AndyChiu/hotswap_pcb_generator/img_UTP/IMG_20230121_120708471~2.jpg

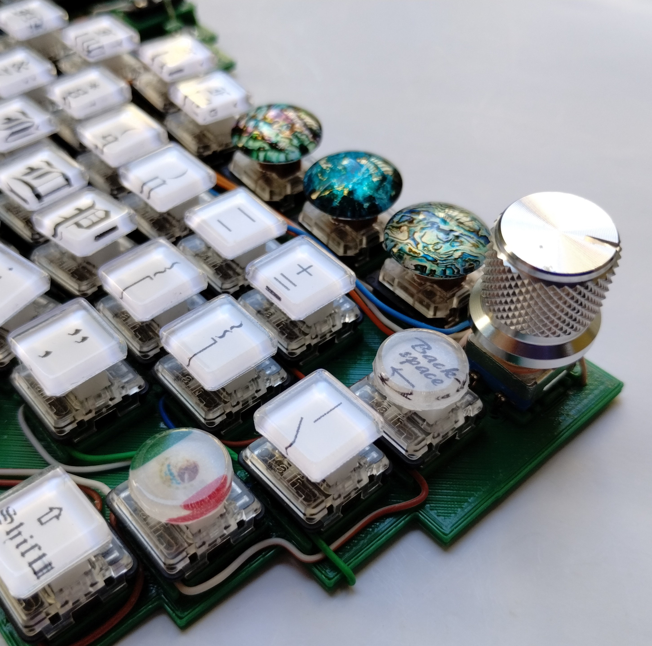
img_UTP/IMG_20230121_120708471~2.jpg
