AndyChiu/hotswap_pcb_generator/example_layouts_UTP/Willow-3x6+Esrille-thumb-3x1_(V2 Curve)/pcb_Willow-3x6-Esrille-thumb-3x1_(V2 Curve)_R.stl

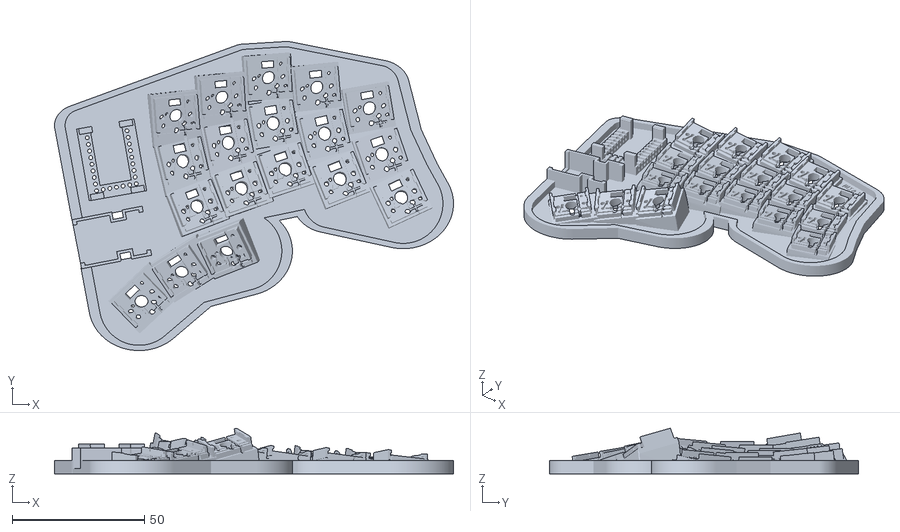
[picture p60: CAD file, 2024-08-21]
example_layouts_UTP/Willow-3x6+Esrille-thumb-3x1_(V2 Curve)/pcb_Willow-3x6-Esrille-thumb-3x1_(V2 Curve)_R.stl
150.7 x 116.7 x 17.2
