AndyChiu/hotswap_pcb_generator/scad_UTP/Curved_PCB_KB/STL/11.3MM_LType/BasePlate_3U_11.3MM_LType_Left.stl

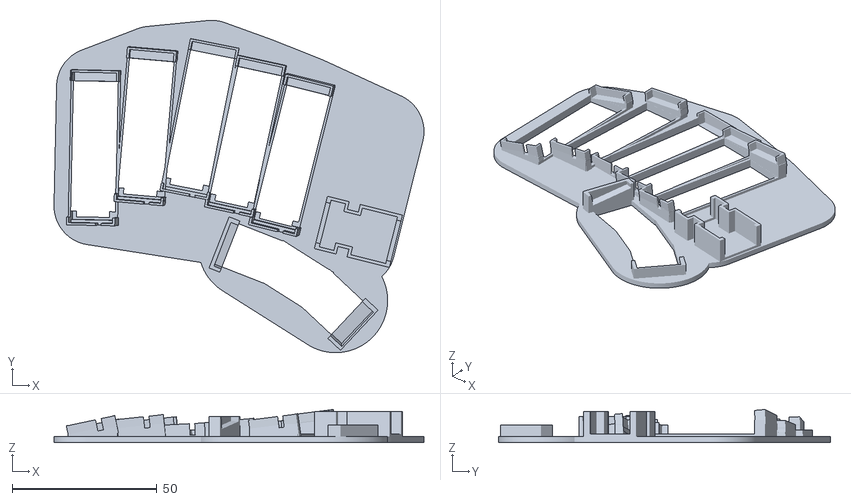
[picture p61: CAD file, 2024-03-19]
scad_UTP/Curved_PCB_KB/STL/11.3MM_LType/BasePlate_3U_11.3MM_LType_Left.stl
127.9 x 114.9 x 11.4
