AndyChiu/hotswap_pcb_generator/scad_UTP/Curved_PCB_KB/STL/13MM_MType/Curved_PCB(UC36_3U)_M_13mm.stl

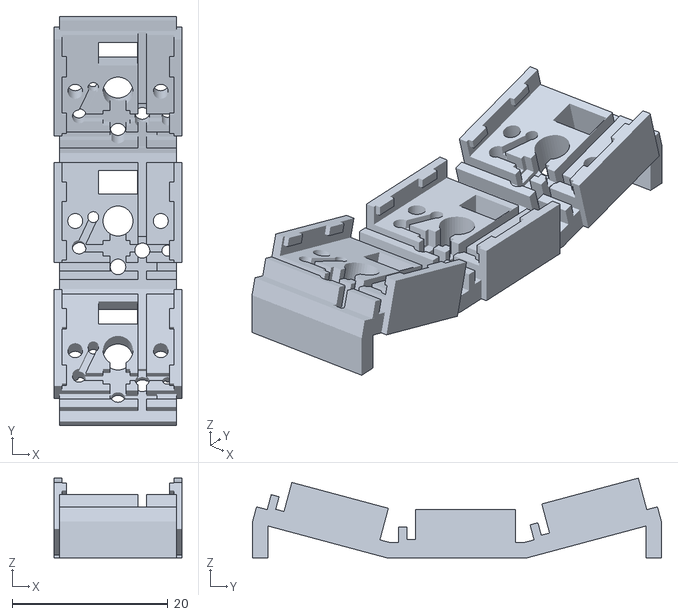
[picture p62: CAD file, 2024-03-19]
scad_UTP/Curved_PCB_KB/STL/13MM_MType/Curved_PCB(UC36_3U)_M_13mm.stl
16.4 x 52.6 x 10.3
