AndyChiu/hotswap_pcb_generator/scad_UTP/Curved_PCB_KB/STL/16MM_MType/BasePlate_3U_16MM_MType_Left.stl

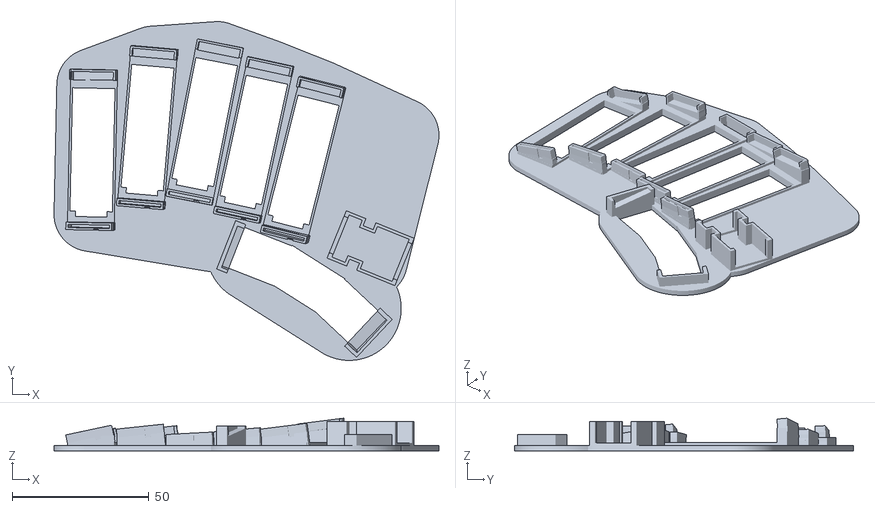
[picture p64: CAD file, 2024-03-19]
scad_UTP/Curved_PCB_KB/STL/16MM_MType/BasePlate_3U_16MM_MType_Left.stl
140.6 x 123.7 x 11.9
