AndyChiu/hotswap_pcb_generator/scad_UTP/Curved_PCB_KB/STL/18MM_LType/BasePlate_3U_18MM_LType_Right.stl

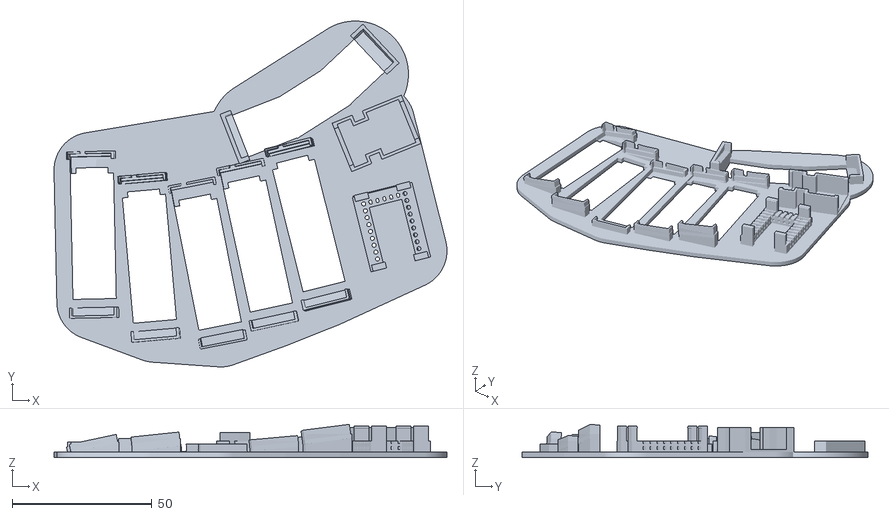
[picture p65: CAD file, 2024-03-19]
scad_UTP/Curved_PCB_KB/STL/18MM_LType/BasePlate_3U_18MM_LType_Right.stl
140.6 x 123.7 x 11.9
