AndyChiu/hotswap_pcb_generator/scad_UTP/IDC/STL/IDC_Holder.stl

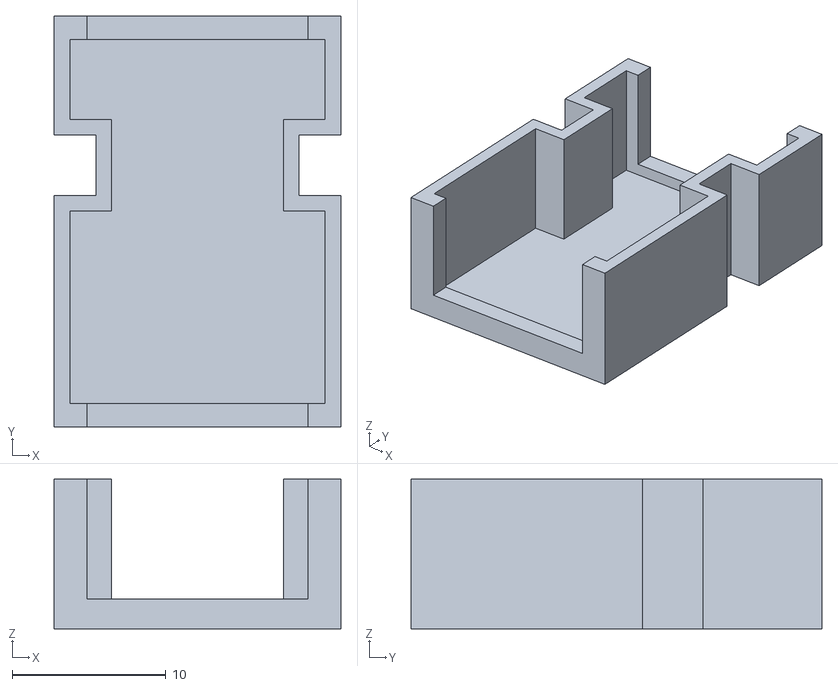
[picture p66: CAD file, 2024-03-19]
scad_UTP/IDC/STL/IDC_Holder.stl
18.7 x 26.8 x 9.74
