AndyChiu/hotswap_pcb_generator/stl_UTP/Keycaps/MX/LP/LP_2UL.stl

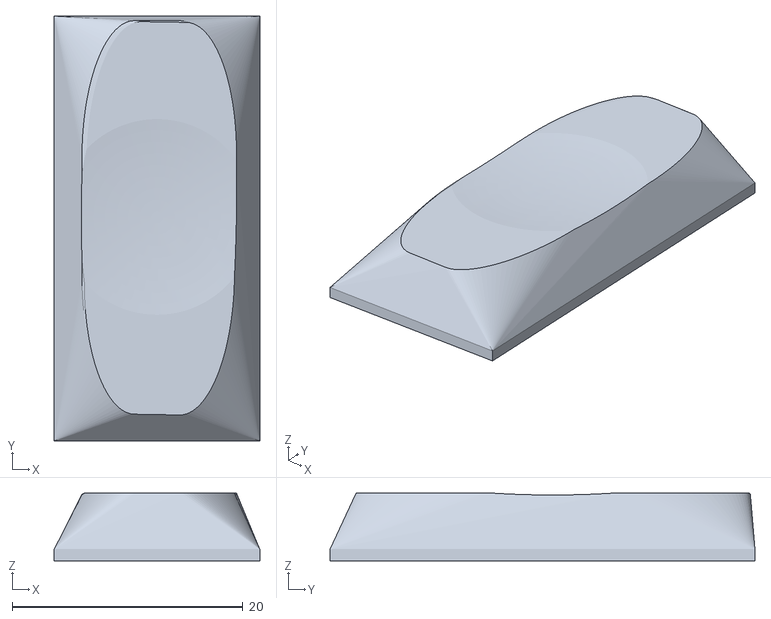
[picture p68: CAD file, 2026-04-29]
stl_UTP/Keycaps/MX/LP/LP_2UL.stl
17.8 x 36.8 x 5.85
