AndyChiu/hotswap_pcb_generator/stl_UTP/MCU/mcu_ProMicro_C.stl

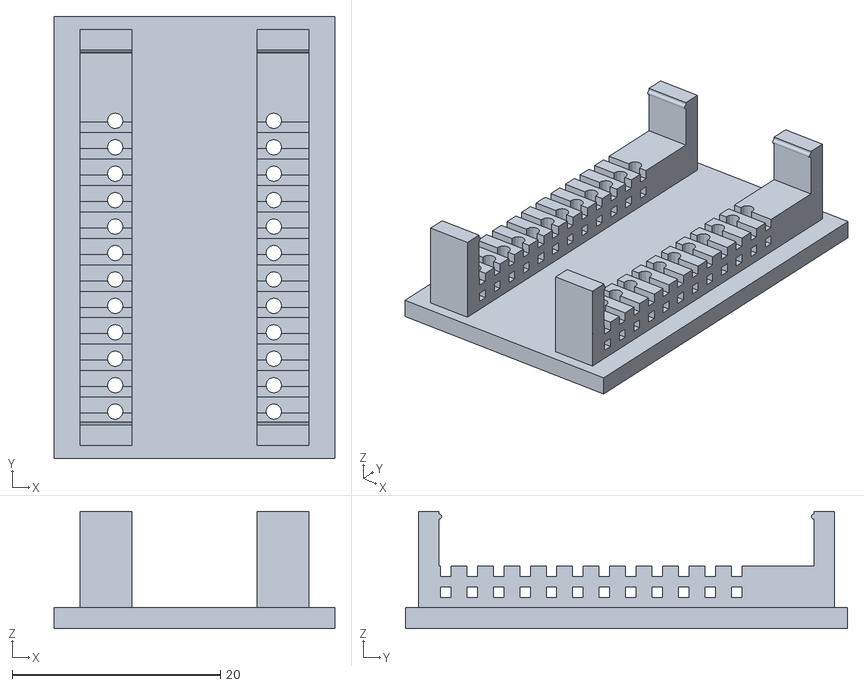
[picture p69: CAD file, 2024-03-01]
stl_UTP/MCU/mcu_ProMicro_C.stl
27.0 x 42.5 x 11.2
