AndyChiu/hotswap_pcb_generator/stl_UTP/Other/trrs.stl

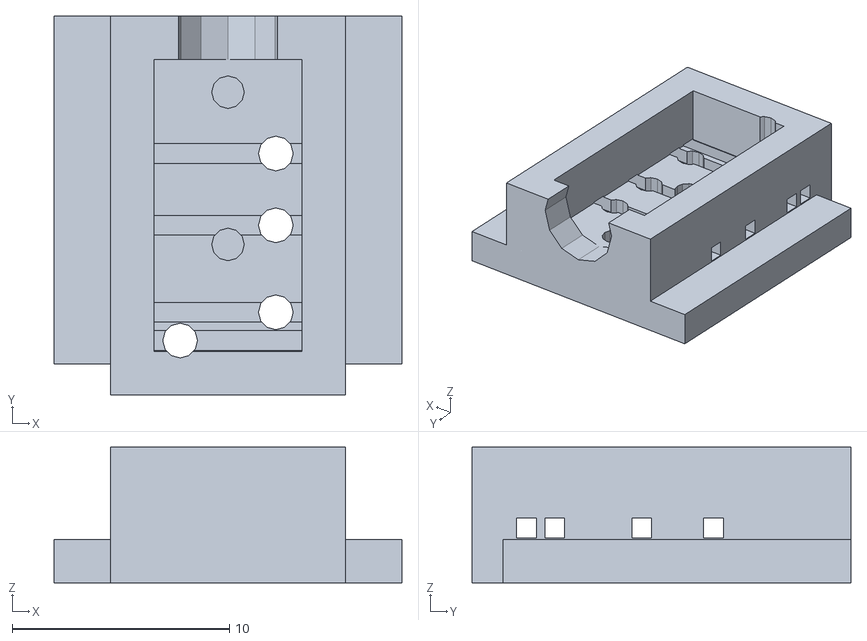
[picture p70: CAD file, 2022-04-29]
stl_UTP/Other/trrs.stl
16.0 x 17.4 x 6.24
