AndyChiu/hotswap_pcb_generator/scad_UTP/Curved_PCB_KB/STL/13MM_MType/pcb_TH_16MM.stl

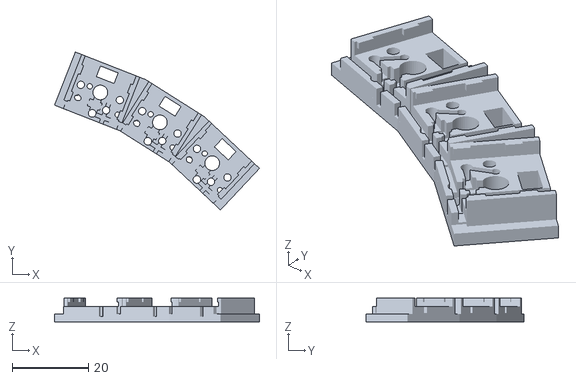
[picture p72: CAD file, 2024-03-19]
scad_UTP/Curved_PCB_KB/STL/13MM_MType/pcb_TH_16MM.stl
53.9 x 41.5 x 6.20
