AndyChiu/hotswap_pcb_generator/scad_UTP/Curved_PCB_KB/STL/16MM_LType/BasePlate_3U_16MM_LType_Right.stl

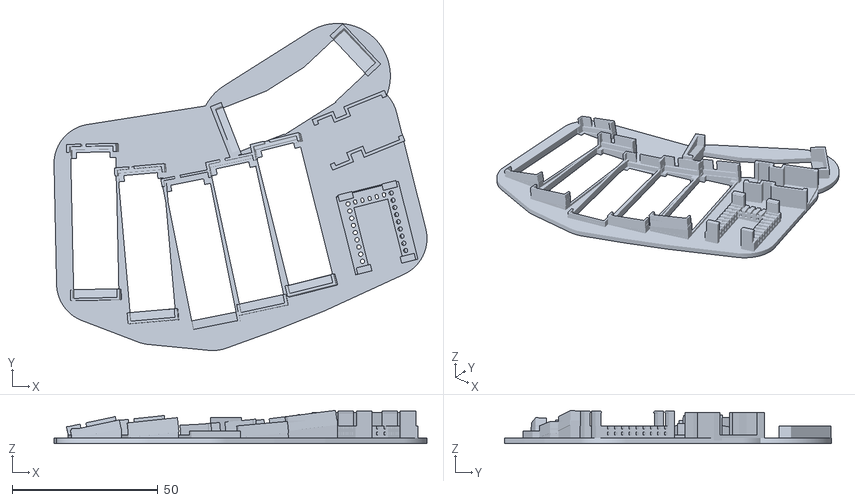
[picture p73: CAD file, 2024-03-19]
scad_UTP/Curved_PCB_KB/STL/16MM_LType/BasePlate_3U_16MM_LType_Right.stl
127.9 x 112.2 x 11.4
