AndyChiu/hotswap_pcb_generator/scad_UTP/IDC/STL/DJ_Holder.stl

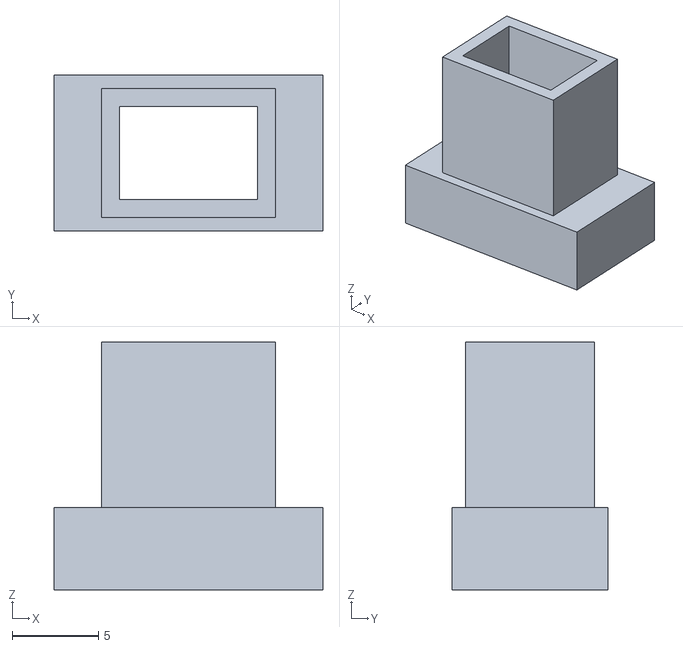
[picture p75: CAD file, 2024-03-19]
scad_UTP/IDC/STL/DJ_Holder.stl
15.6 x 9.05 x 14.4
