AndyChiu/hotswap_pcb_generator/stl_UTP/Keycaps/Choc/AndyChiu/05_circle_M_N4(HB)-0610_center.stl

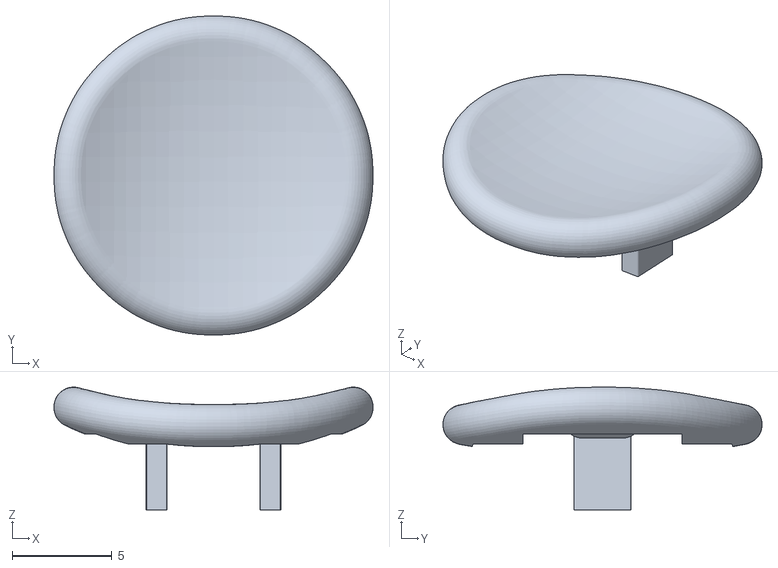
[picture p76: CAD file, 2026-02-17]
stl_UTP/Keycaps/Choc/AndyChiu/05_circle_M_N4(HB)-0610_center.stl
16.0 x 16.0 x 6.16
