AndyChiu/hotswap_pcb_generator/stl_UTP/MCU/mcu_RP2040_Pico.stl

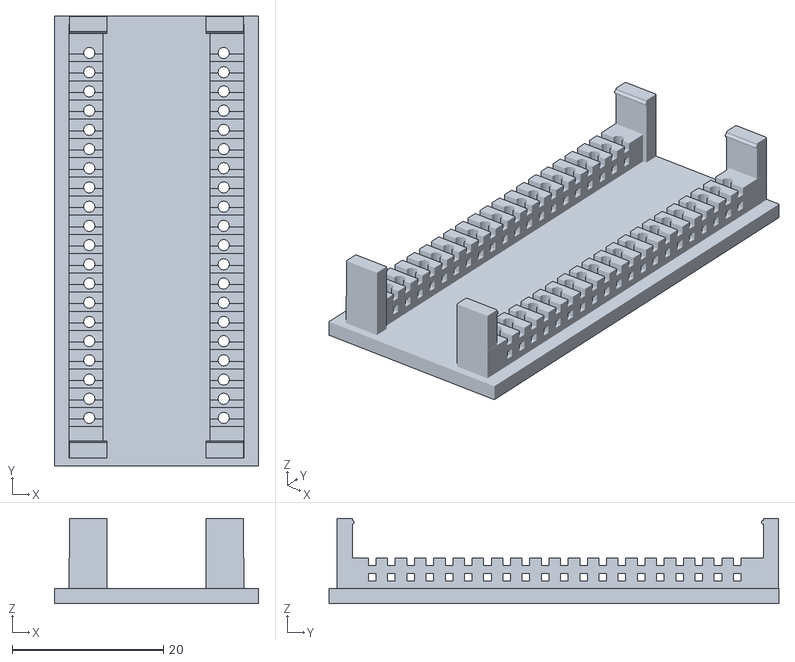
[picture p78: CAD file, 2024-03-01]
stl_UTP/MCU/mcu_RP2040_Pico.stl
27.0 x 59.5 x 11.2
