AndyChiu/hotswap_pcb_generator/stl_UTP/Other/ec11.stl

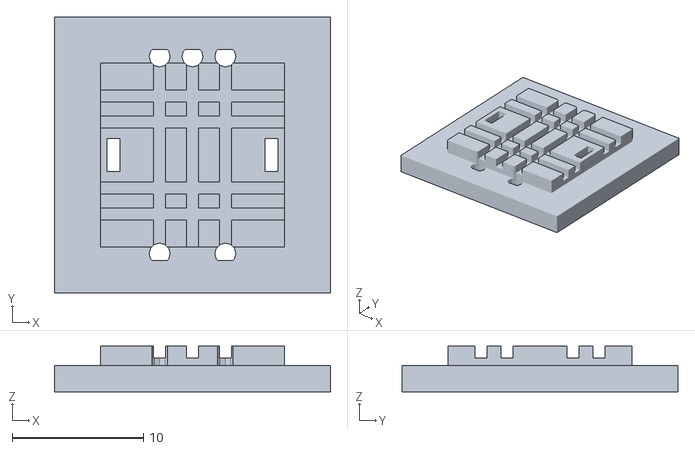
[picture p79: CAD file, 2022-04-29]
stl_UTP/Other/ec11.stl
21.0 x 21.0 x 3.50
