AndyChiu/hotswap_pcb_generator/scad_UTP/Curved_PCB_KB/STL/11.3MM_LType/Curved_PCB(UC36_3U)_M2_11.4mm_High.stl

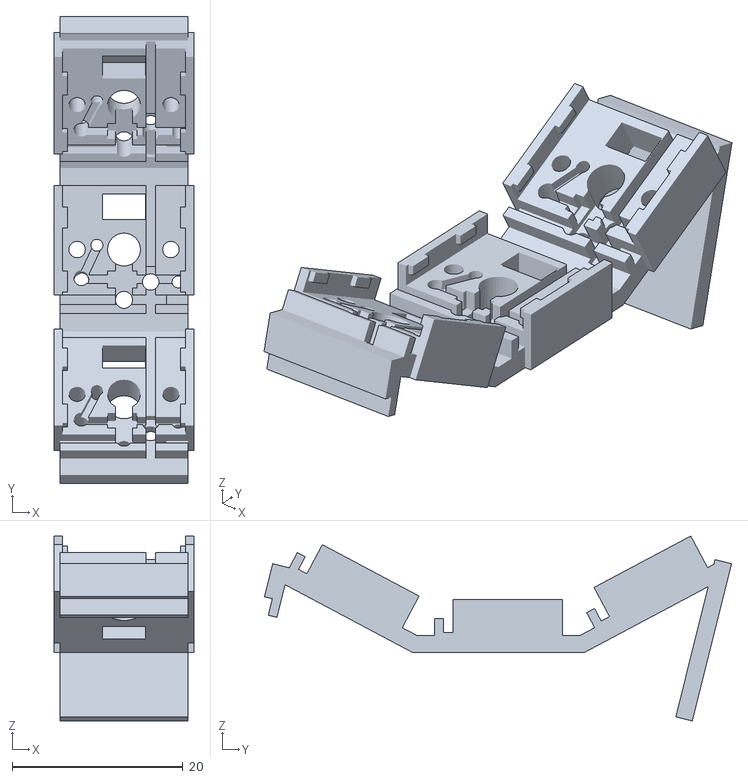
[picture p80: CAD file, 2024-03-19]
scad_UTP/Curved_PCB_KB/STL/11.3MM_LType/Curved_PCB(UC36_3U)_M2_11.4mm_High.stl
16.4 x 54.8 x 21.7
