AndyChiu/hotswap_pcb_generator/scad_UTP/Curved_PCB_KB/STL/13MM_MType/BasePlate_3U_16MM_MType_Left.stl

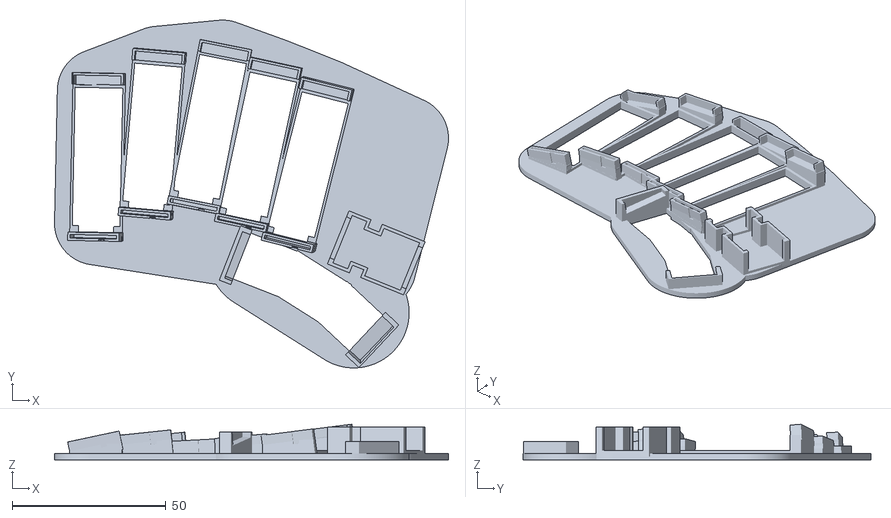
[picture p81: CAD file, 2024-03-19]
scad_UTP/Curved_PCB_KB/STL/13MM_MType/BasePlate_3U_16MM_MType_Left.stl
128.2 x 113.1 x 11.6
