AndyChiu/hotswap_pcb_generator/scad_UTP/Curved_PCB_KB/STL/16MM_MType/Curved_PCB(UC36_3U)_M_13mm_on_16.3mmBase.stl

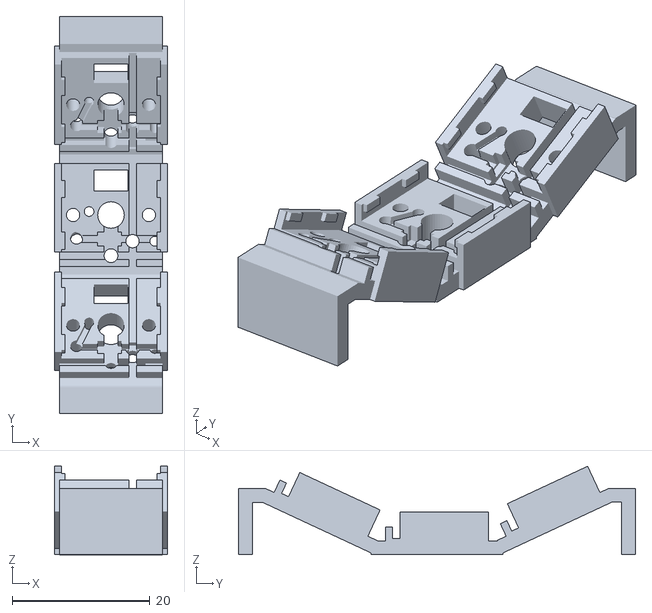
[picture p82: CAD file, 2024-03-19]
scad_UTP/Curved_PCB_KB/STL/16MM_MType/Curved_PCB(UC36_3U)_M_13mm_on_16.3mmBase.stl
16.4 x 57.6 x 12.8
