AndyChiu/hotswap_pcb_generator/scad_UTP/Curved_PCB_KB/STL/18MM_LType/Curved_PCB(UC36_3U)_L_16.3mm.stl

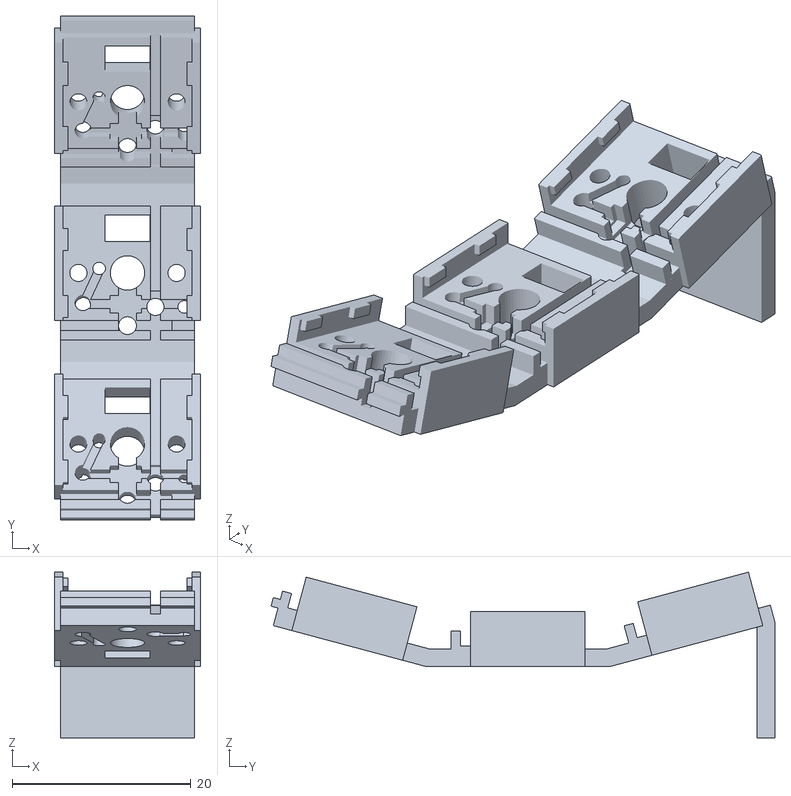
[picture p83: CAD file, 2024-03-19]
scad_UTP/Curved_PCB_KB/STL/18MM_LType/Curved_PCB(UC36_3U)_L_16.3mm.stl
16.4 x 56.4 x 18.6
