AndyChiu/hotswap_pcb_generator/scad_UTP/IDC/STL/DJ_HolderTail.stl

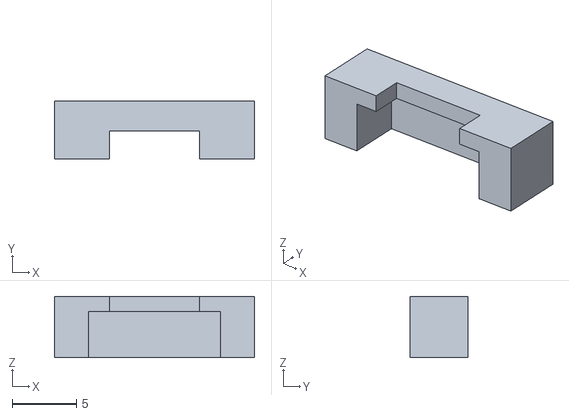
[picture p84: CAD file, 2024-03-19]
scad_UTP/IDC/STL/DJ_HolderTail.stl
15.6 x 4.52 x 4.78
