AndyChiu/hotswap_pcb_generator/stl_UTP/Keycaps/Choc/AndyChiu/02-CF-T1-01.stl

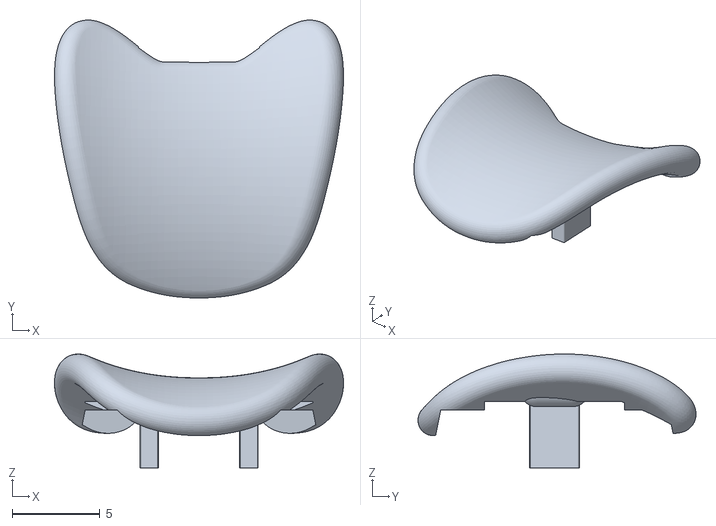
[picture p85: CAD file, 2026-02-17]
stl_UTP/Keycaps/Choc/AndyChiu/02-CF-T1-01.stl
16.5 x 15.9 x 6.50
