AndyChiu/hotswap_pcb_generator/stl_UTP/Keycaps/MX/LP/LP_CapsLock.stl

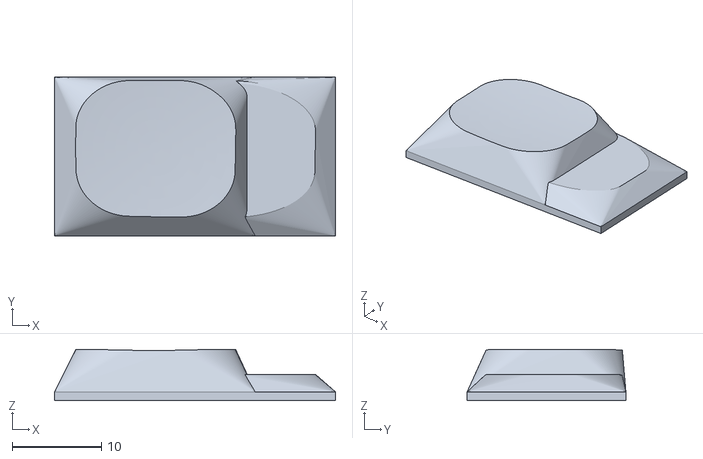
[picture p86: CAD file, 2026-04-29]
stl_UTP/Keycaps/MX/LP/LP_CapsLock.stl
31.5 x 17.8 x 5.77
