AndyChiu/hotswap_pcb_generator/stl_UTP/MCU/mcu_RP2040_Zero.stl

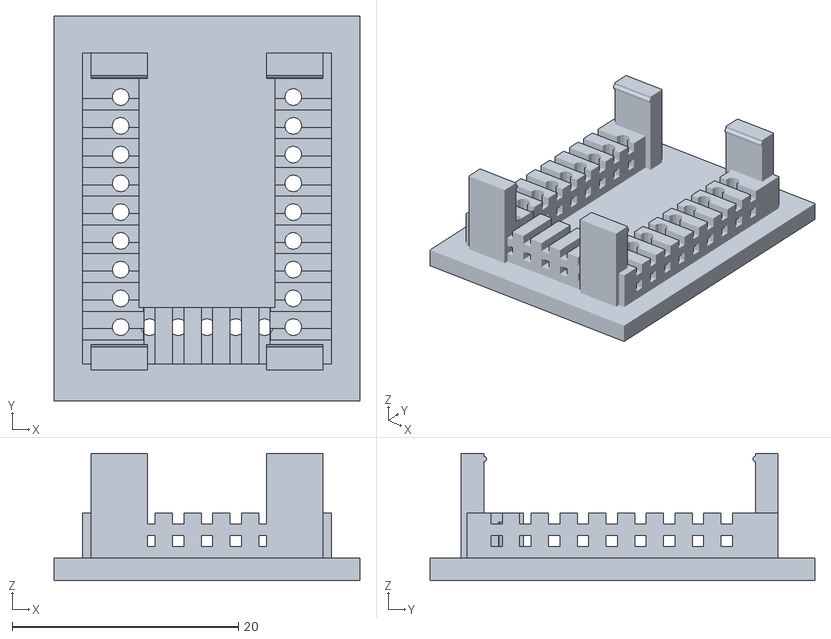
[picture p87: CAD file, 2024-03-01]
stl_UTP/MCU/mcu_RP2040_Zero.stl
27.0 x 34.0 x 11.2
