AndyChiu/hotswap_pcb_generator/stl_UTP/Other/stabilizer_chocv2.stl

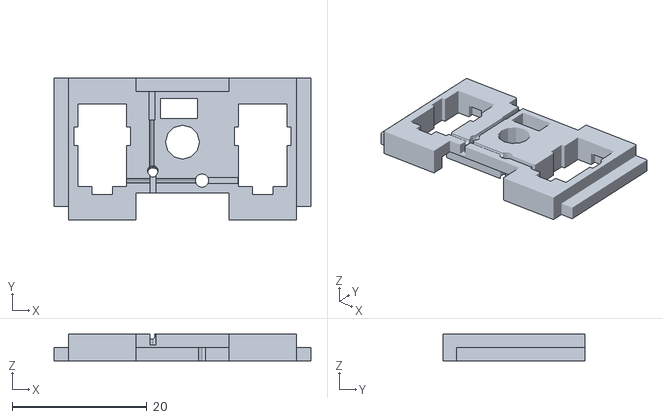
[picture p88: CAD file, 2022-04-29]
stl_UTP/Other/stabilizer_chocv2.stl
38.1 x 21.1 x 4.00
