AndyChiu/hotswap_pcb_generator/scad_UTP/Curved_PCB_KB/STL/16MM_MType/BasePlate_3U_16MM_MType_Right.stl

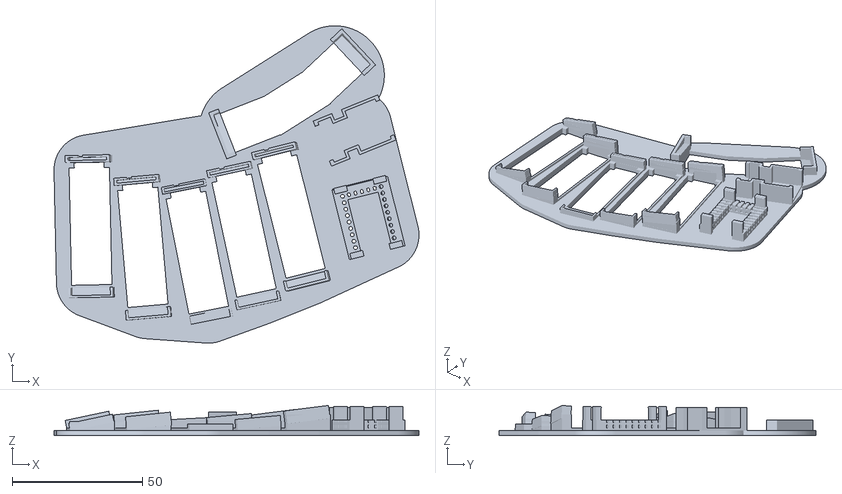
[picture p89: CAD file, 2024-03-19]
scad_UTP/Curved_PCB_KB/STL/16MM_MType/BasePlate_3U_16MM_MType_Right.stl
140.1 x 121.8 x 11.6
