AndyChiu/hotswap_pcb_generator/stl_UTP/Keycaps/Choc/AndyChiu/05_1210-20x18.stl

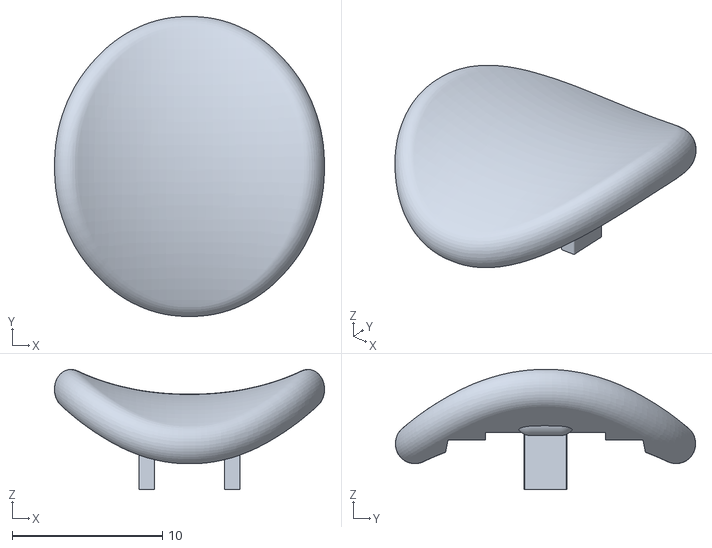
[picture p90: CAD file, 2026-02-17]
stl_UTP/Keycaps/Choc/AndyChiu/05_1210-20x18.stl
18.0 x 20.0 x 8.01
