AndyChiu/hotswap_pcb_generator/stl_UTP/Keycaps/MX/LP/LP_1.25U.stl

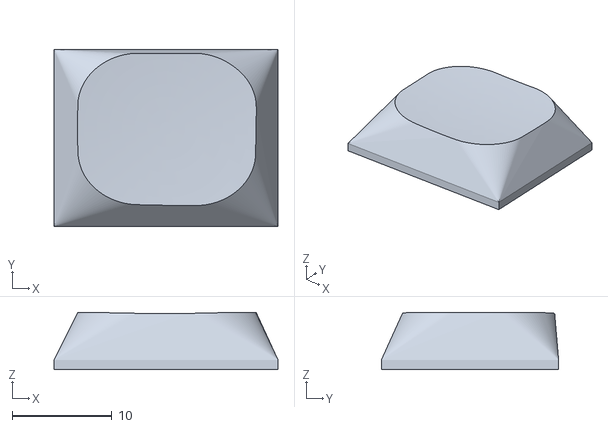
[picture p91: CAD file, 2026-04-29]
stl_UTP/Keycaps/MX/LP/LP_1.25U.stl
22.5 x 17.8 x 5.77
