AndyChiu/hotswap_pcb_generator/scad_UTP/Curved_PCB_KB/STL/11.3MM_LType/Curved_PCB(UC36_3U)_M2_11.4mm.stl

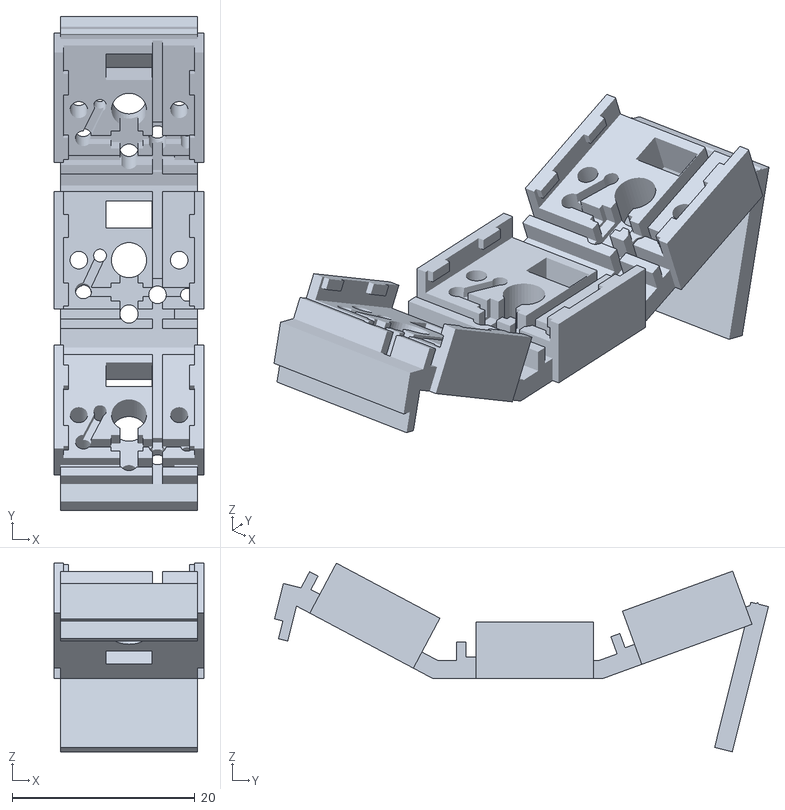
[picture p93: CAD file, 2024-03-19]
scad_UTP/Curved_PCB_KB/STL/11.3MM_LType/Curved_PCB(UC36_3U)_M2_11.4mm.stl
16.4 x 54.1 x 20.7
