AndyChiu/hotswap_pcb_generator/stl_UTP/Keycaps/Choc/AndyChiu/05-16x16.stl

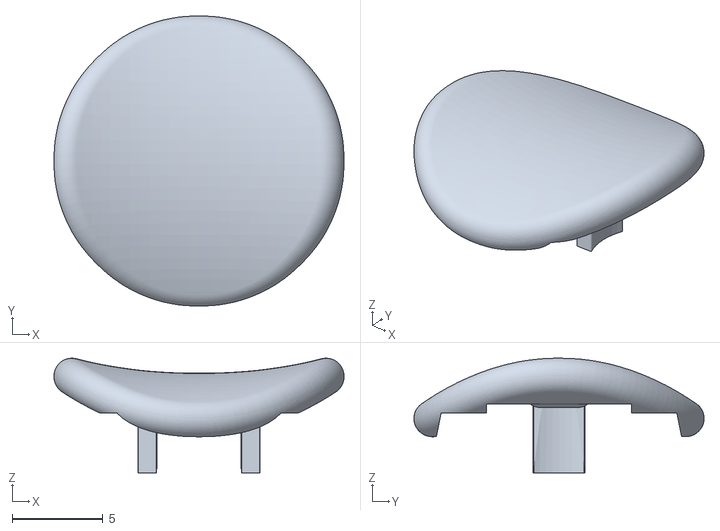
[picture p94: CAD file, 2026-02-17]
stl_UTP/Keycaps/Choc/AndyChiu/05-16x16.stl
16.0 x 16.0 x 6.32
