AndyChiu/hotswap_pcb_generator/stl_UTP/Keycaps/MX/LP/LP_ISO105Enter.stl

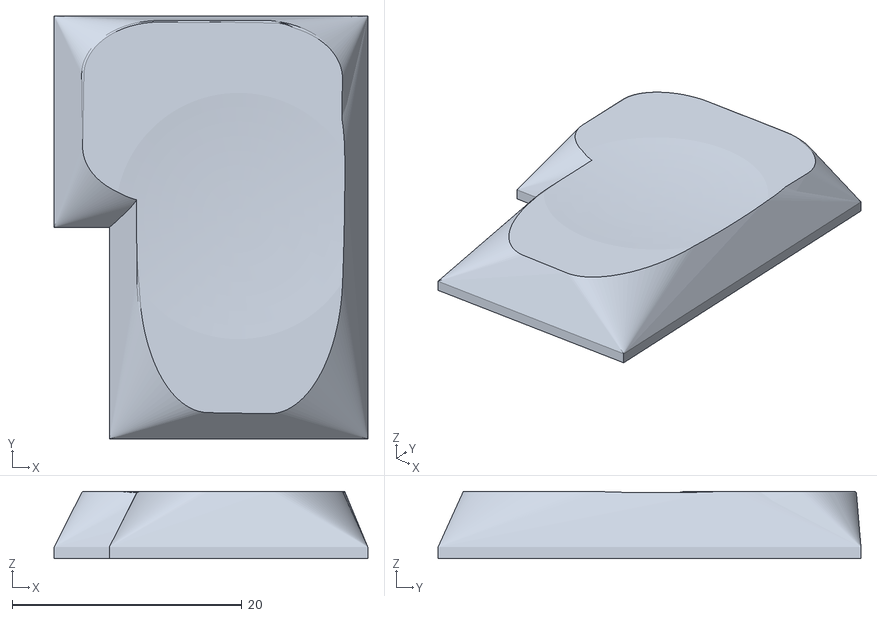
[picture p95: CAD file, 2026-04-29]
stl_UTP/Keycaps/MX/LP/LP_ISO105Enter.stl
27.3 x 36.8 x 5.85
