AndyChiu/hotswap_pcb_generator/stl_UTP/Switch/switch_chocMini.stl

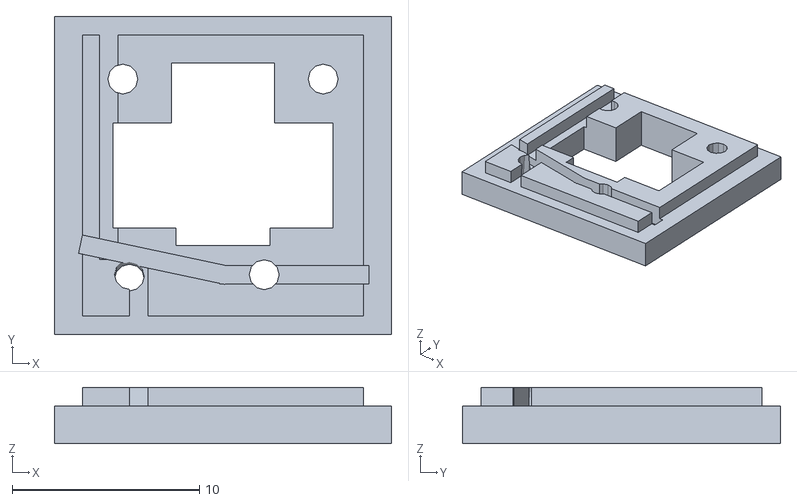
[picture p96: CAD file, 2024-03-01]
stl_UTP/Switch/switch_chocMini.stl
18.0 x 17.0 x 3.00
