AndyChiu/hotswap_pcb_generator/stl_UTP/Keycaps/MX/LP/LP_3U.stl

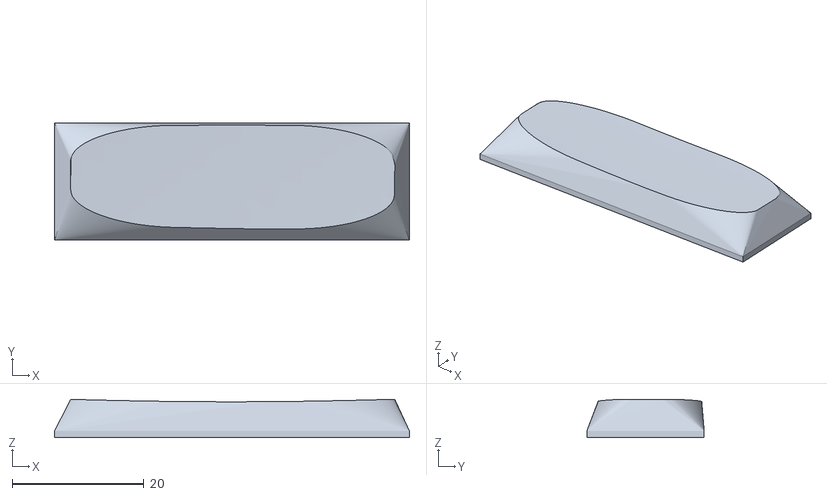
[picture p97: CAD file, 2026-04-29]
stl_UTP/Keycaps/MX/LP/LP_3U.stl
53.8 x 17.8 x 5.82
