AndyChiu/hotswap_pcb_generator/stl_UTP/Switch/switch_chocV2_1u.stl

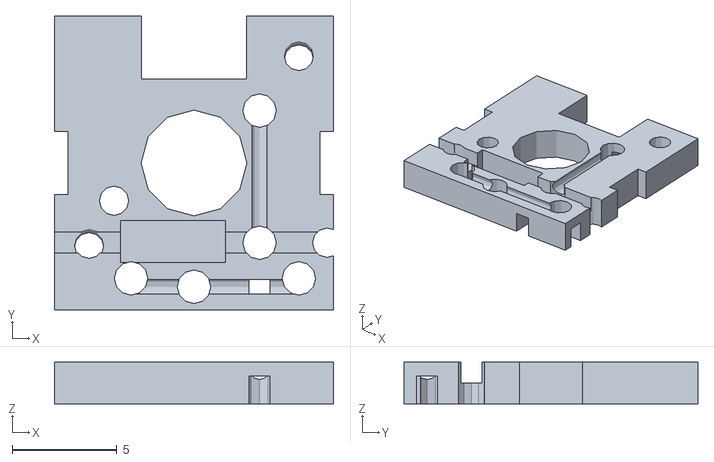
[picture p98: CAD file, 2024-03-01]
stl_UTP/Switch/switch_chocV2_1u.stl
13.3 x 14.0 x 2.00
