AndyChiu/hotswap_pcb_generator/stl_UTP/Keycaps/MX/LP/LP_1U.stl

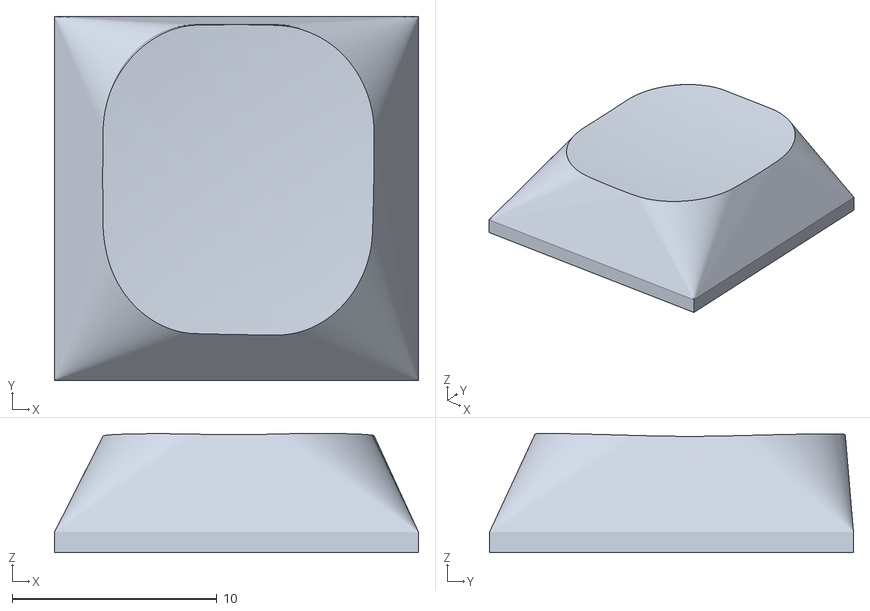
[picture p99: CAD file, 2026-04-29]
stl_UTP/Keycaps/MX/LP/LP_1U.stl
17.8 x 17.8 x 5.82
