AndyChiu/hotswap_pcb_generator/stl_UTP/Switch/switch_mx_holder.stl

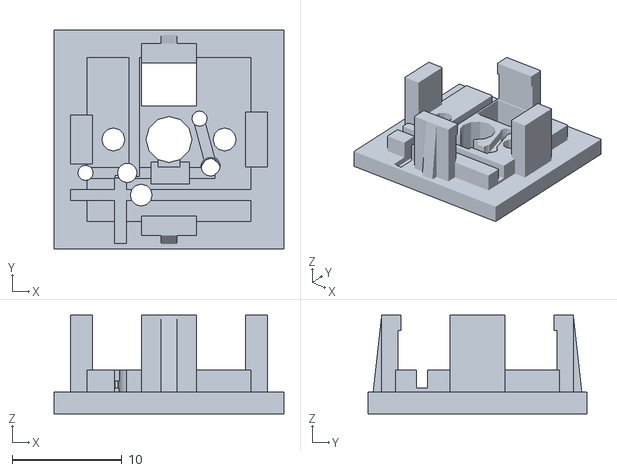
[picture p100: CAD file, 2024-03-01]
stl_UTP/Switch/switch_mx_holder.stl
21.0 x 20.0 x 9.00
