AndyChiu/hotswap_pcb_generator/stl_UTP/Keycaps/MX/LP/LP_2.5U.stl

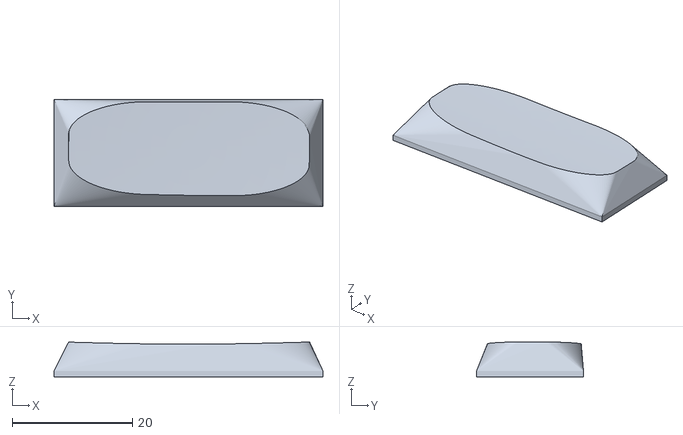
[picture p101: CAD file, 2026-04-29]
stl_UTP/Keycaps/MX/LP/LP_2.5U.stl
44.8 x 17.8 x 5.81
