AndyChiu/hotswap_pcb_generator/stl_UTP/Switch/switch_chocV2.stl

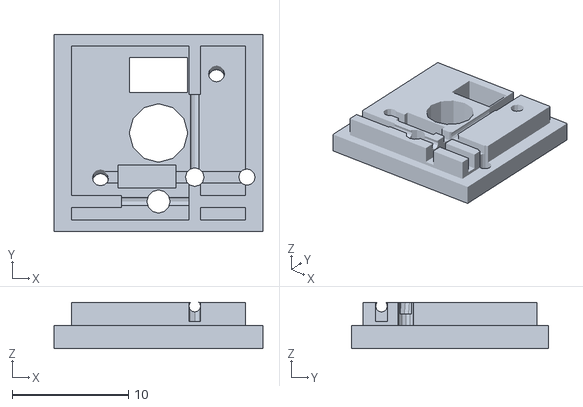
[picture p102: CAD file, 2024-03-01]
stl_UTP/Switch/switch_chocV2.stl
18.0 x 17.0 x 4.00
