AndyChiu/hotswap_pcb_generator/stl_UTP/Keycaps/MX/LP/LP_1.5UL.stl

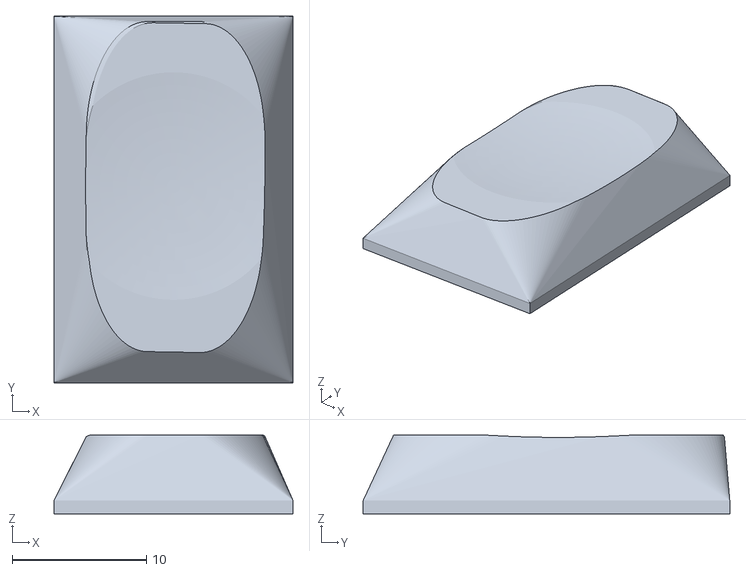
[picture p103: CAD file, 2026-04-29]
stl_UTP/Keycaps/MX/LP/LP_1.5UL.stl
17.8 x 27.3 x 5.85
