AndyChiu/hotswap_pcb_generator/stl_UTP/Keycaps/MX/LP/LP_1UHB.stl

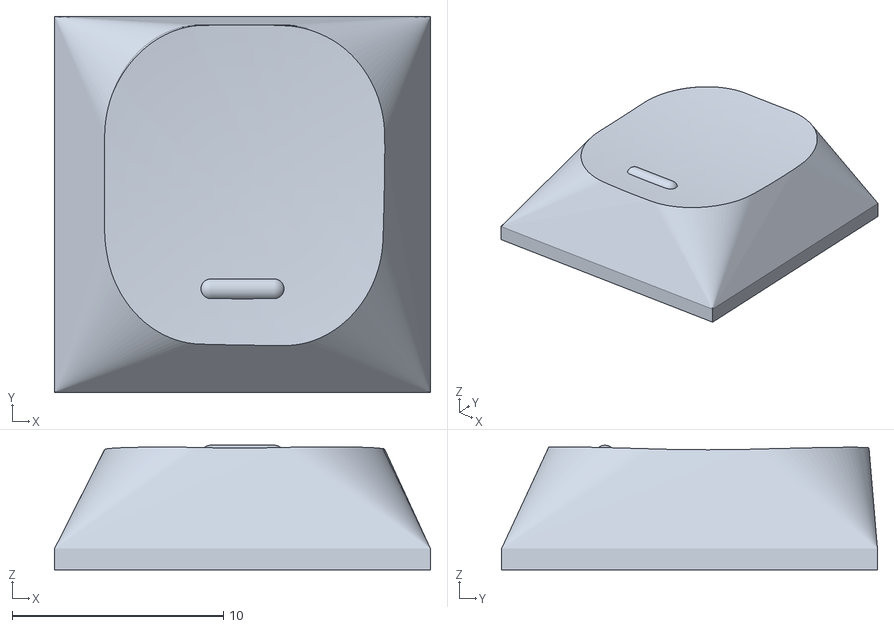
[picture p104: CAD file, 2026-04-29]
stl_UTP/Keycaps/MX/LP/LP_1UHB.stl
17.8 x 17.8 x 5.90
