AndyChiu/hotswap_pcb_generator/stl_UTP/Keycaps/MX/LP/LP_BigAssEnter.stl

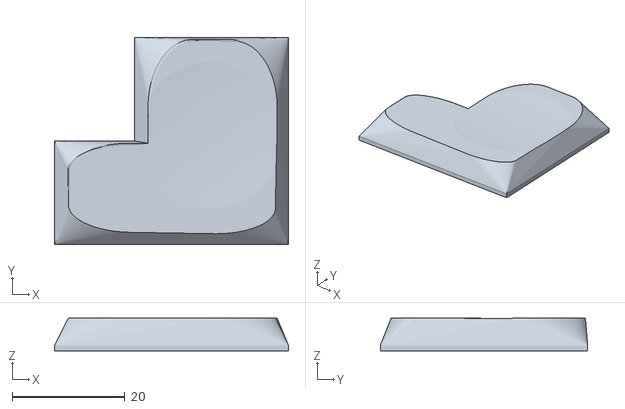
[picture p105: CAD file, 2026-04-29]
stl_UTP/Keycaps/MX/LP/LP_BigAssEnter.stl
41.5 x 36.8 x 5.85
