AndyChiu/hotswap_pcb_generator/stl_UTP/Keycaps/MX/LP/LP_2.75U.stl

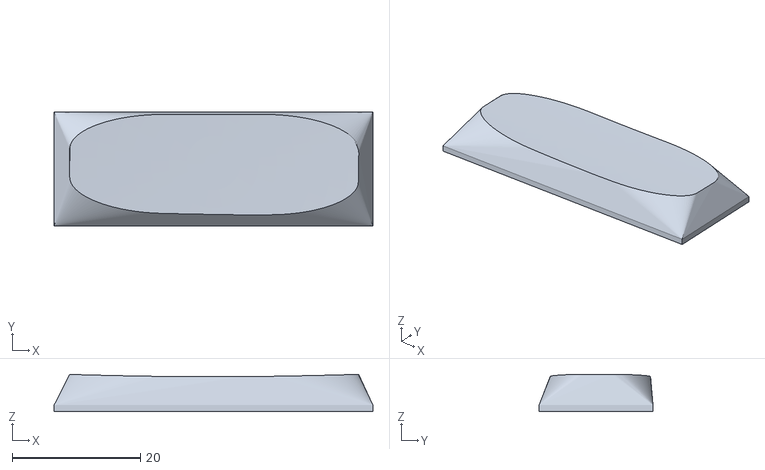
[picture p106: CAD file, 2026-04-29]
stl_UTP/Keycaps/MX/LP/LP_2.75U.stl
49.8 x 17.8 x 5.82
