AndyChiu/hotswap_pcb_generator/stl_UTP/Keycaps/MX/LP/LP_6.25U.stl

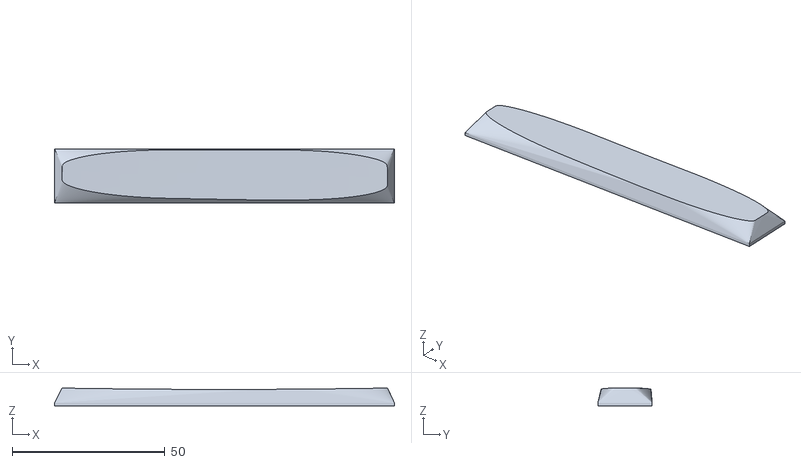
[picture p107: CAD file, 2026-04-29]
stl_UTP/Keycaps/MX/LP/LP_6.25U.stl
111.2 x 17.8 x 5.85
