AndyChiu/hotswap_pcb_generator/stl_UTP/Keycaps/MX/LP/LP_1.75U.stl

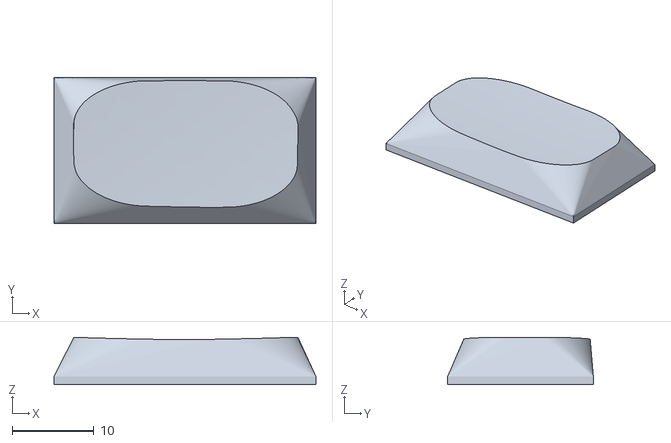
[picture p108: CAD file, 2026-04-29]
stl_UTP/Keycaps/MX/LP/LP_1.75U.stl
32.0 x 17.8 x 5.78
