AndyChiu/hotswap_pcb_generator/stl_UTP/Keycaps/MX/LP/LP_7U.stl

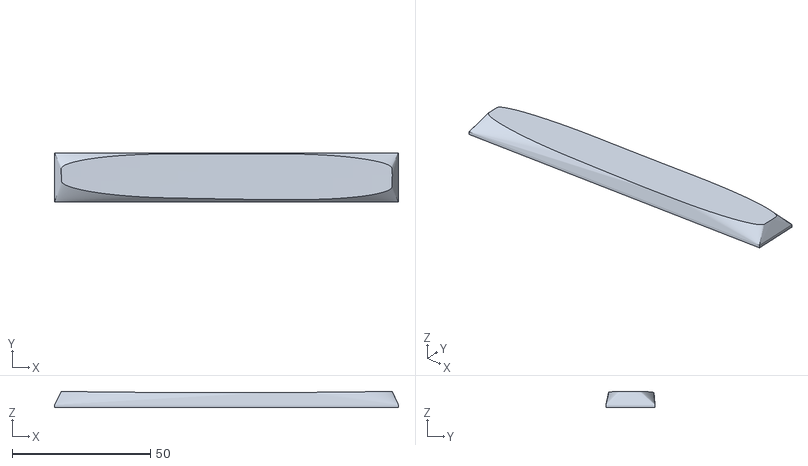
[picture p109: CAD file, 2026-04-29]
stl_UTP/Keycaps/MX/LP/LP_7U.stl
124.5 x 17.8 x 5.85
