AndyChiu/hotswap_pcb_generator/scad_UTP/parameters_trrs_pj320a.scad

trrs_type = "pj320a";
// add * 1.1
trrs_width = 6.2 * 1.1;
trrs_length = 12.2 * 1.1;
trrs_height = 5;
trrs_flange_length = 2;
trrs_flange_diameter = 5;
trrs_pin_spacing = 4.4;
trrs_nub_diameter = 1.5;  // Little locating nubs on the bottom of the socket
trrs_nub_height = 1;
trrs_nub_spacing = 7;
trrs_nub_offset = 1.5;  // Distance from the front of the socket (not including flange)
trrs_plug_width = 10;  // Width of a plug for plate clearance
