AndyChiu/hotswap_pcb_generator/scad_UTP/backplate.scad

include <parameters.scad>
include <utils.scad>

use <switch.scad>
use <mcu.scad>
use <ec11.scad>
use <evqwgd001.scad>
use <trrs.scad>
use <stabilizer.scad>
use <standoff.scad>
use <plate.scad>
use <case.scad>

module backplate_footprint(switch_layout, mcu_layout, ec11_layout, evqwgd001_layout, trrs_layout, plate_layout, stab_layout) {
    case_height = total_thickness - backplate_case_flange;
    bottom_offset = use_plate_layout_only
        ? 0
        : tan(case_wall_draft_angle) * (case_height-case_base_height);
    if (tent_angle_x == 0 && tent_angle_y == 0) {
        offset(bottom_offset)
            plate_footprint(switch_layout, mcu_layout, ec11_layout, evqwgd001_layout, trrs_layout, plate_layout, stab_layout);
    } else {
        offset(bottom_offset)
            plate_footprint(switch_layout, mcu_layout, ec11_layout, evqwgd001_layout, trrs_layout, plate_layout, stab_layout);
    }
}

module backplate_base(switch_layout, mcu_layout, ec11_layout, evqwgd001_layout, trrs_layout, plate_layout, stab_layout, thickness=plate_thickness) {
    difference() {
        translate([0,0,-500])
        linear_extrude(thickness+999, center=true, convexity=10)
            backplate_footprint(switch_layout, mcu_layout, ec11_layout, evqwgd001_layout,trrs_layout, plate_layout, stab_layout);
        translate([tent_point[0]-plate_margin,plate_margin-tent_point[1],-thickness/2])
        rotate([-tent_angle_x, tent_angle_y,0])
        translate([-1000,-1000,-1000])
            cube([2000,2000,1000]);
    }
}

module backplate(switch_layout, mcu_layout, ec11_layout, evqwgd001_layout, trrs_layout, plate_layout, stab_layout, standoff_layout) {
    difference() {
        union() {
            if (case_type == "sandwich") {
                backplate_base(switch_layout, mcu_layout, ec11_layout, evqwgd001_layout, trrs_layout, plate_layout, stab_layout, backplate_thickness);
            } else if (case_type == "plate_case") {
                plate_base(switch_layout, mcu_layout, ec11_layout, evqwgd001_layout, trrs_layout, plate_layout, stab_layout, backplate_thickness, -case_wall_thickness-case_fit_tolerance);
                translate([0,0,(backplate_case_flange-backplate_thickness)/2])
                    backplate_base(switch_layout, mcu_layout, ec11_layout, evqwgd001_layout, trrs_layout, plate_layout, stab_layout, backplate_case_flange);
            }
            layout_pattern(standoff_layout) {
                backplate_standoff($extra_data);
            }
        }
        layout_pattern(standoff_layout) {
            backplate_standoff_hole($extra_data);
        }
    }
}

////intersection() {
//difference() {


backplate(switch_layout_final, mcu_layout_final, ec11_layout_final, evqwgd001_layout_final, trrs_layout_final, plate_layout_final, stab_layout_final, standoff_layout_final);
    
//union()
//{
//translate([-40, -190, -20]) {
//    rotate ([0,0,-10]) cube([250,130,40]);
//
//}
//}
//
//}
