AndyChiu/hotswap_pcb_generator/scad_UTP/layouts.scad

//include <default_layout.scad>
