AndyChiu/hotswap_pcb_generator/scad_UTP/mcu.scad

include <parameters.scad>
include <utils.scad>

use <grid_patterns.scad>

module mcu(borders=[0,0,0,0]) {
    translate([
        h_unit/2,
        -(mcu_v_unit_size*v_unit+mcu_socket_length)/2+2,
        0
    ]) rotate([0,layout_type == "row"?180:0,0]) translate([0,0,-pcb_thickness/2]) {
            if (mcu_type == "bare") {
                bare_mcu(invert_borders(borders,layout_type == "row"));
            } else if (mcu_type == "socketed") {
                socketed_mcu(invert_borders(borders,layout_type == "row"));
            } else if (mcu_type == "socketed2") {
                socketed_mcu2(invert_borders(borders,layout_type == "row"));            
            } else if (mcu_type == "socketed3") {
                socketed_mcu3(invert_borders(borders,layout_type == "row"));            
            } else {
                assert(false, "mcu_type is invalid");
            }
    }
}


module socketed_mcu(borders=[0,0,0,0]) {
    difference() {
        union() {
            // Base
            translate([-mcu_socket_width/2,-2,0]) 
                cube([mcu_socket_width,mcu_socket_length,pcb_thickness]);
            // Border
            translate([0,mcu_socket_length/2-2,pcb_thickness/2-1])
                border(
                    [mcu_h_unit_size*h_unit,mcu_v_unit_size*v_unit], 
                    borders, 
                    pcb_thickness-2
                );
            }
        // Wire Channels
        for (row = [-1,1]) {
            for (pin = [0:mcu_pin_count/2-1]) {
                translate([row*mcu_row_spacing/2,(pin+0.5)*mcu_pin_pitch,-wire_diameter/3]) 
                    cylinder(h=pcb_thickness,d=wire_diameter*2);
                translate([
                    row*(mcu_row_spacing/2-1),
                    (pin+0.5)*mcu_pin_pitch,
                    pcb_thickness-wire_diameter/3
                ]) rotate([0,row*90,0])
                    cylinder(h=1000,d=wire_diameter);
            }
        }
        
        if (mcu_name=="Elite_C") {
            iLastRow =(0+0.5)*mcu_pin_pitch;
    //        echo ("Last Row:",iLastRow);
            for (pin = [0:2]) {
                translate([(pin)*mcu_pin_pitch,iLastRow,-wire_diameter/3]) 
                    cylinder(h=pcb_thickness,d=wire_diameter*2);
                translate([-(pin)*mcu_pin_pitch,iLastRow,-wire_diameter/3]) 
                    cylinder(h=pcb_thickness,d=wire_diameter*2);
                translate([
                        (pin)*mcu_pin_pitch,iLastRow+wire_diameter,
                        pcb_thickness-wire_diameter/3
                    ]) rotate([90,-180,0])
                        cylinder(h=1000,d=wire_diameter);
                translate([
                        -(pin)*mcu_pin_pitch,iLastRow+wire_diameter,
                        pcb_thickness-wire_diameter/3
                    ]) rotate([90,-180,0])
                        cylinder(h=1000,d=wire_diameter);
            }
        }
    }

     // Retention Tabs
    for (x = [-1,1]) {
        translate([x*(mcu_width+mcu_connector_width)/4,0,(pcb_thickness+mcu_height+1)/2]) {
            for (y = [-1,mcu_length+1]) {
                translate([0,y,0])
                    cube(
                        [(mcu_width-mcu_connector_width)/2,2,pcb_thickness+mcu_height+1],
                        center=true
                    );
            }
        }
    // hold the MCU 
        translate([x*(mcu_width+mcu_connector_width)/4,0,pcb_thickness+mcu_height+0.5]) {
            rotate([0,90,0]) {
                for (y = [0,mcu_length]) {
                translate([0,y,0]) 
                    cylinder(h=(mcu_width-mcu_connector_width)/2,d=0.5,center=true);
                }
            }
        }
    }

}

module socketed_mcu2(borders=[0,0,0,0]) {
    difference() {
        union() {
            // Base
            translate([-mcu_socket_width/2,-2,0]) 
                cube([mcu_socket_width,mcu_socket_length,mcu_base_thickness]);
            // Border
            translate([0,mcu_socket_length/2-2,pcb_thickness/2-1])
                border(
                    [mcu_h_unit_size*h_unit,mcu_v_unit_size*v_unit], 
                    borders, 
                    pcb_thickness-2
                );
            }
        
        //Center cube cut
        if (mcu_name=="Elite_C" || mcu_name=="RP2040_Zero") {
                translate([-(mcu_center_cube_cut_width)/2,(mcu_wire_channels_length/2)-2,pcb_thickness-2]) 
                cube([mcu_center_cube_cut_width,mcu_center_cube_cut_length+0.01,pcb_thickness+0.01]);
            
            
            } else {
                translate([-(mcu_center_cube_cut_width)/2,-2,pcb_thickness-2]) 
                cube([mcu_center_cube_cut_width,mcu_socket_length,pcb_thickness]);
                };
            
        // Wire Channels
        for (row = [-1,1]) {
            for (pin = [0:mcu_pin_count/2-1]) {
                translate([row*mcu_row_spacing/2,mcu_pin_offset+(pin+0.5)*mcu_pin_pitch,-0.01]) 
                    cylinder(h=mcu_base_thickness+0.02,d=wire_diameter*1.5);
                translate([
                    row*((mcu_row_spacing+mcu_wire_channels_length)/2-2),
                    mcu_pin_offset+(pin+0.25)*mcu_pin_pitch,
                    mcu_base_thickness-wire_diameter/2
                ]) rotate([0,row*90,0])
                cube([wire_diameter+0.01,wire_diameter,mcu_wire_channels_length],true);
                if (mcu_SecondWireChannels) {
                translate([
                    row*((mcu_row_spacing+mcu_wire_channels_length)/2-2),
                    mcu_pin_offset+(pin+0.25)*mcu_pin_pitch,
                    mcu_base_thickness-wire_diameter/2-wire_diameter*2
                ]) rotate([0,row*90,0])
                cube([wire_diameter,wire_diameter,mcu_wire_channels_length],true);
                }                
            }
        }
        
        if (mcu_name=="Elite_C" || mcu_name=="RP2040_Zero") {
            iLastRow =(0+0.5)*mcu_pin_pitch;
    //        echo ("Last Row:",iLastRow);
            for (pin = [0:2]) {
                translate([(pin)*mcu_pin_pitch,iLastRow,-0.01]) 
                    cylinder(h=mcu_base_thickness+0.02,d=wire_diameter*1.5);
                translate([-(pin)*mcu_pin_pitch,iLastRow,-0.01]) 
                    cylinder(h=mcu_base_thickness+0.02,d=wire_diameter*1.5);
                translate([
                        (pin)*mcu_pin_pitch,iLastRow+wire_diameter-mcu_wire_channels_length/2+2,
                        mcu_base_thickness-wire_diameter/2
                    ]) rotate([90,-180,0])
                cube([wire_diameter,wire_diameter+0.01,mcu_wire_channels_length],true);
                translate([
                        -(pin)*mcu_pin_pitch,iLastRow+wire_diameter-mcu_wire_channels_length/2+2,
                        mcu_base_thickness-wire_diameter/2
                    ]) rotate([90,0,0])
                cube([wire_diameter,wire_diameter+0.01,mcu_wire_channels_length],true);
                
                if (mcu_SecondWireChannels) {
                    translate([
                            (pin)*mcu_pin_pitch,iLastRow+wire_diameter-mcu_wire_channels_length/2+2,
                            mcu_base_thickness-wire_diameter/2-wire_diameter*2
                        ]) rotate([90,-180,0])
                    cube([wire_diameter,wire_diameter,mcu_wire_channels_length],true);
                    #translate([
                            -(pin)*mcu_pin_pitch,iLastRow+wire_diameter-mcu_wire_channels_length/2+2,
                            mcu_base_thickness-wire_diameter/2-wire_diameter*2
                        ]) rotate([90,0,0])
                    cube([wire_diameter,wire_diameter,mcu_wire_channels_length],true);
                }

            }
        }
    }

     // Retention Tabs
        if (mcu_RetentionTabs) {
            for (x = [-1,1]) {
        translate([x*mcu_RetentionTabs_x,0,(mcu_base_thickness+mcu_height+1)/2]) {
            for (y = [-1*mcu_RetentionTabs_width/2+mcu_RetentionTabs_y1,mcu_length+mcu_RetentionTabs_width/2+mcu_RetentionTabs_y2]) {
                translate([0,y,0])
                    if (mcu_hold_the_mcu) {
                        cube(
                            [(mcu_RetentionTabs_length),mcu_RetentionTabs_width,mcu_base_thickness+mcu_height+1],
                            center=true
                        );
                    } else {
                        cube(
                        [(mcu_width-mcu_connector_width),2,mcu_base_thickness+mcu_height-2],
                        center=true
                    );
                        }
            }
        }
    
    
    // hold the MCU 
        if (mcu_hold_the_mcu) {
            translate([x*mcu_RetentionTabs_x,0,mcu_base_thickness+mcu_height+0.5]) {
                rotate([0,90,0]) {
                    for (y = [0+mcu_RetentionTabs_y1,mcu_length+mcu_RetentionTabs_y2]) {
                    translate([0,y,0]) 
                        cylinder(h=mcu_RetentionTabs_length,d=0.5,center=true);
                    }
                }
            }
        }
    }
    }
}


module socketed_mcu3(borders=[0,0,0,0]) {
    mcu_base_thickness3=8;
    difference() {
        union() {
            // Base
            translate([-(mcu_socket_width+1)/2,-2-0.5,0]) 
                cubeRC([(mcu_socket_width+1),(mcu_socket_length+0.5),mcu_base_thickness3]);
            // Border
            translate([0,mcu_socket_length/2-4.2,pcb_thickness/2-1])
                border(
                    [mcu_h_unit_size*h_unit,mcu_v_unit_size*v_unit+1], 
                    borders, 
                    pcb_thickness-2
                );
            }
        
        //Center cube cut
        if (mcu_name=="Elite_C" || mcu_name=="RP2040_Zero") {
                //Port
                translate([-(mcu_center_cube_cut_width)/2,(mcu_wire_channels_length/2)-2, pcb_thickness-1]) 
                cube([mcu_center_cube_cut_width,mcu_center_cube_cut_length+0.01,mcu_base_thickness3]);
                //MCU Board
                translate([-(mcu_width+0.4+0.2)/2,-0.2-0.2,pcb_thickness-2]) 
                cube([mcu_width+0.4+0.2,mcu_length+0.4+0.2,mcu_base_thickness3]);
            
            if (mcu_name=="RP2040_Zero") {
                //Center Deep
                translate([-(11)/2,2,pcb_thickness-3]) 
                    cube([11,mcu_length-3,mcu_base_thickness3]);
            }
            } else {
                translate([-(mcu_center_cube_cut_width)/2,-2,mcu_base_thickness3-pcb_thickness]) 
                cube([mcu_center_cube_cut_width,mcu_socket_length,mcu_base_thickness3]);
                };
            
        // Wire Channels L&R
        for (row = [-1,1]) {
            for (pin = [0:mcu_pin_count/2-1]) {
                //inside
//                translate([row*(mcu_width)/2,mcu_pin_offset+(pin+0.5)*mcu_pin_pitch,-0.5]) 
//                    cylinder(h=mcu_base_thickness3+1,d=wire_diameter*1.5);
//                translate([row*(mcu_width-1.5)/2,mcu_pin_offset+(pin+0.5)*mcu_pin_pitch,-0.5]) 
//                    cylinder(h=mcu_base_thickness3+1,d=wire_diameter*1.5);
                translate([row*mcu_row_spacing/2,mcu_pin_offset+(pin+0.5)*mcu_pin_pitch,-0.5]) 
                    cylinder(h=mcu_base_thickness3+1,d=wire_diameter*1.5);                    
                //outside
                translate([row*(mcu_width/2+2.5),mcu_pin_offset+(pin+0.5)*mcu_pin_pitch,-0.5]) 
                    cylinder(h=mcu_base_thickness3+1,d=wire_diameter*1.5);
                //top
                translate([
                    row*((mcu_width+mcu_wire_channels_length)/2-2),
                    mcu_pin_offset+(pin+0.5)*mcu_pin_pitch,
                    mcu_base_thickness3-wire_diameter/2
                ]) rotate([0,row*90,0])
                cube([wire_diameter,wire_diameter,mcu_wire_channels_length],true);
                //mid
                translate([
                    row*((mcu_width+mcu_wire_channels_length)/2-2),
                    mcu_pin_offset+(pin+0.5)*mcu_pin_pitch,
                    pcb_thickness+1
                ]) rotate([0,row*90,0])
                cube([wire_diameter,wire_diameter,mcu_wire_channels_length],true);

                //bottom
                translate([
                    row*((mcu_width+mcu_wire_channels_length)/2-3.5-0.2),
                    mcu_pin_offset+(pin+0.5)*mcu_pin_pitch,
                    wire_diameter/2
                ]) rotate([0,row*90,0])
                cube([wire_diameter,wire_diameter,2.8+1],true);                
            }
        }
        
        // Wire Channels B
        if (mcu_name=="Elite_C" || mcu_name=="RP2040_Zero") {
            iLastRow =(0+0.5)*mcu_pin_pitch;
//            iLastRow =(0+0.5)*mcu_pin_pitch-1.5;

    //        echo ("Last Row:",iLastRow);
    
            for (pin = [0:2]) {
                //inside L
                translate([(pin)*mcu_pin_pitch,iLastRow+0,-wire_diameter/3]) 
                    cylinder(h=mcu_base_thickness3-wire_diameter/2,d=wire_diameter*1.5);
//                translate([(pin)*mcu_pin_pitch,iLastRow+0.75,-wire_diameter/3]) 
//                    cylinder(h=mcu_base_thickness3-wire_diameter/2,d=wire_diameter*1.5);
           
                    
                    
                    
                //inside R
                translate([-(pin)*mcu_pin_pitch,iLastRow+0,-wire_diameter/3]) 
                    cylinder(h=mcu_base_thickness3-wire_diameter/2,d=wire_diameter*1.5);
//                translate([-(pin)*mcu_pin_pitch,iLastRow+0.75,-wire_diameter/3]) 
//                    cylinder(h=mcu_base_thickness3-wire_diameter/2,d=wire_diameter*1.5);

                    //outside L
                translate([(pin)*mcu_pin_pitch,iLastRow-2.5-1.5,-wire_diameter/3]) 
                    cylinder(h=mcu_base_thickness3-wire_diameter/2,d=wire_diameter*1.5);
                //outside R
                translate([-(pin)*mcu_pin_pitch,iLastRow-2.5-1.5,-wire_diameter/3]) 
                    cylinder(h=mcu_base_thickness3-wire_diameter/2,d=wire_diameter*1.5);
                //top L
                translate([
                        (pin)*mcu_pin_pitch,iLastRow+wire_diameter-mcu_wire_channels_length/2+2,
                        mcu_base_thickness3-wire_diameter/2
                    ]) rotate([90,-180,0])
                cube([wire_diameter,wire_diameter,mcu_wire_channels_length],true);
                //top R
                translate([
                        -(pin)*mcu_pin_pitch,iLastRow+wire_diameter-mcu_wire_channels_length/2+2,
                        mcu_base_thickness3-wire_diameter/2
                    ]) rotate([90,0,0])
                cube([wire_diameter,wire_diameter,mcu_wire_channels_length],true);
                
                //mid L
                translate([
                        (pin)*mcu_pin_pitch,iLastRow+wire_diameter-mcu_wire_channels_length/2+2,
                        pcb_thickness+1
                    ]) rotate([90,-180,0])
                cube([wire_diameter,wire_diameter,mcu_wire_channels_length],true);
                //mid R
                translate([
                        -(pin)*mcu_pin_pitch,iLastRow+wire_diameter-mcu_wire_channels_length/2+2,
                        pcb_thickness+1
                    ]) rotate([90,0,0])
                cube([wire_diameter,wire_diameter,mcu_wire_channels_length],true);                
                //botton L
                translate([
                        (pin)*mcu_pin_pitch,iLastRow+wire_diameter-mcu_wire_channels_length/2+2.7-0.5,
                        wire_diameter/2
                    ]) rotate([90,-180,0])
                cube([wire_diameter,wire_diameter,2.8+1],true);
                //botton R
                translate([
                        -(pin)*mcu_pin_pitch,iLastRow+wire_diameter-mcu_wire_channels_length/2+2.7-0.5,
                        wire_diameter/2
                    ]) rotate([90,0,0])
                cube([wire_diameter,wire_diameter,2.8+1],true);

            }
        }
    }

    // Wire Channels L&R
    for (row = [-1,1]) {
        for (pin = [0:mcu_pin_count/2-1]) {
            //inside
            difference()
            {
            translate([row*(mcu_width+0.5)/2,mcu_pin_offset+(pin+0.5)*mcu_pin_pitch,pcb_thickness]) 
                cylinder(h=0.5,d=wire_diameter*1,$fn=50);
                    

            translate([row*((mcu_width-0)/2-0.5),mcu_pin_offset+(pin+0.5)*mcu_pin_pitch-(wire_diameter*2)/2+wire_diameter,pcb_thickness]) 
                cube([wire_diameter*0.8,wire_diameter*2,1],center=true);
            }
        }
    }               
    if (mcu_name=="Elite_C" || mcu_name=="RP2040_Zero") {
        iLastRow =(0+0.5)*mcu_pin_pitch-1.5;
        for (pin = [0:2]) {
            difference()
            {
            union()
            {
            //inside L
            translate([(pin)*mcu_pin_pitch,iLastRow-0.3,pcb_thickness]) 
                cylinder(h=0.5,d=wire_diameter*1,$fn=50);
                    
            //inside R
            translate([-(pin)*mcu_pin_pitch,iLastRow-0.3,pcb_thickness]) 
                cylinder(h=0.5,d=wire_diameter*1,$fn=50);
            }
                
            union()
            {
            //inside L
            translate([(pin)*mcu_pin_pitch-(wire_diameter*2)/2+wire_diameter,iLastRow-0.3+(wire_diameter*0.8)/1.5+0.25,pcb_thickness])
                cube([wire_diameter*2,wire_diameter*0.8,1],center=true);

                    
            //inside R
            translate([(-pin)*mcu_pin_pitch-(wire_diameter*2)/2+wire_diameter,iLastRow-0.3+(wire_diameter*0.8)/1.5+0.25,pcb_thickness])
                cube([wire_diameter*2,wire_diameter*0.8,1],center=true);
            }
            }
        }
   }

}

module bare_mcu(borders=[0,0,0,0]) {    
    difference() {
        union() {
            // Socket base
            translate([-mcu_socket_width/2,-2,0]) 
                cube([mcu_socket_width,mcu_socket_length,pcb_thickness+mcu_pcb_thickness]);
            // Border
            translate([0,mcu_socket_length/2-2,pcb_thickness/2-1])
                border(
                    [mcu_h_unit_size*h_unit,mcu_v_unit_size*v_unit], 
                    borders, 
                    pcb_thickness-2
                );
        }
        
        // Wire cutouts
        for (row = [-1,1]) {
            for (pin = [0:mcu_pin_count/2-1]) {
                translate([
                    row*(mcu_row_spacing/2-1),
                    (pin+0.5)*mcu_pin_pitch,
                    pcb_thickness-wire_diameter/3
                ]) rotate([0,row*90,0])
                    cylinder(h=1000,d=wire_diameter);
            }
        }
        
        if (mcu_name=="Elite_C") {
            iLastRow =(0+0.5)*mcu_pin_pitch;
//            echo ("Last Row:",iLastRow);
            for (pin = [0:2]) {
                translate([
                        (pin)*mcu_pin_pitch,iLastRow+wire_diameter,
                        pcb_thickness-wire_diameter/3
                    ]) rotate([90,-180,0])
                        cylinder(h=1000,d=wire_diameter);
                translate([
                        -(pin)*mcu_pin_pitch,iLastRow+wire_diameter,
                        pcb_thickness-wire_diameter/3
                    ]) rotate([90,-180,0])
                        cylinder(h=1000,d=wire_diameter);
            }
        }
        
        
        
        // MCU cutout
        translate([-mcu_width/2,0,pcb_thickness]) 
            cube([mcu_width, mcu_length,mcu_pcb_thickness+1]);
        // Side cutout
        translate([-(mcu_socket_width+2)/2,0,pcb_thickness]) 
            cube([mcu_socket_width+2,mcu_pin_count/2*mcu_pin_pitch,mcu_pcb_thickness+1]);
        // USB cutout
        translate([-mcu_connector_width/2,-3,pcb_thickness]) 
            cube([mcu_connector_width,mcu_socket_length+2,mcu_pcb_thickness+1]);
        translate([-mcu_connector_width/2,mcu_length-mcu_connector_length,pcb_thickness-2]) 
            cube([mcu_connector_width,mcu_connector_length+3,pcb_thickness+1]);
        
        // Relief to let you pop the MCU out
        if (mcu_name!="Elite_C") {
            translate([0,0,pcb_thickness-1])
                cylinder(h=mcu_pcb_thickness+2,d=mcu_connector_width);
            translate([-mcu_connector_width/2,-3,pcb_thickness-1])
                cube([mcu_connector_width,3,mcu_pcb_thickness+2]);
        }
    }

    // Retention Tabs
    for (x = [-1,1]) {
        translate([x*(mcu_width+mcu_connector_width)/4,0,(pcb_thickness+mcu_pcb_thickness+1)/2]) {
            for (y = [-1,mcu_length+1]) {
                translate([0,y,0])
                    cube(
                        [(mcu_width-mcu_connector_width)/2,2,pcb_thickness+mcu_pcb_thickness+1],
                        center=true
                    );
            }
        }
        translate([x*(mcu_width+mcu_connector_width)/4,0,pcb_thickness+mcu_pcb_thickness+0.5]) {
            rotate([0,90,0]) {
                for (y = [0,mcu_length]) {
                translate([0,y,0]) 
                    cylinder(h=(mcu_width-mcu_connector_width)/2,d=1,center=true);
                }
            }
        }
    }
}

module mcu_plate_footprint(borders=[0,0,0,0]) {
    translate([h_unit/2,-mcu_v_unit_size*v_unit/2,0]) {
        border_footprint(
            [mcu_h_unit_size*h_unit,mcu_v_unit_size*v_unit], 
            borders
        );
    }
}

module mcu_plate_cutout_footprint() {
    if (mcu_type == "bare") {
        translate([h_unit/2,-mcu_v_unit_size*v_unit/2,0]) {
            if (switch_type == "mx") {
                // Only connector will interfere, so limit cutout to that.
                // If mid-mounted this cutout can be eliminated with 
                // mcu_connector_length = 0
                border_footprint(
                    [mcu_width,mcu_length], 
                    [
                        1000,
                        mcu_connector_length-mcu_length,
                        (mcu_connector_width-mcu_width)/2,
                        (mcu_connector_width-mcu_width)/2
                    ]
                );
            } else if (switch_type == "choc") {
                // The whole socket is too thick for choc plate spacing
                border_footprint(
                    [mcu_socket_width,mcu_socket_length], 
                    [1000,0,0,0]
                );
            } else {
                assert(false, "switch_type is invalid");
            }
        }
    } else if (mcu_type == "socketed") {
        // Will interfere with plate, so cutout must fit the whole MCU. 
        // Extend cutout above for connector
        translate([h_unit/2,-mcu_v_unit_size*v_unit/2,0]) {
            border_footprint(
                [mcu_socket_width,mcu_socket_length], 
                [1000,0,0,0]
            );
        }
    } else if (mcu_type == "socketed2") {
        // Will interfere with plate, so cutout must fit the whole MCU. 
        // Extend cutout above for connector
        translate([h_unit/2,-mcu_v_unit_size*v_unit/2,0]) {
            border_footprint(
                [mcu_socket_width,mcu_socket_length], 
                [1000,0,0,0]
            );
        }
    } else {
        assert(false, "mcu_type is invalid");
    }
}

module mcu_plate_base(borders=[0,0,0,0], thickness=plate_thickness) {
    linear_extrude(thickness, center=true)
        mcu_plate_footprint(borders);
}

module mcu_plate_cutout(thickness=plate_thickness) {
    linear_extrude(thickness+1, center=true)
        mcu_plate_cutout_footprint();
}

module mcu_case_cutout() {
    // Connector plug cutout
    translate([
        h_unit/2,
        0,
        plate_thickness/2-pcb_plate_spacing+mcu_pcb_thickness/2+mcu_connector_offset
    ]) rotate([-90,0,0]) {
        hull() {
            for (i=[-1,1]) translate([i*(mcu_connector_width-mcu_connector_height)/2,0,-mcu_connector_length-2])
                cylinder(h=1000, d=mcu_connector_height);
        }
    }

    linear_extrude(plate_thickness+1, center=true)
        mcu_plate_cutout_footprint();

    // Cut out case above MCU
    if (expose_mcu) {
        linear_extrude(10,center=true) {
            difference() {
                translate([h_unit/2,-mcu_v_unit_size*v_unit/2,0]) {
                    rotate([0,0,0]) 
                        grid_pattern(grid_size, grid_spacing, mcu_width, mcu_length);
                }
                offset(delta=grid_spacing) mcu_plate_cutout_footprint();
            }
        }
    }
}

//Andy add:
module mcu_socket_base(borders=[0,0,0,0]) {
    translate([
        h_unit/2,
        -(mcu_v_unit_size*v_unit+mcu_socket_length)/2+2,
        0
    ]) rotate([0,layout_type == "row"?180:0,0]) translate([0,0,-pcb_thickness/2]) {
        socketed_mcu_base(invert_borders(borders,layout_type == "row"));

    }
}


module socketed_mcu_base(borders=[0,0,0,0]) {

        union() {
            // Base
            translate([-mcu_socket_width/2,-2,0]) 
                cube([mcu_socket_width,mcu_socket_length,pcb_thickness]);
            // Border
            translate([0,mcu_socket_length/2-2,pcb_thickness/2-1])
                border(
                    [mcu_h_unit_size*h_unit,mcu_v_unit_size*v_unit], 
                    borders, 
                    pcb_thickness-2+0.01
                );
            }


}
//
//mcu([0,0,0,0]);
