AndyChiu/hotswap_pcb_generator/scad_UTP/pcb.scad

include <parameters.scad>
include <utils.scad>

use <switch.scad>
use <mcu.scad>

//use <ec11.scad>  //Normal
//use <ec11s.scad> //SMD
use <ec11s_diode.scad> //SMD with diode

use <evqwgd001.scad>
use <trrs.scad>
use <stabilizer.scad>
use <microswitch.scad>
use <via.scad>
use <IDC\IDC_Holder.scad>
use <oled.scad>

module pcb(switch_layout, mcu_layout,ec11_layout, evqwgd001_layout, microswitch_layout, trrs_layout, stab_layout, standoff_layout, via_layout, pcb_outer_layout,oled_layout,base_pcb_layout_IDC_Hole) {
    
    difference() {
        
        pcb_base(switch_layout, mcu_layout,ec11_layout, evqwgd001_layout, microswitch_layout, trrs_layout, stab_layout, standoff_layout, via_layout,pcb_outer_layout,oled_layout,base_pcb_layout_IDC_Hole);
        
        if (base_pcb_layout_DesignMode==false || $preview==false) {
            
            layout_pattern(switch_layout,"switch_socket_cutout") {
                switch_socket_cutout($borders, $extra_data[0], $extra_data[1]);
            }
            
            layout_pattern(standoff_layout,"standoff_cutout") {
                pcb_standoff($extra_data);
            }
            
            if (switch_type == "ks27" || switch_type == "ks27_holder") {
                layout_pattern(stab_layout,"stab_socket_cutout") {
                    stabilizer_PCB_cutout_ChocV2($extra_data[1]);
                }
            } else if (switch_type == "Choc" && choc_v2 == true) {
                layout_pattern(stab_layout,"stab_socket_cutout") {
                    stabilizer_pcb_cutout_ChocV2($extra_data[1]);
                }
            } else {
                layout_pattern(stab_layout,"stab_socket_cutout") {
                    stabilizer_pcb_cutout($extra_data[1]);
                }
            }

            
            stab_layout2 = [ for (item = switch_layout) if (len(item[2]) == 6 && item[0][1][0]>item[0][1][1]) item ];

            if (switch_type == "ks27" || switch_type == "ks27_holder") {
                layout_pattern(stab_layout2,"stab_socket_cutout") {
                    stabilizer_PCB_cutout_ChocV2($extra_data[5]);
                }
            } else if (switch_type == "Choc" && choc_v2 == true) {
                layout_pattern(stab_layout2,"stab_socket_cutout") {
                    stabilizer_pcb_cutout_ChocV2($extra_data[5]);
                }
            } else {
                layout_pattern(stab_layout2,"stab_socket_cutout") {
                    stabilizer_pcb_cutout($extra_data[5]);
                }
            }
            
            //Vertical
            stab_layout3 = [ for (item = switch_layout) if (len(item[2]) == 6 && item[0][1][0]<item[0][1][1]) item ];

//            rotate([0,0,-90])
//            translate([0,0,0])
//            {            
                if (switch_type == "ks27" || switch_type == "ks27_holder") {
                    layout_pattern(stab_layout3,"stab_socket_cutout") {
                        stabilizer_PCB_cutout_ChocV2($extra_data[5],true);
                    }
                } else if (switch_type == "Choc" && choc_v2 == true) {
                    layout_pattern(stab_layout3,"stab_socket_cutout") {
                        stabilizer_pcb_cutout_ChocV2($extra_data[5],true);
                    }
                } else {
                    layout_pattern(stab_layout3,"stab_socket_cutout") {
                        stabilizer_pcb_cutout($extra_data[5],true);
                    }
                }
//            }

            layout_pattern(ec11_layout) {
                ec11_socket_cutout($borders);
            }

            layout_pattern(oled_layout,"oled_cutout") {
                oled_socket_cutout($borders,$extra_data);
            }
            
            layout_pattern(standoff_layout,"standoff") {
                pcb_standoff_hole($extra_data);
            }
            layout_pattern(via_layout,"via") {
                via($extra_data);
            }
        }
    }
}

module pcb_base(switch_layout, mcu_layout,ec11_layout, evqwgd001_layout, microswitch_layout, trrs_layout, stab_layout, standoff_layout, via_layout,pcb_outer_layout,oled_layout,base_pcb_layout_IDC_Hole) {
    difference() {
            union() {
                //Andy add:
                difference() {
                    pcb_layout_outer(pcb_outer_layout);
                    //cutout
                    layout_pattern(switch_layout,"switch_socket_base_cutout");
//                  layout_pattern(mcu_layout,"mcu_cutout");
                    layout_pattern(mcu_layout) {
                        mcu_socket_base($borders);
                    }                    
                }
                
                layout_pattern(switch_layout) {
                    
                    if (base_pcb_layout_ApyAdjSwitchAngleAndHeight) {
                    } else { }
                    
                    SSB_Borders = (base_pcb_layout_ApyAdjSwitchAngleAndHeight==true &&
                                   base_pcb_layout_IfAdjSwitchAngleAndHeight_NoBorders==true) 
                                ?  [0,0,0,0] : $borders;
                    
                    if ($extra_data[1]=="chocMini") {

                        switch_socket_base_chocMini(SSB_Borders);
    
                    } else if ($extra_data[1]=="choc" && switch_socket_base_holder==true) {
                        switch_socket_base_choc(SSB_Borders);
                        
                    } else if ($extra_data[1]=="choc_holder") {

                        switch_socket_base_choc(SSB_Borders);  
                        
                    } else if ($extra_data[1]=="mx_s_holder") {
                        
                        switch_socket_base_mx_stabilizer($borders);
    
                    } else if ($extra_data[1]=="mx_s_holder2") {
                        
                        switch_socket_base_mx_stabilizer2($borders);      

                    } else if ($extra_data[1]=="ks27_holder" || $extra_data[1]=="ks33v3_holder") {

                        switch_socket_base_ks27(SSB_Borders);  
                        
                    } else if (
                    ($extra_data[1]=="mx" && switch_socket_base_holder==true) || 
                    ($extra_data[1]=="mx_holder" )) {

                        switch_socket_base_mx(SSB_Borders);
    
                    } else if ($extra_data[1]=="mx_holder") {
                        
                        switch_socket_base_mx(SSB_Borders);
                            
                    } else {
                        switch_socket_base(SSB_Borders);
                    }
                }
    
    //        layout_pattern(mcu_layout) {
    //            mcu($borders);
    //        }
    //        layout_pattern(ec11_layout) {
    //            ec11_socket($borders);
    //        }
            layout_pattern(evqwgd001_layout) {
                evqwgd001_socket($borders);
            }
            layout_pattern(microswitch_layout) {
                microswitch_socket($borders);
            }
            layout_pattern(trrs_layout) {
                trrs($borders);
            }
            
            if (switch_type == "ks27" || switch_type == "ks27_holder") {
                layout_pattern(stab_layout,"stab_socket_base") {
                    stabilizer_pcb_base_ChocV2($borders, $extra_data[1]);
                }
            } else if (switch_type == "Choc" && choc_v2 == true) {
                layout_pattern(stab_layout,"stab_socket_base") {
                    stabilizer_pcb_base_ChocV2($borders, $extra_data[1]);
                }
    //        } else if (switch_type == "mx" && switch_socket_base_holder == true) {
    //            layout_pattern(stab_layout) {
    //                stabilizer_pcb($borders, $extra_data);
    //            }
            } else if (switch_type == "mx_s_holder2") {
                layout_pattern(stab_layout,"stab_socket_base") {
                    stabilizer_pcb_base2($borders, $extra_data[1]);
                }
            } else {
                layout_pattern(stab_layout,"stab_socket_base") {
                    stabilizer_pcb_base($borders
                    , $extra_data[1]);
                }
            }

            
            stab_layout2 = [ for (item = switch_layout) if (len(item[2]) == 6 && item[0][1][0]>item[0][1][1]) item ];

            if (switch_type == "ks27" || switch_type == "ks27_holder") {
                layout_pattern(stab_layout2,"stab_socket_base") {
                    stabilizer_pcb_base_ChocV2($borders, $extra_data[5]);
                }
            } else if (switch_type == "Choc" && choc_v2 == true) {
                layout_pattern(stab_layout2,"stab_socket_base") {
                    stabilizer_pcb_base_ChocV2($borders, $extra_data[5]);
                }
    //        } else if (switch_type == "mx" && switch_socket_base_holder == true) {
    //            layout_pattern(switch_layout) {
    //                stabilizer_pcb($borders, $extra_data);
    //            }
            } else if (switch_type == "mx_s_holder2") {
                layout_pattern(stab_layout2,"stab_socket_base") {
                    stabilizer_pcb_base2($borders, $extra_data[5]);
                }
            } else {
                layout_pattern(stab_layout2,"stab_socket_base") {
                    stabilizer_pcb_base($borders
                    , $extra_data[5]);
                }
            }
            
            //Vertical
            stab_layout3 = [ for (item = switch_layout) if (len(item[2]) == 6 && item[0][1][0]<item[0][1][1]) item ];
            
//            rotate([0,0,-90])
//            translate([stab_layout3[0][0]*unit,stab_layout3[0][1]*unit,0])
//            {            
                if (switch_type == "ks27" || switch_type == "ks27_holder") {
                    layout_pattern(stab_layout3,"stab_socket_base") {
                        stabilizer_pcb_base_ChocV2($borders, $extra_data[5],true);
                    }
                } else if (switch_type == "Choc" && choc_v2 == true) {
                    layout_pattern(stab_layout3,"stab_socket_base") {
                        stabilizer_pcb_base_ChocV2($borders, $extra_data[5],true);
                    }
        //        } else if (switch_type == "mx" && switch_socket_base_holder == true) {
        //            layout_pattern(switch_layout) {
        //                stabilizer_pcb($borders, $extra_data);
        //            }
                } else if (switch_type == "mx_s_holder2") {
                    layout_pattern(stab_layout3,"stab_socket_base") {
                        stabilizer_pcb_base2($borders, $extra_data[5],true);
                    }
                } else {
                    layout_pattern(stab_layout3,"stab_socket_base") {
                        stabilizer_pcb_base($borders
                        , $extra_data[5],true);
                    }
                }
                
//            }

            layout_pattern(ec11_layout) {
                ec11_socket_base($borders);
            }
            
            layout_pattern(standoff_layout) {
                pcb_standoff($extra_data);
            }
            
            layout_pattern(oled_layout,pattern_type="oled") {
                oled_socket_base($borders,$extra_data);
            }
    
    
    }
        
//        layout_pattern(mcu_layout) {
//            mcu_socket_base($borders);
//        }
        
//        layout_pattern(ec11_layout) {
//            ec11_socket_base($borders);
//        }
    
    
        layout_pattern(base_switch_layout,"switch_socket_base_cutout2");    

    }
    
    layout_pattern(mcu_layout) {
        mcu($borders);
    }
//    layout_pattern(ec11_layout) {
//        ec11_socket($borders);
//    }    

    //建立外框
    if (base_pcb_layout_outer_EdgeFrame=="RoundedCorners") {
        difference() {
             pcb_layout_outer(base_pcb_layout_outer, base_pcb_layout_outer_EdgeFrame_hight,-2,base_pcb_layout_outer_EdgeFrame_size_x,base_pcb_layout_outer_EdgeFrame_size_y,"EdgeFrameOuter");
           pcb_layout_outer(base_pcb_layout_outer,base_pcb_layout_outer_EdgeFrame_hight+0.02,-2-0.01,0,0,"EdgeFrameInner");
           //IDC座與接口挖空
           pcb_layout_IDC_Hole(base_pcb_layout_IDC_Hole);
        }
    } else if (base_pcb_layout_outer_EdgeFrame=="Basic") {
        difference() {
             pcb_layout_outer(base_pcb_layout_outer, base_pcb_layout_outer_EdgeFrame_hight,-2,base_pcb_layout_outer_EdgeFrame_size_x,base_pcb_layout_outer_EdgeFrame_size_y,"EdgeFrame");
           pcb_layout_outer(base_pcb_layout_outer,base_pcb_layout_outer_EdgeFrame_hight+0.02,-2-0.01,0,0,"EdgeFrame");   
           //IDC座與接口挖空
           pcb_layout_IDC_Hole(base_pcb_layout_IDC_Hole);
        }
    }
}

module pcb_layout_outer(groups, LE_height=2, trans_z=-2,resize_x=0,resize_y=0,modeType="") {
    //繪製PCB板的外圍
    //以便於直接當鍵盤使用時更為美觀
    //groups: 描繪位置群
    //LE_height: 外框高度
    //trans_z: 高度偏移
    //resize_y
    //resize_x: XY軸大小變更
    
    if (base_pcb_layout_outer_DesignMode==true) {
        //測試模式，只放上點，沒有使用hull
        translate([0,0,2])
        union() for (group = groups) {
                 for (point = group) {
                     translate([point[0][0]*h_unit_ratio,
                                point[0][1]*v_unit_ratio,
                                point[0][2]]) color(point[2]) resize([point[1]*2+resize_x, point[1]*2+resize_y],0) circle(point[1],$fn=50);
                     translate([point[0][0]*h_unit_ratio,
                                point[0][1]*v_unit_ratio,
                                point[0][2]-5]) rotate([180,0,0]) color("Black") %text(point[3],size=3);                
            }
        }
    } else if (base_pcb_layout_outer_DesignMode=="DontShow" && modeType=="") {
        echo ("DontShow");
        
    } else if (modeType=="EdgeFrameOuter") {
        //外框外側
        translate([0,0,trans_z])
        union() for (group = groups) {
            hull_color =
                (base_pcb_layout_outer_hull_color!="None" &&base_pcb_layout_outer_hull_color!="Group")
                ? base_pcb_layout_outer_hull_color
                : base_pcb_layout_outer_hull_color=="Group"
                ? group[0][2]        
                : false ;
            color(hull_color)      
            hull() {
                for (point = group) {
                     translate([point[0][0]*h_unit_ratio,
                                point[0][1]*v_unit_ratio,
                                point[0][2]+LE_height/2]) resize([point[1]*2+resize_x, point[1]*2+resize_y],0) circleRC(point[1],LE_height,1,true,$fn=point[1]*20);
                 }
            }
        }
    } else if (modeType=="EdgeFrameInner") {
        //外框內側
    //circleRC(diameter,height,rc_size=1,center=false,vertical_base=true,vertical_top=false,concave=false)
        translate([0,0,trans_z])
        union() for (group = groups) {
            hull_color =
                (base_pcb_layout_outer_hull_color!="None" &&base_pcb_layout_outer_hull_color!="Group")
                ? base_pcb_layout_outer_hull_color
                : base_pcb_layout_outer_hull_color=="Group"
                ? group[0][2]        
                : false ;
            color(hull_color)      
            hull() {
                for (point = group) {
                     translate([point[0][0]*h_unit_ratio,
                                point[0][1]*v_unit_ratio,
                                point[0][2]+LE_height/2]) resize([point[1]*2+resize_x, point[1]*2+resize_y],0) circleRC(point[1],LE_height,1,true,true,false,true,$fn=point[1]*20);
                 }
            }
        }

    } else {
        //正常模式，產生hull結構
        translate([0,0,trans_z])
        union() for (group = groups) {
            hull_color =
                (base_pcb_layout_outer_hull_color!="None" &&base_pcb_layout_outer_hull_color!="Group")
                ? base_pcb_layout_outer_hull_color
                : base_pcb_layout_outer_hull_color=="Group"
                ? group[0][2]        
                : false ;
            color(hull_color)
            linear_extrude(LE_height) 
            hull() {
                for (point = group) {
                     translate([point[0][0]*h_unit_ratio,
                                point[0][1]*v_unit_ratio,
                                point[0][2]]) resize([point[1]*2+resize_x, point[1]*2+resize_y],0) circle(point[1],$fn=point[1]*20);
                 }
            }
            

        }

        }
}

module pcb_layout_Rubber_Pads(group) {
    //挖PCB板的橡膠墊凹槽
    //以便於直接當鍵盤使用時更為美觀
    //group: 描繪位置群
    for (point = group) {
          translate ([point[0][0]*h_unit_ratio,
                                point[0][1]*v_unit_ratio,
                                point[0][2]])
    color(point[2]) cylinder(h=point[1][1],r=point[1][0]/2,center=true,$fn=point[1][0]*3);
   
        if (base_pcb_layout_Rubber_Pads_DesignMode) {
          translate ([point[0][0]*h_unit_ratio,
                                point[0][1]*v_unit_ratio,
                                point[0][2]])
        rotate([180,0,0]) color("Black") %text(point[3],size=3);
        }
      }
}

module pcb_layout_Cable_Hole(group) {
    //挖PCB板的凸起軸座的互通孔道，可用於將線路由底部穿孔的方式處理
    //group: 描繪位置群
     for (point = group) {

        translate([point[0][0]*h_unit_ratio,
                                    point[0][1]*v_unit_ratio,
                                    point[0][2]])
        rotate(point[1])
//        if (point[2] != "") 
//            {}
        if (point[3][0]=="cylinder") {
            #color(point[2]) cylinder(h=point[3][1][0],r=point[3][1][1],center=true,$fn=30);
        } else if (point[3][0]=="cube") {
            #color(point[2]) cube([point[3][1][0], point[3][1][1], point[3][1][2]],center=true);
        
        }

        
        if (base_pcb_layout_Rubber_Pads_DesignMode && point[4] != "") {
            translate([point[0][0]*h_unit_ratio,
                                        point[0][1]*v_unit_ratio,
                                        -3])
            rotate([0,180,180])
            color("Black") %text(point[4],size=3);
        }

    }
}

module pcb_layout_IDC_Hole(group) {
    //挖PCB板，讓IDC接口有洞可以出入，座的深度可以更深
    //group: 描繪位置
    for (point = group) {
        translate([point[0][0]*h_unit_ratio,
                                point[0][1]*v_unit_ratio,
                                point[0][2]])  rotate(point[1]) color(point[3])cube(point[2]);
    }
}

module pcb_layout_IDC(group) {
    //放置IDC接口
    //group: 描繪位置
    for (point = group) {
        translate([point[0][0]*h_unit_ratio,
                                point[0][1]*v_unit_ratio,
                                point[0][2]]) rotate(point[1]) color(point[2]) IDC_Port();
    }
}

//module pcb_layout_OLED_Hole(group) {
//    //放置OLED螢幕模組
//    //group: 描繪位置
//    for (point = group) {
//        translate([point[0][0]*h_unit_ratio,
//                                point[0][1]*v_unit_ratio,
//                                point[0][2]]) OLED_Socket_Hole();
//    }
//}
//module pcb_layout_OLED(group) {
//    //放置OLED螢幕模組
//    //group: 描繪位置
//    for (point = group) {
//        if (point[2]=="")
//        {
//        translate([point[0][0]*h_unit_ratio,
//                                point[0][1]*v_unit_ratio,
//                                point[0][2]]) OLED_Socket(point[1]);
//                                } else {
//        translate([point[0][0]*h_unit_ratio,
//                                point[0][1]*v_unit_ratio,
//                                point[0][2]]) color(point[2]) OLED_Socket(point[1]);
//                                }
//                                
//    }
//}


module pcb_layout_Raised_Text(group) {
    //板上繪製凸起文字
    //group: 描繪位置
    for (point = group) {
        color(point[4])
        translate([point[0][0]*h_unit_ratio,
                                point[0][1]*v_unit_ratio,
                                point[0][2]]) rotate(point[1]) {
             linear_extrude(point[2])
                text(text = point[3][0], font = point[3][1], size = point[3][2]);
        } 
    }
}

module pcb_layout_Indented_Text(group) {
    //板上繪製內凹文字
    //group: 描繪位置
    for (point = group) {
        color(point[4])
        translate([point[0][0]*h_unit_ratio,
                                point[0][1]*v_unit_ratio,
                                point[0][2]]) rotate(point[1]) {
             linear_extrude(point[2])
                text(text = point[3][0], font = point[3][1], size = point[3][2]);
        } 
    }
}

//TEST
difference(){
    
    pcb(switch_layout_final, mcu_layout_final,ec11_layout_final, evqwgd001_layout_final, microswitch_layout_final, trrs_layout_final, stab_layout_final, standoff_layout_final, via_layout_final,base_pcb_layout_outer, base_OLED_layout, base_pcb_layout_IDC_Hole);

    //圓形矽膠墊挖洞
    pcb_layout_Rubber_Pads(base_pcb_layout_Rubber_Pads);   

//    //IDC座與接口挖空
//    pcb_layout_IDC_Hole(base_pcb_layout_IDC_Hole);   
    
    ////Indented_Text TEST
    pcb_layout_Indented_Text(base_pcb_layout_Indented_Text); 
    
    //內部挖孔
    if (base_pcb_layout_Use_Cable_Hole && base_pcb_layout_ApyAdjSwitchAngleAndHeight){
    pcb_layout_Cable_Hole(base_pcb_layout_Cable_Hole);
    }
}

//IDC Interface
pcb_layout_IDC(base_pcb_layout_IDC);   

////Raised_Text TEST
pcb_layout_Raised_Text(base_pcb_layout_Raised_Text);   


//layout_pattern(base_switch_layout,"switch_socket_base_cutout2MOD"); 
//
//translate([0,-100,12.8])
//#cube([100,100,0.5]);

//EC11 Cover TEST
//use <ec11_cover.scad>
//%translate([102,-67.5,-4])
//rotate([0,0,45])
//ec11_upper_covert();

//translate([111,-70,10])
//cylinder(h=8,d=26,center=true,$fn=27);

//
//color("blue")
//translate([17.5,-25, -pcb_thickness/2+10])
//cube([28,28,1]);
