AndyChiu/hotswap_pcb_generator/scad_UTP/plate.scad

include <parameters.scad>
include <utils.scad>

use <switch.scad>
use <mcu.scad>
use <ec11.scad>
use <evqwgd001.scad>
use <microswitch.scad>
use <trrs.scad>
use <stabilizer.scad>
use <standoff.scad>

function plate_borders(borders, h_unit=1, v_unit=1) = [
    borders[0] + plate_margin/v_unit,
    borders[1] + plate_margin/v_unit,
    borders[2] + plate_margin/h_unit,
    borders[3] + plate_margin/h_unit,
];

module plate_footprint(switch_layout, mcu_layout,ec11_layout, evqwgd001_layout, microswitch_layout, trrs_layout, plate_layout, stab_layout) {
    scale_factor = use_plate_layout_only
        ? plate_precision * 100000
        : 1;

    offset(-plate_inner_fillet,$fn=360)
    offset(delta=plate_inner_fillet)
    offset(plate_outer_fillet,$fn=360)
    scale(scale_factor)
    offset(delta=(plate_margin-plate_outer_fillet)/scale_factor)
    scale(1/scale_factor)
    {
        if (use_plate_layout_only) {
            // Hull each group and then union separately, which allows for concavity
            union() for (group = plate_layout) {
                hull() {
                    layout_pattern(group) {
                        let(component_type = $extra_data[0]) {
                            if (component_type == "switch")
                                switch_plate_footprint($borders);
                            else if (component_type == "mcu")
                                mcu_plate_footprint($borders);
                            else if (component_type == "ec11")
                                ec11_plate_footprint($borders);
                            else if (component_type == "evqwgd001")
                                evqwgd001_plate_footprint($borders);
                            else if (component_type == "microswitch")
                                microswitch_plate_footprint($borders);
                            else if (component_type == "trrs")
                                trrs_plate_footprint($borders);
                            else if (component_type == "stab")
                                stabilizer_plate_footprint($borders, $extra_data[1]);
                        }
                    }
                }
            }
        } else {
            hull() {
                layout_pattern(switch_layout) {
                    switch_plate_footprint($borders);
                }
                layout_pattern([for(g=plate_layout) for(e=g) e]) {
                    let(component_type = $extra_data[0]) {
                        if (component_type == "switch")
                            switch_plate_footprint($borders);
                        else if (component_type == "mcu")
                            mcu_plate_footprint($borders);
                        else if (component_type == "ec11")
                            ec11_plate_footprint($borders);
                        else if (component_type == "evqwgd001")
                            evqwgd001_plate_footprint($borders);
                        else if (component_type == "microswitch")
                            microswitch_plate_footprint($borders);
                        else if (component_type == "trrs")
                            trrs_plate_footprint($borders);
                        else if (component_type == "stab")
                            stabilizer_plate_footprint($borders, $extra_data[1]);
                    }
                }
                layout_pattern(mcu_layout) {
                    mcu_plate_footprint($borders);
                }
                layout_pattern(ec11_layout) {
                    ec11_plate_footprint($borders);
                }
                layout_pattern(evqwgd001_layout) {
                    evqwgd001_plate_footprint($borders);
                }
                layout_pattern(microswitch_layout) {
                    microswitch_plate_footprint($borders);
                }
                layout_pattern(trrs_layout) {
                    trrs_plate_footprint($borders);
                }
                layout_pattern(stab_layout) {
                    stabilizer_plate_footprint($borders, $extra_data);
                }
            }
        }
    }
}

module plate_base(switch_layout, mcu_layout,ec11_layout, evqwgd001_layout, microswitch_layout, trrs_layout, plate_layout, stab_layout, thickness=plate_thickness, offset=0) {
    linear_extrude(thickness, center=true, convexity=10)
        offset(offset) plate_footprint(switch_layout, mcu_layout, ec11_layout,  evqwgd001_layout, microswitch_layout, trrs_layout, plate_layout, stab_layout);
}

module plate(switch_layout, mcu_layout, ec11_layout, evqwgd001_layout, microswitch_layout, trrs_layout, plate_layout, stab_layout, standoff_layout) {
    difference() {
        union() {
            plate_base(switch_layout, mcu_layout, ec11_layout, evqwgd001_layout, microswitch_layout, trrs_layout, plate_layout, stab_layout, plate_thickness);
            layout_pattern(standoff_layout) {
                plate_standoff($extra_data);
            }
        }
        layout_pattern(switch_layout) {
            switch_plate_cutout();
        }
        layout_pattern(mcu_layout) {
            mcu_plate_cutout();
        }
        layout_pattern(ec11_layout) {
            ec11_plate_cutout();
        }     
        layout_pattern(evqwgd001_layout) {
            evqwgd001_plate_cutout();
        }
        layout_pattern(microswitch_layout) {
            microswitch_plate_cutout();
        }
        layout_pattern(trrs_layout) {
            trrs_plate_cutout();
        }
        layout_pattern(stab_layout) {
            stabilizer_plate_cutout($extra_data);
        }
        layout_pattern(standoff_layout) {
            plate_standoff_hole($extra_data);
        }
    }
}

plate(switch_layout_final, mcu_layout_final,ec11_layout_final ,evqwgd001_layout_final, microswitch_layout_final, trrs_layout_final, plate_layout_final, stab_layout_final, standoff_layout_final);
