AndyChiu/hotswap_pcb_generator/scad_UTP/stabilizer.scad

include <parameters.scad>
include <utils.scad>
include <stabilizer_spacing.scad>

use <switch.scad>


module stabilizer_layout(spacing=stab_2u,vertical=false) {
    switch_offset = len(spacing) == 4
        ? spacing[3]
        : 0;
    center_x = spacing[0]*unit_stb/2 + switch_offset;
    center_pos = vertical==false
        ? [unit_stb/2-center_x,0,0]
        : [-unit_stb-center_x/2,0,0];
        
    translate(center_pos) {
        translate([center_x-spacing[1],0,0]) children();
        translate([center_x+spacing[2],0,0]) mirror([1,0,0]) children();
    }
}


module stabilizer_pcb(borders=[1,2,0,0],spacing=stab_2u,vertical=false) {
    margin = (spacing[0]-1)/2;
    difference() {
        union() {
            stabilizer_pcb_base(borders, spacing);
//            switch_socket_base([1,1,1+margin*unit_stb*mm,1+margin*unit_stb*mm]);
            switch_socket_base_mx_stabilizer([1,1,1+margin*unit_stb*mm,1+margin*unit_stb*mm]);
        }
        stabilizer_pcb_cutout(spacing);
        switch_socket_cutout([1,1,1+margin*unit_stb*mm,1+margin*unit_stb*mm]);
    }
}


module stabilizer_pcb2(borders=[1,2,2,2],spacing=stab_2u,vertical=false) {
    margin = (spacing[0]-1)/2;
    
    difference() {
        union() {
            stabilizer_pcb_base2(borders, spacing);
//            switch_socket_base([1,1,1+margin*unit_stb*mm,1+margin*unit_stb*mm]);
            translate([0,-unit_stb,0]) rotate([0,0,90]) 
            switch_socket_base_mx_stabilizer2([1+margin*unit_stb*mm,1+margin*unit_stb*mm,1,1]);
        }
        stabilizer_pcb_cutout(spacing);        
        translate([0,1*-unit_stb,0]) rotate([0,0,90])  {
        switch_socket_cutout([1,1,1+margin*unit_stb*mm,1+margin*unit_stb*mm]);   
        }


    }
}

module stabilizer_pcb_ChocV2(borders=[1,2,0,0],spacing=stab_2u,vertical=false ) {
    margin = (spacing[0]-1)/2;

    difference() {
        union() {
            stabilizer_pcb_base_ChocV2(borders, spacing,vertical);
            switch_socket_base([1,1,1+margin*unit_stb*mm,1+margin*unit_stb*mm]);
        }
        switch_socket_cutout([1,1,1+margin*unit_stb*mm,1+margin*unit_stb*mm]);
        stabilizer_PCB_cutout_ChocV2(spacing,vertical);
    }
}

module stabilizer_plate(spacing=stab_2u, thickness=plate_thickness) {
    linear_extrude(thickness, center=true)
    difference() {
        stabilizer_plate_footprint([1,1,1,1], spacing);
        stabilizer_plate_cutout_footprint(spacing);
        switch_plate_cutout_footprint();
    }
}


module stabilizer_pcb_base(borders=[1,2,0,0], spacing=stab_2u,vertical=false) {
    module single_base() {
        translate([0,-v_unit_stb/2,0])
            border(
                [7.5+3, 1*unit_stb],
                [borders2[0]-1,max(borders2[1]-1,1),0,0],
                pcb_thickness,
                h_border_width,
                v_border_width
            );
    }
    stab_rotate = vertical==false
        ? [0,0,0]
        : [0,0,90];
    borders2 = vertical==false
        ? borders
        : [borders[2],borders[3],borders[0],borders[1]];
        
    rotate(stab_rotate)
    stabilizer_layout(spacing,vertical)    
        single_base();
}

module stabilizer_pcb_base2(borders=[1,2,0,0], spacing=stab_2u,vertical=false) {
    module single_base() {
        translate([0,-5,0])
            border(
                [7.5,11],
                [borders2[0]-1,max(borders2[1]-1,1),0,0],
                pcb_thickness,
                h_border_width,
                v_border_width
            );

        translate([0,-v_unit_stb+1.5,0])
            border(
                [7.5,5],
                [borders2[0]-1,max(borders2[1]-1,1),0,0],
                pcb_thickness,
                h_border_width,
                v_border_width
            );

    }
        stab_rotate = vertical==false
            ? [0,0,0]
            : [0,0,90];
        borders2 = vertical==false
            ? borders
            : [borders[2],borders[3],borders[0],borders[1]];
            
        rotate(stab_rotate)
        stabilizer_layout(spacing,vertical)
        single_base();
}

module stabilizer_pcb_base_ChocV2(borders=[1,2,0,0], spacing=stab_2u,vertical=false) {
    module single_base() {
        translate([0,-v_unit_stb/2,0])
            border(
                [10,1*unit_stb],
                [borders2[0]-1,max(borders2[1]-1,1),0,0],
                pcb_thickness,
                h_border_width,
                v_border_width
            );
//        translate([4.5,-v_unit_stb-2.05,0])
//            #cube([15,4.2,pcb_thickness/2]);
    }
        stab_rotate = vertical==false
            ? [0,0,0]
            : [0,0,90];
        borders2 = vertical==false
            ? borders
            : [borders[2],borders[3],borders[0],borders[1]];
            
        rotate(stab_rotate)
        stabilizer_layout(spacing,vertical)
        single_base();
}

module stabilizer_pcb_cutout(spacing=stab_2u) {
    module pcb_mount_cutout() {
        translate([0,-v_unit_stb/2,-pcb_thickness/2]) {
            translate([0,6.985,0]) {
                cylinder(d=3.5, h=pcb_thickness+1);
                translate([0,0,-2.5]) cylinder(d=5*1.1, h=pcb_thickness,$fn=20);
            }
            translate([0,-8.255,0]) {
                bottom_cutout_diameter = 4.5;
                translate([0,0,-0.5]) hull() {
                    cylinder(d=bottom_cutout_diameter, h=pcb_thickness+1);
                    translate([-bottom_cutout_diameter/2,-bottom_cutout_diameter/2,0]) cube([bottom_cutout_diameter,bottom_cutout_diameter/2,pcb_thickness+1]);
                }
                translate([0,0,-1.2]) hull() {
                    cylinder(d=bottom_cutout_diameter, h=pcb_thickness);
                    translate([0,-1,0]) cylinder(d=bottom_cutout_diameter, h=pcb_thickness);
                }
            }
        }
    }
    module plate_mount_cutout() {
    }
    stab_rotate = vertical==false
        ? [0,0,0]
        : [0,0,90];
        
    rotate(stab_rotate)
    stabilizer_layout(spacing,vertical) {    
        if (stabilizer_type == "pcb") {
            pcb_mount_cutout();
        } else if (stabilizer_type == "plate") {
            plate_mount_cutout();
        } else {
            assert(false, "stabilizer_type is invalid");
        }
    }
}


module stabilizer_plate_footprint(borders=[1,1,1,1], spacing=stab_2u) {
    translate([unit_stb/2,-v_unit_stb/2,0])
    border_footprint(
        [spacing[0]*h_unit_stb,v_unit_stb],
        [for (b=borders) b-1]
    );
}

module stabilizer_plate_cutout_footprint(spacing=stab_2u) {
    module pcb_mount_cutout() {
        // Same profile works for both
        plate_mount_cutout();
    }
    module plate_mount_cutout() {
        total_width = spacing[1] + spacing[2];
        wire_cutout_width = spacing == stab_2u
            ? unit_stb/2
            : unit_stb/4;
        translate([0,-v_unit_stb/2,0]) {
            translate([-3.6,-6.604,0]) square([7.2, 12.2936]);
            translate([-1.524,-7.7724,0]) square([3.048, 2]);
            translate([-4.191,-0.508,0]) square([4.191, 2.794]);
            translate([0,-wire_cutout_width/2,0]) square([total_width, wire_cutout_width]);
        }
    }
    stab_rotate = vertical==false
        ? [0,0,0]
        : [0,0,90];
        
    rotate(stab_rotate)
    stabilizer_layout(spacing,vertical) {    
        if (stabilizer_type == "pcb") {
            pcb_mount_cutout();
        } else if (stabilizer_type == "plate") {
            plate_mount_cutout();
        } else {
            assert(false, "stabilizer_type is invalid");
        }
    }
}

module stabilizer_PCB_cutout_ChocV2(spacing=stab_2u,vertical=false) {
    module pcb_mount_cutout() {
        // Same profile works for both
        plate_mount_cutout();
    }
    module plate_mount_cutout() {
        total_width = spacing[1] + spacing[2];
        wire_cutout_width = spacing == stab_2u
            ? unit_stb/2
            : unit_stb/4;
        translate([0,-v_unit_stb/2,0]) {
            translate([-3.6,-6.604,-5]) cube([7.2, 12.2936,10]);
            translate([-1.524,-7.7724,-5]) cube([3.048, 2,10]);
            translate([-1.3,5.6,-4.5]) cube([2.5,1,5]);
            translate([-4.191,0,-5]) cube([4.191*2, 2.794,10]);
            translate([-4.191,-10.05,-5]) cube([4.191*2+v_unit_stb, 3.794,5]);
            translate([3,-10.05,-6]) cube([v_unit_stb, 5.794,5]);
        }
    }
    stab_rotate = vertical==false
        ? [0,0,0]
        : [0,0,90];
        
    rotate(stab_rotate)
    stabilizer_layout(spacing,vertical) {
        if (stabilizer_type == "pcb") {
            pcb_mount_cutout();
        } else if (stabilizer_type == "plate") {
            plate_mount_cutout();
        } else {
            assert(false, "stabilizer_type is invalid");
        }
    }
}

module stabilizer_plate_base(borders=[1,1,1,1], spacing=stab_2u, thickness=plate_thickness) {
    linear_extrude(thickness, center=true)
        stabilizer_plate_footprint(borders, spacing);
}

module stabilizer_plate_cutout(spacing=stab_2u, thickness=plate_thickness) {
    linear_extrude(thickness+1, center=true)
        stabilizer_plate_cutout_footprint(spacing);
}

//stabilizer_pcb([1,2,0,0],stab_2u);
//stabilizer_pcb2([1,2,0,0],stab_2u);
//stabilizer_plate([1,2,0,0],stab_2u);

//stabilizer_pcb_ChocV2([1,2,0,0],stab_2u);
stabilizer_pcb_ChocV2([1,2,0,0],stab_2u,true);
