AndyChiu/hotswap_pcb_generator/scad_UTP/switch.scad

include <parameters.scad>
include <utils.scad>

module switch_socket(borders=[1,1,1,1], rotate_column=false,use_switch_type=switch_type) {
   
    //    difference() { 
    union() {
    translate([0,0,0])    
//    rotate(a=-5, v=[0,0,0])
    difference() {
        
        if (use_switch_type=="chocMini") {
            switch_socket_base_chocMini(borders);
            
        } else if (use_switch_type=="choc" && switch_socket_base_holder==true) {
            switch_socket_base_choc(borders);
            
        } else if (use_switch_type=="choc_holder") {
            switch_socket_base_choc(borders);
            
        } else if (use_switch_type=="chocV2_1u") {
            switch_socket_base_1U_PCB(borders);
            
        } else if (use_switch_type=="mx_s_holder") {
            switch_socket_base_mx_stabilizer(borders);  
            
        } else if (use_switch_type=="mx_s_holder2") {
            switch_socket_base_mx_stabilizer2(borders);  
            
        } else if (use_switch_type=="mx_holder") {
            switch_socket_base_mx(borders);  
            
        } else if (use_switch_type=="ks27" && switch_socket_base_holder==true) {
            switch_socket_base_ks27(borders);  

        } else if (use_switch_type=="ks33v3" && switch_socket_base_holder==true) {
            switch_socket_base_ks27(borders);  

        } else if (use_switch_type=="ks27_holder") {
            switch_socket_base_ks27(borders);  

        } else if (use_switch_type=="ks33v3_holder") {
            switch_socket_base_ks27(borders);  

        } else if (use_switch_type=="redragon_low" && switch_socket_base_holder==true) {
            switch_socket_base_redragon_low(borders);  

        } else if (use_switch_type=="redragon_low_holder") {
            switch_socket_base_redragon_low(borders);  

        } else if (use_switch_type=="alps" && switch_socket_base_holder==true) {
            switch_socket_base_alps(borders);  

        } else if (use_switch_type=="alps_holder") {
            switch_socket_base_alps(borders);  

        } else if (use_switch_type=="fraly" && switch_socket_base_holder==true) {
            switch_socket_base_fraly(borders);
            
        } else if (use_switch_type=="fraly_holder") {
            switch_socket_base_fraly(borders);
            

        } else if (use_switch_type=="mx" && switch_socket_base_holder==true) {
            switch_socket_base_mx(borders);
   
        } else {
            switch_socket_base(borders);
            
        }
        switch_socket_cutout(borders, rotate_column,use_switch_type);
    }
    
//    difference() {
//        switch_socket_base_1U(borders);
//        switch_socket_cutout(borders, rotate_column);
//    }
}
}

module switch_socket_base(borders=[1,1,1,1]) {
    translate([h_unit/2,-v_unit/2,0]) 
    //    difference() {
   union() {
        cube([socket_size, socket_size, pcb_thickness], center=true);
        translate([0,0,border_z_offset ])
            border(
                [socket_size,socket_size], 
                borders, 
                pcb_thickness-2, 
                h_border_width, 
                v_border_width
            );
    }
}


module switch_socket_base_1U_PCB(borders=[1,1,1,1]) {
    translate([h_unit/2,-v_unit/2,0]) 
        difference() {
   //union() {
        cube([13.3, 14, pcb_thickness], center=true);
        translate([0,0,border_z_offset ])
            border(
                [socket_size,socket_size], 
                borders, 
                pcb_thickness-2, 
                h_border_width, 
                v_border_width
            );
    }
}

module switch_socket_base_chocMini(borders=[1,1,1,1]) {
    translate([h_unit/2,-v_unit/2,0]) 
    //    difference() {
   union() {
        cube([socket_size, socket_size, pcb_thickness-2], center=true);
        translate([0,0,border_z_offset ])
            border(
                [socket_size,socket_size], 
                borders, 
                pcb_thickness-2, 
                h_border_width, 
                v_border_width
            );
    }
}

module switch_socket_base_1U(borders=[1,1,1,1]) {
    translate([h_unit/2,-v_unit/2,0]) 
        translate([0,0,border_z_offset ])
            border(
                [socket_size,socket_size], 
                borders, 
                pcb_thickness-2, 
                h_border_width, 
                v_border_width
            );
}


//Choc軸加勾釦的底座
module switch_socket_base_choc(borders=[1,1,1,1]) {
    //choc_holder_wall_h_thickness=(h_unit/2)-(14.5/2);
    //choc_holder_wall_h_thickness_add=1.5-(choc_socket_size-13.8);
    choc_holder_wall_h_thickness_add=0;
    
    choc_holder_wall_h_thickness=choc_socket_size-13.8+choc_holder_wall_h_thickness_add;
    choc_holder_wall_h_width_r=3.8;
    choc_holder_wall_h_width_l=4.5;
    choc_holder_wall_height=2.2;  //2.2


//    //上牆 
//    translate([choc_socket_size+(h_unit-choc_socket_size)/2-choc_holder_wall_h_width_r/2,-(v_unit-choc_socket_size)/2-choc_holder_wall_h_thickness/2+choc_holder_wall_h_thickness_add,(choc_holder_wall_height/2)]) 
//        cube([choc_holder_wall_h_width_r, choc_holder_wall_h_thickness, pcb_thickness+choc_holder_wall_height], center=true);
//
//    translate([(h_unit-choc_socket_size)/2+choc_holder_wall_h_width_l/2,-(v_unit-choc_socket_size)/2-choc_holder_wall_h_thickness/2+choc_holder_wall_h_thickness_add,(choc_holder_wall_height/2)]) 
//        cube([choc_holder_wall_h_width_l, choc_holder_wall_h_thickness, pcb_thickness+choc_holder_wall_height], center=true);

    //choc_holder_wall_v_thickness_add=1.5-(choc_socket_size-14.5);
    choc_holder_wall_v_thickness_add=.5; //厚度增加避免樹酯斷裂
    //choc_holder_wall_v_thickness_add=0;
    choc_holder_wall_v_thickness=choc_socket_size-14.5+choc_holder_wall_v_thickness_add;
    choc_holder_wall_v_width_r=5+7.85;
    choc_holder_wall_v_width_l=5+7.85;
    choc_holder_wall_v_offset=0.2;
    choc_holder_wall_support_width=1;
    
    //勾住位置
    choc_holder_hook_thickness=0.35; //0.35
    choc_holder_hook_height=1;     //1.3
    choc_holder_hook_length=2.5;     //2.5
    choc_holder_hook_margin1=3.5;     //3.5
    choc_holder_hook_margin2=choc_holder_hook_margin1+7;     //10.5

    
    
    
    //右牆
    translate([choc_socket_size+(h_unit-choc_socket_size)/2-choc_holder_wall_v_thickness/2+choc_holder_wall_v_thickness_add+choc_holder_wall_v_offset,-(v_unit-choc_socket_size)/2-choc_holder_wall_v_width_r/2,(choc_holder_wall_height/2)]) {
         cube([choc_holder_wall_v_thickness,choc_holder_wall_v_width_r,  pcb_thickness+choc_holder_wall_height], center=true);
    }
//    
//    translate([choc_socket_size+(h_unit-choc_socket_size)/2-choc_holder_wall_v_thickness/2+choc_holder_wall_v_thickness_add+choc_holder_wall_v_offset+choc_holder_wall_v_thickness_add+choc_holder_wall_support_width/2, -(v_unit-choc_socket_size)/2-choc_holder_wall_v_width_r/2, (choc_holder_wall_height+2)/2]) 
//    {
//        rotate([0,0,90])
//        chamfer(choc_holder_wall_v_width_r, choc_holder_wall_support_width, choc_holder_wall_height+2);
//    
//    }
//    
   //-(v_unit-choc_socket_size)/2-choc_holder_wall_v_width_r/2

    if (switch_socket_base_holder_support_frame) {

    translate([choc_socket_size+(h_unit-choc_socket_size)/2-choc_holder_wall_v_thickness/2+choc_holder_wall_v_thickness_add+choc_holder_wall_v_offset+choc_holder_wall_v_thickness_add+choc_holder_wall_support_width/2, -(choc_socket_size+choc_holder_wall_v_thickness)/2, (choc_holder_wall_height+2)/2]) 
    {
        rotate([0,0,0])
        right_triangle(choc_holder_wall_support_width,choc_holder_wall_v_thickness,(choc_holder_wall_height+2),0,0,0);
    }
}
//        }
    //右短牆
//     translate([choc_socket_size+(h_unit-choc_socket_size)/2-choc_holder_wall_v_thickness/2+choc_holder_wall_v_thickness_add+choc_holder_wall_v_offset,-(v_unit)/2+2.5+(choc_holder_hook_length/2),(choc_holder_wall_height/2)]) 
//        cube([choc_holder_wall_v_thickness,choc_holder_hook_length, pcb_thickness+choc_holder_wall_height ], center=true);
//
//     translate([choc_socket_size+(h_unit-choc_socket_size)/2-choc_holder_wall_v_thickness/2+choc_holder_wall_v_thickness_add+choc_holder_wall_v_offset,-(v_unit)/2-2.5-(choc_holder_hook_length/2),(choc_holder_wall_height/2)]) 
//        cube([choc_holder_wall_v_thickness,choc_holder_hook_length, pcb_thickness+choc_holder_wall_height ], center=true);

    //右短牆連橫牆
//    translate([choc_socket_size+(h_unit-choc_socket_size)/2-choc_holder_wall_v_thickness/2+choc_holder_wall_v_thickness_add+choc_holder_wall_v_offset,-(v_unit)/2,(choc_holder_wall_height/2)-choc_holder_hook_height/2]) 
//        cube([choc_holder_wall_v_thickness,5, pcb_thickness+choc_holder_wall_height -choc_holder_hook_height], center=true);


        
    translate([choc_socket_size+(h_unit-choc_socket_size)/2-(choc_holder_wall_v_thickness+choc_holder_hook_thickness)/2+choc_holder_wall_v_thickness_add,-(v_unit)/2+2.5+(choc_holder_hook_length/2),(pcb_thickness+choc_holder_hook_height)/2+choc_holder_wall_height-choc_holder_hook_height]) 

        cube([choc_holder_wall_v_thickness+choc_holder_hook_thickness,choc_holder_hook_length, choc_holder_hook_height ], center=true);
 
    translate([choc_socket_size+(h_unit-choc_socket_size)/2-(choc_holder_wall_v_thickness+choc_holder_hook_thickness)/2+choc_holder_wall_v_thickness_add,-(v_unit)/2-2.5-(choc_holder_hook_length/2),(pcb_thickness+choc_holder_hook_height)/2+choc_holder_wall_height-choc_holder_hook_height]) 
    
        cube([choc_holder_wall_v_thickness+choc_holder_hook_thickness,choc_holder_hook_length, choc_holder_hook_height ], center=true);
    
    //左牆
    translate([(h_unit-choc_socket_size)/2+choc_holder_wall_v_thickness/2-choc_holder_wall_v_thickness_add-choc_holder_wall_v_offset, -(v_unit-choc_socket_size)/2-choc_holder_wall_v_width_l/2, (choc_holder_wall_height/2)]) {
        cube([choc_holder_wall_v_thickness,choc_holder_wall_v_width_l,  pcb_thickness+choc_holder_wall_height], center=true);
    }
    
//    translate([(h_unit-choc_socket_size)/2+choc_holder_wall_v_thickness/2-choc_holder_wall_v_thickness_add-choc_holder_wall_v_offset-choc_holder_wall_v_thickness_add-choc_holder_wall_support_width/2,  -(v_unit-choc_socket_size)/2-choc_holder_wall_v_width_l/2,  (choc_holder_wall_height+2)/2]) {
//        rotate([0,0,90+180])
//        chamfer(choc_holder_wall_v_width_l, choc_holder_wall_support_width, choc_holder_wall_height+2);
//    }

    if (switch_socket_base_holder_support_frame) {

        translate([(h_unit-choc_socket_size)/2+choc_holder_wall_v_thickness/2-choc_holder_wall_v_thickness_add-choc_holder_wall_v_offset-choc_holder_wall_v_thickness_add-choc_holder_wall_support_width/2+choc_holder_wall_support_width,  -(choc_socket_size+choc_holder_wall_v_thickness)/2,  (choc_holder_wall_height+2)/2]) {
            right_triangle(choc_holder_wall_support_width,choc_holder_wall_v_thickness,(choc_holder_wall_height+2),0,0,180);
        }
    }
//     translate([(h_unit-choc_socket_size)/2+(choc_holder_wall_v_thickness+choc_holder_hook_thickness)/2-choc_holder_wall_v_thickness_add,-(v_unit-choc_socket_size)/2-choc_holder_wall_v_width_l/2-(choc_holder_hook_margin1/2),(pcb_thickness+choc_holder_hook_height)/2+choc_holder_wall_height-choc_holder_hook_height]) 

    //左短牆

//    translate([(h_unit-choc_socket_size)/2+(choc_holder_wall_v_thickness)/2-choc_holder_wall_v_thickness_add-choc_holder_wall_v_offset,-(v_unit)/2+2.5+(choc_holder_hook_length/2),(choc_holder_wall_height/2)]) 
//     #cube([choc_holder_wall_v_thickness,choc_holder_hook_length,  pcb_thickness+choc_holder_wall_height ], center=true);
//
//    translate([(h_unit-choc_socket_size)/2+choc_holder_wall_v_thickness/2-choc_holder_wall_v_thickness_add-choc_holder_wall_v_offset,-(v_unit)/2-2.5-(choc_holder_hook_length/2),(choc_holder_wall_height/2)]) 
//     #cube([choc_holder_wall_v_thickness,choc_holder_hook_length,  pcb_thickness+choc_holder_wall_height ], center=true);
//

    //左短牆連橫牆
//    translate([(h_unit-choc_socket_size)/2+(choc_holder_wall_v_thickness)/2-choc_holder_wall_v_thickness_add-choc_holder_wall_v_offset,-(v_unit)/2,(choc_holder_wall_height/2)-choc_holder_hook_height/2]) 
//        cube([choc_holder_wall_v_thickness,5, pcb_thickness+choc_holder_wall_height -choc_holder_hook_height], center=true);
        
        
    translate([(h_unit-choc_socket_size)/2+(choc_holder_wall_v_thickness+choc_holder_hook_thickness)/2-choc_holder_wall_v_thickness_add,-(v_unit)/2+2.5+(choc_holder_hook_length/2),(pcb_thickness+choc_holder_hook_height)/2+choc_holder_wall_height-choc_holder_hook_height]) 
     
        cube([choc_holder_wall_v_thickness+choc_holder_hook_thickness,choc_holder_hook_length, choc_holder_hook_height ], center=true);

    translate([(h_unit-choc_socket_size)/2+(choc_holder_wall_v_thickness+choc_holder_hook_thickness)/2-choc_holder_wall_v_thickness_add,-(v_unit)/2-2.5-(choc_holder_hook_length/2),(pcb_thickness+choc_holder_hook_height)/2+choc_holder_wall_height-choc_holder_hook_height]) 
     
        cube([choc_holder_wall_v_thickness+choc_holder_hook_thickness,choc_holder_hook_length, choc_holder_hook_height ], center=true);

    if (choc_v1_compatible_v2==true){
        translate([(h_unit-choc_socket_size)/2+(choc_holder_wall_v_thickness+choc_holder_hook_thickness)/2-choc_holder_wall_v_thickness_add,-(v_unit)/2,(pcb_thickness+choc_holder_hook_height)/2+choc_holder_wall_height-choc_holder_hook_height]) 
         
            cube([choc_holder_wall_v_thickness+choc_holder_hook_thickness,choc_holder_hook_length+3, choc_holder_hook_height ], center=true);
        
        translate([choc_socket_size+(h_unit-choc_socket_size)/2-(choc_holder_wall_v_thickness+choc_holder_hook_thickness)/2+choc_holder_wall_v_thickness_add,-(v_unit)/2,(pcb_thickness+choc_holder_hook_height)/2+choc_holder_wall_height-choc_holder_hook_height]) 
        
            cube([choc_holder_wall_v_thickness+choc_holder_hook_thickness,choc_holder_hook_length+3, choc_holder_hook_height ], center=true);
    
    }
/////

    translate([h_unit/2,-v_unit/2,0]) 
    //    difference() {
    union() {
        cube([choc_socket_size, choc_socket_size, pcb_thickness], center=true);
        translate([0,0,border_z_offset ])
            border(
                [choc_socket_size,choc_socket_size], 
                borders, 
                pcb_thickness-2, 
                h_border_width, 
                v_border_width
            );
    }
}


//KS27軸加勾釦的底座
module switch_socket_base_ks27(borders=[1,1,1,1]) {
    //ks27_holder_wall_h_thickness=(h_unit/2)-(14.5/2);
    //ks27_holder_wall_h_thickness_add=1.5-(ks27_socket_size-13.8);
    //ks27_holder_wall_h_thickness_add=0;
    
    //ks27_holder_wall_h_thickness=ks27_socket_size-14+ks27_holder_wall_h_thickness_add;//13.8
    ks27_holder_wall_h_width_r=3.8;
    ks27_holder_wall_h_width_l=4.5;
    ks27_holder_wall_height=2.2;  //2.2


//    //上牆 
//    translate([ks27_socket_size+(h_unit-ks27_socket_size)/2-ks27_holder_wall_h_width_r/2,-(v_unit-ks27_socket_size)/2-ks27_holder_wall_h_thickness/2+ks27_holder_wall_h_thickness_add,(ks27_holder_wall_height/2)]) 
//        cube([ks27_holder_wall_h_width_r, ks27_holder_wall_h_thickness, pcb_thickness+ks27_holder_wall_height], center=true);
//
//    translate([(h_unit-ks27_socket_size)/2+ks27_holder_wall_h_width_l/2,-(v_unit-ks27_socket_size)/2-ks27_holder_wall_h_thickness/2+ks27_holder_wall_h_thickness_add,(ks27_holder_wall_height/2)]) 
//        cube([ks27_holder_wall_h_width_l, ks27_holder_wall_h_thickness, pcb_thickness+ks27_holder_wall_height], center=true);

    //ks27_holder_wall_v_thickness_add=1.5-(ks27_socket_size-14.5);
    ks27_holder_wall_v_thickness_add=2;
    //ks27_holder_wall_v_thickness_add=0;
    ks27_holder_wall_v_thickness=ks27_socket_size-14.8+ks27_holder_wall_v_thickness_add;
    ks27_holder_wall_v_width_r=4.8+7.85-0.56;
    ks27_holder_wall_v_width_l=4.8+7.85-0.56;
    ks27_holder_wall_v_offset=0.2;
    ks27_holder_wall_support_width=1;
    
    //勾住位置
    ks27_holder_hook_thickness=0.35; //0.35
    ks27_holder_hook_height=1;     //1.3
    ks27_holder_hook_length=2;     //2.5
    ks27_holder_hook_margin1=3.5;     //3.5
    ks27_holder_hook_margin2=ks27_holder_hook_margin1+7;     //10.5
//-4.65+3
//-0.675
    //右牆
    translate([ks27_socket_size+(h_unit-ks27_socket_size)/2-ks27_holder_wall_v_thickness/2+ks27_holder_wall_v_thickness_add+ks27_holder_wall_v_offset,-(v_unit-ks27_socket_size)/2-ks27_holder_wall_v_width_r/2,(ks27_holder_wall_height/2)]) {
         cubeRC([ks27_holder_wall_v_thickness,ks27_holder_wall_v_width_r,  pcb_thickness+ks27_holder_wall_height], center=true);
    }
//    
//    translate([ks27_socket_size+(h_unit-ks27_socket_size)/2-ks27_holder_wall_v_thickness/2+ks27_holder_wall_v_thickness_add+ks27_holder_wall_v_offset+ks27_holder_wall_v_thickness_add+ks27_holder_wall_support_width/2, -(v_unit-ks27_socket_size)/2-ks27_holder_wall_v_width_r/2, (ks27_holder_wall_height+2)/2]) 
//    {
//        rotate([0,0,90])
//        chamfer(ks27_holder_wall_v_width_r, ks27_holder_wall_support_width, ks27_holder_wall_height+2);
//    
//    }
//    
   //-(v_unit-ks27_socket_size)/2-ks27_holder_wall_v_width_r/2

    if (switch_socket_base_holder_support_frame) {

    translate([ks27_socket_size+(h_unit-ks27_socket_size)/2-ks27_holder_wall_v_thickness/2+ks27_holder_wall_v_thickness_add+ks27_holder_wall_v_offset+ks27_holder_wall_v_thickness_add+ks27_holder_wall_support_width/2, -(ks27_socket_size+ks27_holder_wall_v_thickness)/2, (ks27_holder_wall_height+2)/2]) 
    {
        rotate([0,0,0])
        right_triangle(ks27_holder_wall_support_width,ks27_holder_wall_v_thickness,(ks27_holder_wall_height+2),0,0,0);
    }
}
//        }
    //右短牆
//     translate([ks27_socket_size+(h_unit-ks27_socket_size)/2-ks27_holder_wall_v_thickness/2+ks27_holder_wall_v_thickness_add+ks27_holder_wall_v_offset,-(v_unit)/2+2.5+(ks27_holder_hook_length/2),(ks27_holder_wall_height/2)]) 
//        cube([ks27_holder_wall_v_thickness,ks27_holder_hook_length, pcb_thickness+ks27_holder_wall_height ], center=true);
//
//     translate([ks27_socket_size+(h_unit-ks27_socket_size)/2-ks27_holder_wall_v_thickness/2+ks27_holder_wall_v_thickness_add+ks27_holder_wall_v_offset,-(v_unit)/2-2.5-(ks27_holder_hook_length/2),(ks27_holder_wall_height/2)]) 
//        cube([ks27_holder_wall_v_thickness,ks27_holder_hook_length, pcb_thickness+ks27_holder_wall_height ], center=true);

    //右短牆連橫牆
//    translate([ks27_socket_size+(h_unit-ks27_socket_size)/2-ks27_holder_wall_v_thickness/2+ks27_holder_wall_v_thickness_add+ks27_holder_wall_v_offset,-(v_unit)/2,(ks27_holder_wall_height/2)-ks27_holder_hook_height/2]) 
//        cube([ks27_holder_wall_v_thickness,5, pcb_thickness+ks27_holder_wall_height -ks27_holder_hook_height], center=true);


     //兩個凸起   
//     translate([ks27_socket_size+(h_unit-ks27_socket_size)/2-(ks27_holder_wall_v_thickness+ks27_holder_hook_thickness)/2+ks27_holder_wall_v_thickness_add,-(v_unit)/2+2.5+(ks27_holder_hook_length/2),(pcb_thickness+ks27_holder_hook_height)/2+ks27_holder_wall_height-ks27_holder_hook_height]) 
//
//        cube([ks27_holder_wall_v_thickness+ks27_holder_hook_thickness,ks27_holder_hook_length, ks27_holder_hook_height ], center=true);
// 
//     translate([ks27_socket_size+(h_unit-ks27_socket_size)/2-(ks27_holder_wall_v_thickness+ks27_holder_hook_thickness)/2+ks27_holder_wall_v_thickness_add,-(v_unit)/2-1.5-(ks27_holder_hook_length/2),(pcb_thickness+ks27_holder_hook_height)/2+ks27_holder_wall_height-ks27_holder_hook_height]) 
//    
//    cube([ks27_holder_wall_v_thickness+ks27_holder_hook_thickness,ks27_holder_hook_length, ks27_holder_hook_height ], center=true);

//-(ks27_holder_wall_v_thickness+ks27_holder_hook_thickness)/2
//
      translate([
          ks27_socket_size+(h_unit-ks27_socket_size)/2 -(ks27_holder_wall_v_thickness+ks27_holder_hook_thickness)/2 +ks27_holder_wall_v_thickness_add,
          -(v_unit-ks27_socket_size)/2-ks27_holder_wall_v_width_r/2,
          (pcb_thickness+ks27_holder_hook_height)/2+ks27_holder_wall_height-ks27_holder_hook_height]) 
        cubeRC([ks27_holder_wall_v_thickness+ks27_holder_hook_thickness,ks27_holder_wall_v_width_r, ks27_holder_hook_height ],rc_size=1, center=true);
//        cube([ks27_holder_wall_v_thickness+ks27_holder_hook_thickness,ks27_holder_wall_v_width_r, ks27_holder_hook_height ], center=true);
 
  
 //-0.675+1.5
 //-4.65+3
    //左牆
    translate([(h_unit-ks27_socket_size)/2+ks27_holder_wall_v_thickness/2-ks27_holder_wall_v_thickness_add-ks27_holder_wall_v_offset, -(v_unit-ks27_socket_size)/2-ks27_holder_wall_v_width_l/2, (ks27_holder_wall_height/2)]) {
        cubeRC([ks27_holder_wall_v_thickness,ks27_holder_wall_v_width_l,  pcb_thickness+ks27_holder_wall_height], center=true);
    }
    
//    translate([(h_unit-ks27_socket_size)/2+ks27_holder_wall_v_thickness/2-ks27_holder_wall_v_thickness_add-ks27_holder_wall_v_offset-ks27_holder_wall_v_thickness_add-ks27_holder_wall_support_width/2,  -(v_unit-ks27_socket_size)/2-ks27_holder_wall_v_width_l/2,  (ks27_holder_wall_height+2)/2]) {
//        rotate([0,0,90+180])
//        chamfer(ks27_holder_wall_v_width_l, ks27_holder_wall_support_width, ks27_holder_wall_height+2);
//    }

if (switch_socket_base_holder_support_frame) {

    translate([(h_unit-ks27_socket_size)/2+ks27_holder_wall_v_thickness/2-ks27_holder_wall_v_thickness_add-ks27_holder_wall_v_offset-ks27_holder_wall_v_thickness_add-ks27_holder_wall_support_width/2+ks27_holder_wall_support_width,  -(ks27_socket_size+ks27_holder_wall_v_thickness)/2,  (ks27_holder_wall_height+2)/2]) {
        right_triangle(ks27_holder_wall_support_width,ks27_holder_wall_v_thickness,(ks27_holder_wall_height+2),0,0,180);
    }
}
//     translate([(h_unit-ks27_socket_size)/2+(ks27_holder_wall_v_thickness+ks27_holder_hook_thickness)/2-ks27_holder_wall_v_thickness_add,-(v_unit-ks27_socket_size)/2-ks27_holder_wall_v_width_l/2-(ks27_holder_hook_margin1/2),(pcb_thickness+ks27_holder_hook_height)/2+ks27_holder_wall_height-ks27_holder_hook_height]) 

    //左短牆

//    translate([(h_unit-ks27_socket_size)/2+(ks27_holder_wall_v_thickness)/2-ks27_holder_wall_v_thickness_add-ks27_holder_wall_v_offset,-(v_unit)/2+2.5+(ks27_holder_hook_length/2),(ks27_holder_wall_height/2)]) 
//     #cube([ks27_holder_wall_v_thickness,ks27_holder_hook_length,  pcb_thickness+ks27_holder_wall_height ], center=true);
//
//    translate([(h_unit-ks27_socket_size)/2+ks27_holder_wall_v_thickness/2-ks27_holder_wall_v_thickness_add-ks27_holder_wall_v_offset,-(v_unit)/2-2.5-(ks27_holder_hook_length/2),(ks27_holder_wall_height/2)]) 
//     #cube([ks27_holder_wall_v_thickness,ks27_holder_hook_length,  pcb_thickness+ks27_holder_wall_height ], center=true);
//

    //左短牆連橫牆
//    translate([(h_unit-ks27_socket_size)/2+(ks27_holder_wall_v_thickness)/2-ks27_holder_wall_v_thickness_add-ks27_holder_wall_v_offset,-(v_unit)/2,(ks27_holder_wall_height/2)-ks27_holder_hook_height/2]) 
//        cube([ks27_holder_wall_v_thickness,5, pcb_thickness+ks27_holder_wall_height -ks27_holder_hook_height], center=true);
        
 
//兩短固定器 
//    translate([(h_unit-ks27_socket_size)/2+(ks27_holder_wall_v_thickness+ks27_holder_hook_thickness)/2-ks27_holder_wall_v_thickness_add,-(v_unit)/2+2.5+(ks27_holder_hook_length/2),(pcb_thickness+ks27_holder_hook_height)/2+ks27_holder_wall_height-ks27_holder_hook_height]) 
//     
//    cube([ks27_holder_wall_v_thickness+ks27_holder_hook_thickness,ks27_holder_hook_length, ks27_holder_hook_height ], center=true);
//
//     translate([(h_unit-ks27_socket_size)/2+(ks27_holder_wall_v_thickness+ks27_holder_hook_thickness)/2-ks27_holder_wall_v_thickness_add,-(v_unit)/2-1.5-(ks27_holder_hook_length/2),(pcb_thickness+ks27_holder_hook_height)/2+ks27_holder_wall_height-ks27_holder_hook_height]) 
//     
//     cube([ks27_holder_wall_v_thickness+ks27_holder_hook_thickness,ks27_holder_hook_length, ks27_holder_hook_height ], center=true);

     
// 
     
    translate([(h_unit-ks27_socket_size)/2+(ks27_holder_wall_v_thickness+ks27_holder_hook_thickness)/2-ks27_holder_wall_v_thickness_add, -(v_unit-ks27_socket_size)/2-ks27_holder_wall_v_width_l/2, (pcb_thickness+ks27_holder_hook_height)/2+ks27_holder_wall_height-ks27_holder_hook_height])
        cubeRC([ks27_holder_wall_v_thickness+ks27_holder_hook_thickness,ks27_holder_wall_v_width_l, ks27_holder_hook_height ],rc_size=1, center=true); 
//        cube([ks27_holder_wall_v_thickness+ks27_holder_hook_thickness,ks27_holder_wall_v_width_l, ks27_holder_hook_height ], center=true);
     
    translate([h_unit/2,-v_unit/2,0]) 
    //    difference() {
    union() {
        cubeRC([ks27_socket_size, ks27_socket_size+2, pcb_thickness], center=true);
        translate([0,0,border_z_offset ])
            border(
                [ks27_socket_size,ks27_socket_size+1], 
                borders, 
                pcb_thickness-2, 
                h_border_width, 
                v_border_width
            );
    }
}


//redragon_low軸加勾釦的底座
module switch_socket_base_redragon_low(borders=[1,1,1,1]) {
    //水平牆的寬度＝(垂直底座寬度─垂直實際佔用寬度)/2
    redragon_low_holder_wall_h_thickness=(v_unit_redragon_low-redragon_low_socket_size_d)/2;
    redragon_low_holder_wall_h_thickness_add=0.5;
    
    //redragon_low_holder_wall_h_thickness=redragon_low_socket_size-14+redragon_low_holder_wall_h_thickness_add;//13.8

    //       15.3x12.6 / holder w 15.6mm D 6mm(+1.5 6mm +1.5) H 3.5mm+1.5mm    

    redragon_low_holder_wall_h_width=6;
    redragon_low_holder_wall_h_width_r=3.8;
    redragon_low_holder_wall_h_width_l=4.5;
    redragon_low_holder_wall_height=2.1;  //2.2

  
    //redragon_low_holder_wall_v_thickness_add=1.5-(redragon_low_socket_size-14.5);
    //redragon_low_holder_wall_v_thickness_add=1.5;
    redragon_low_holder_wall_v_thickness_add=0;
    redragon_low_holder_wall_v_thickness=(h_unit_redragon_low-redragon_low_socket_size_w)/2;
    redragon_low_holder_wall_v_width_r=6;
    redragon_low_holder_wall_v_width_l=6;
    redragon_low_holder_wall_v_offset=0;
    redragon_low_holder_wall_support_width=1;
    
    //勾住位置
    redragon_low_holder_hook_thickness=0.35; //0.35
    redragon_low_holder_hook_height=1.3;     //1.3
    redragon_low_holder_hook_length=2;     //2.5
    redragon_low_holder_hook_margin1=3.5;     //3.5
    redragon_low_holder_hook_margin2=redragon_low_holder_hook_margin1+7;     
    
    //上牆    
    translate([
    (h_unit_redragon_low)/2,
    -redragon_low_holder_wall_h_thickness/2+redragon_low_holder_wall_h_thickness_add,
    ((redragon_low_holder_wall_height+redragon_low_holder_hook_height)/2)]) 
        cube([redragon_low_holder_wall_h_width, redragon_low_holder_wall_h_thickness+redragon_low_holder_wall_h_thickness_add, pcb_thickness+redragon_low_holder_wall_height+redragon_low_holder_hook_height], center=true);

    //下牆   
    translate([
    ((h_unit_redragon_low)/2),
    -v_unit_redragon_low+redragon_low_holder_wall_h_thickness/2-redragon_low_holder_wall_h_thickness_add,
    ((redragon_low_holder_wall_height+redragon_low_holder_hook_height)/2)]) 
        cube([redragon_low_holder_wall_h_width, redragon_low_holder_wall_h_thickness+redragon_low_holder_wall_h_thickness_add, pcb_thickness+redragon_low_holder_wall_height+redragon_low_holder_hook_height], center=true);


    
    //右牆    
    translate([
    h_unit_ks27-redragon_low_holder_wall_v_thickness/2+redragon_low_holder_wall_v_thickness_add+redragon_low_holder_wall_v_offset,
    -(v_unit_redragon_low)/2,
    ((redragon_low_holder_wall_height+redragon_low_holder_hook_height)/2)]) {
         cube([redragon_low_holder_wall_v_thickness+redragon_low_holder_wall_v_thickness_add,redragon_low_holder_wall_v_width_r,  pcb_thickness+redragon_low_holder_wall_height+redragon_low_holder_hook_height], center=true);
    }

    if (switch_socket_base_holder_support_frame) {

    translate([
    redragon_low_socket_size+(h_unit_redragon_low-redragon_low_socket_size)/2-redragon_low_holder_wall_v_thickness/2+redragon_low_holder_wall_v_thickness_add+redragon_low_holder_wall_v_offset+redragon_low_holder_wall_v_thickness_add/2+redragon_low_holder_wall_support_width/2, 
    -(v_unit_redragon_low)/2, 
    (redragon_low_holder_wall_height+2)/2]) 
    {
        rotate([0,0,0])
        right_triangle(redragon_low_holder_wall_support_width,redragon_low_holder_wall_v_thickness,(redragon_low_holder_wall_height+2),0,0,0);
    }
}

    //右短牆連橫牆

//      translate([redragon_low_socket_size+(h_unit_redragon_low-redragon_low_socket_size)/2-(redragon_low_holder_wall_v_thickness+redragon_low_holder_hook_thickness)/2+redragon_low_holder_wall_v_thickness_add,-(v_unit)/2,(pcb_thickness+redragon_low_holder_hook_height)/2+redragon_low_holder_wall_height]) 
//        cube([redragon_low_holder_wall_v_thickness+redragon_low_holder_hook_thickness,redragon_low_holder_wall_v_width_r, redragon_low_holder_hook_height ], center=true);

    hull()
    {
     translate([
     h_unit_ks27-(redragon_low_holder_wall_v_thickness+redragon_low_holder_hook_thickness)/2+redragon_low_holder_wall_v_thickness_add+redragon_low_holder_wall_v_offset,
     -(v_unit_redragon_low)/2,
     (pcb_thickness)/2+redragon_low_holder_wall_height+redragon_low_holder_hook_height]) 
        cube([redragon_low_holder_wall_v_thickness+redragon_low_holder_hook_thickness,redragon_low_holder_wall_v_width_r, 0.001 ], center=true);
        
     translate([
     h_unit_ks27-(redragon_low_holder_wall_v_thickness+redragon_low_holder_hook_thickness)/2+redragon_low_holder_wall_v_thickness_add+redragon_low_holder_wall_v_offset,
     -(v_unit)/2,
     (pcb_thickness)/2+redragon_low_holder_wall_height]) 
        cube([redragon_low_holder_wall_v_thickness-redragon_low_holder_hook_thickness,redragon_low_holder_wall_v_width_r, 0.001 ], center=true);
    }
        
    //左牆   
    translate([
     redragon_low_holder_wall_v_thickness/2-redragon_low_holder_wall_v_thickness_add-redragon_low_holder_wall_v_offset,
    -(v_unit_redragon_low)/2, 
    ((redragon_low_holder_wall_height+redragon_low_holder_hook_height)/2)]) {
        cube([redragon_low_holder_wall_v_thickness+redragon_low_holder_wall_v_thickness_add,redragon_low_holder_wall_v_width_l,  pcb_thickness+redragon_low_holder_wall_height+redragon_low_holder_hook_height], center=true);
    }
    
if (switch_socket_base_holder_support_frame) {

    translate([
    (h_unit_redragon_low-redragon_low_socket_size)/2+redragon_low_holder_wall_v_thickness/2-redragon_low_holder_wall_v_thickness_add-redragon_low_holder_wall_v_offset-redragon_low_holder_wall_v_thickness_add/2-redragon_low_holder_wall_support_width/2+redragon_low_holder_wall_support_width,  
    -(v_unit_redragon_low)/2,  
    (redragon_low_holder_wall_height+2)/2]) {
        right_triangle(redragon_low_holder_wall_support_width,redragon_low_holder_wall_v_thickness,(redragon_low_holder_wall_height+2),0,0,180);
    }
}

    //左短牆連橫牆
   
//    translate([(h_unit_redragon_low-redragon_low_socket_size)/2+(redragon_low_holder_wall_v_thickness+redragon_low_holder_hook_thickness)/2-redragon_low_holder_wall_v_thickness_add, -(v_unit)/2, (pcb_thickness+redragon_low_holder_hook_height)/2+redragon_low_holder_wall_height])
//        cube([redragon_low_holder_wall_v_thickness+redragon_low_holder_hook_thickness,redragon_low_holder_wall_v_width_l, redragon_low_holder_hook_height ], center=true); 

    hull()
    {
    translate([
    redragon_low_holder_wall_v_thickness/2-redragon_low_holder_wall_v_thickness_add+redragon_low_holder_hook_thickness/2, 
    -(v_unit_redragon_low)/2, 
    (pcb_thickness)/2+redragon_low_holder_wall_height+redragon_low_holder_hook_height])
        cube([redragon_low_holder_wall_v_thickness+redragon_low_holder_hook_thickness,redragon_low_holder_wall_v_width_l, 0.0001 ], center=true); 
   
    translate([
    redragon_low_holder_wall_v_thickness/2-redragon_low_holder_wall_v_thickness_add+redragon_low_holder_hook_thickness/2, 
    -(v_unit_redragon_low)/2, 
    (pcb_thickness)/2+redragon_low_holder_wall_height])
        cube([redragon_low_holder_wall_v_thickness-redragon_low_holder_hook_thickness,redragon_low_holder_wall_v_width_l, 0.0001 ], center=true); 
    }
        
    translate([h_unit_redragon_low/2,-v_unit_redragon_low/2,0]) 
    //    difference() {
    union() {
        cube([redragon_low_socket_size, redragon_low_socket_size, pcb_thickness], center=true);
        translate([0,0,border_z_offset ])
            border(
                [redragon_low_socket_size,redragon_low_socket_size], 
                borders, 
                pcb_thickness-2, 
                h_border_width, 
                v_border_width
            );
    }
}


//fraly軸加勾釦的底座
module switch_socket_base_fraly(borders=[1,1,1,1]) {
    //fraly_holder_wall_h_thickness=(h_unit/2)-(14.5/2);
    //fraly_holder_wall_h_thickness_add=1.5-(fraly_socket_size-13.8);
    //fraly_holder_wall_h_thickness_add=0;
    
    //fraly_holder_wall_h_thickness=fraly_socket_size-14+fraly_holder_wall_h_thickness_add;//13.8
    fraly_holder_wall_h_width_r=3.8;
    fraly_holder_wall_h_width_l=4.5;
    fraly_holder_wall_height=2.2;  //2.2


//    //上牆 
//    translate([fraly_socket_size+(h_unit-fraly_socket_size)/2-fraly_holder_wall_h_width_r/2,-(v_unit-fraly_socket_size)/2-fraly_holder_wall_h_thickness/2+fraly_holder_wall_h_thickness_add,(fraly_holder_wall_height/2)]) 
//        cube([fraly_holder_wall_h_width_r, fraly_holder_wall_h_thickness, pcb_thickness+fraly_holder_wall_height], center=true);
//
//    translate([(h_unit-fraly_socket_size)/2+fraly_holder_wall_h_width_l/2,-(v_unit-fraly_socket_size)/2-fraly_holder_wall_h_thickness/2+fraly_holder_wall_h_thickness_add,(fraly_holder_wall_height/2)]) 
//        cube([fraly_holder_wall_h_width_l, fraly_holder_wall_h_thickness, pcb_thickness+fraly_holder_wall_height], center=true);

    //fraly_holder_wall_v_thickness_add=1.5-(fraly_socket_size-14.5);
    fraly_holder_wall_v_thickness_add=2;
    //fraly_holder_wall_v_thickness_add=0;
    fraly_holder_wall_v_thickness=fraly_socket_size-14.8+fraly_holder_wall_v_thickness_add;
    fraly_holder_wall_v_width_r=4.8+7.85-0.56;
    fraly_holder_wall_v_width_l=4.8+7.85-0.56;
    fraly_holder_wall_v_offset=0.2;
    fraly_holder_wall_support_width=1;
    
    //勾住位置
    fraly_holder_hook_thickness=0.35; //0.35
    fraly_holder_hook_height=1;     //1.3
    fraly_holder_hook_length=2;     //2.5
    fraly_holder_hook_margin1=3.5;     //3.5
    fraly_holder_hook_margin2=fraly_holder_hook_margin1+7;     //10.5
//-4.65+3
//-0.675
    //右牆
    translate([fraly_socket_size+(h_unit-fraly_socket_size)/2-fraly_holder_wall_v_thickness/2+fraly_holder_wall_v_thickness_add+fraly_holder_wall_v_offset,-(v_unit-fraly_socket_size)/2-fraly_holder_wall_v_width_r/2,(fraly_holder_wall_height/2)]) {
         cubeRC([fraly_holder_wall_v_thickness,fraly_holder_wall_v_width_r,  pcb_thickness+fraly_holder_wall_height], center=true);
    }
//    
//    translate([fraly_socket_size+(h_unit-fraly_socket_size)/2-fraly_holder_wall_v_thickness/2+fraly_holder_wall_v_thickness_add+fraly_holder_wall_v_offset+fraly_holder_wall_v_thickness_add+fraly_holder_wall_support_width/2, -(v_unit-fraly_socket_size)/2-fraly_holder_wall_v_width_r/2, (fraly_holder_wall_height+2)/2]) 
//    {
//        rotate([0,0,90])
//        chamfer(fraly_holder_wall_v_width_r, fraly_holder_wall_support_width, fraly_holder_wall_height+2);
//    
//    }
//    
   //-(v_unit-fraly_socket_size)/2-fraly_holder_wall_v_width_r/2

    if (switch_socket_base_holder_support_frame) {

    translate([fraly_socket_size+(h_unit-fraly_socket_size)/2-fraly_holder_wall_v_thickness/2+fraly_holder_wall_v_thickness_add+fraly_holder_wall_v_offset+fraly_holder_wall_v_thickness_add+fraly_holder_wall_support_width/2, -(fraly_socket_size+fraly_holder_wall_v_thickness)/2, (fraly_holder_wall_height+2)/2]) 
    {
        rotate([0,0,0])
        right_triangle(fraly_holder_wall_support_width,fraly_holder_wall_v_thickness,(fraly_holder_wall_height+2),0,0,0);
    }
}
//        }
    //右短牆
//     translate([fraly_socket_size+(h_unit-fraly_socket_size)/2-fraly_holder_wall_v_thickness/2+fraly_holder_wall_v_thickness_add+fraly_holder_wall_v_offset,-(v_unit)/2+2.5+(fraly_holder_hook_length/2),(fraly_holder_wall_height/2)]) 
//        cube([fraly_holder_wall_v_thickness,fraly_holder_hook_length, pcb_thickness+fraly_holder_wall_height ], center=true);
//
//     translate([fraly_socket_size+(h_unit-fraly_socket_size)/2-fraly_holder_wall_v_thickness/2+fraly_holder_wall_v_thickness_add+fraly_holder_wall_v_offset,-(v_unit)/2-2.5-(fraly_holder_hook_length/2),(fraly_holder_wall_height/2)]) 
//        cube([fraly_holder_wall_v_thickness,fraly_holder_hook_length, pcb_thickness+fraly_holder_wall_height ], center=true);

    //右短牆連橫牆
//    translate([fraly_socket_size+(h_unit-fraly_socket_size)/2-fraly_holder_wall_v_thickness/2+fraly_holder_wall_v_thickness_add+fraly_holder_wall_v_offset,-(v_unit)/2,(fraly_holder_wall_height/2)-fraly_holder_hook_height/2]) 
//        cube([fraly_holder_wall_v_thickness,5, pcb_thickness+fraly_holder_wall_height -fraly_holder_hook_height], center=true);


     //兩個凸起   
//     translate([fraly_socket_size+(h_unit-fraly_socket_size)/2-(fraly_holder_wall_v_thickness+fraly_holder_hook_thickness)/2+fraly_holder_wall_v_thickness_add,-(v_unit)/2+2.5+(fraly_holder_hook_length/2),(pcb_thickness+fraly_holder_hook_height)/2+fraly_holder_wall_height-fraly_holder_hook_height]) 
//
//        cube([fraly_holder_wall_v_thickness+fraly_holder_hook_thickness,fraly_holder_hook_length, fraly_holder_hook_height ], center=true);
// 
//     translate([fraly_socket_size+(h_unit-fraly_socket_size)/2-(fraly_holder_wall_v_thickness+fraly_holder_hook_thickness)/2+fraly_holder_wall_v_thickness_add,-(v_unit)/2-1.5-(fraly_holder_hook_length/2),(pcb_thickness+fraly_holder_hook_height)/2+fraly_holder_wall_height-fraly_holder_hook_height]) 
//    
//    cube([fraly_holder_wall_v_thickness+fraly_holder_hook_thickness,fraly_holder_hook_length, fraly_holder_hook_height ], center=true);

//-(fraly_holder_wall_v_thickness+fraly_holder_hook_thickness)/2
//
      translate([
          fraly_socket_size+(h_unit-fraly_socket_size)/2 -(fraly_holder_wall_v_thickness+fraly_holder_hook_thickness)/2 +fraly_holder_wall_v_thickness_add,
          -(v_unit-fraly_socket_size)/2-fraly_holder_wall_v_width_r/2,
          (pcb_thickness+fraly_holder_hook_height)/2+fraly_holder_wall_height-fraly_holder_hook_height]) 
        cubeRC([fraly_holder_wall_v_thickness+fraly_holder_hook_thickness,fraly_holder_wall_v_width_r, fraly_holder_hook_height ],rc_size=1, center=true);
//        cube([fraly_holder_wall_v_thickness+fraly_holder_hook_thickness,fraly_holder_wall_v_width_r, fraly_holder_hook_height ], center=true);
 
  
 //-0.675+1.5
 //-4.65+3
    //左牆
    translate([(h_unit-fraly_socket_size)/2+fraly_holder_wall_v_thickness/2-fraly_holder_wall_v_thickness_add-fraly_holder_wall_v_offset, -(v_unit-fraly_socket_size)/2-fraly_holder_wall_v_width_l/2, (fraly_holder_wall_height/2)]) {
        cubeRC([fraly_holder_wall_v_thickness,fraly_holder_wall_v_width_l,  pcb_thickness+fraly_holder_wall_height], center=true);
    }
    
//    translate([(h_unit-fraly_socket_size)/2+fraly_holder_wall_v_thickness/2-fraly_holder_wall_v_thickness_add-fraly_holder_wall_v_offset-fraly_holder_wall_v_thickness_add-fraly_holder_wall_support_width/2,  -(v_unit-fraly_socket_size)/2-fraly_holder_wall_v_width_l/2,  (fraly_holder_wall_height+2)/2]) {
//        rotate([0,0,90+180])
//        chamfer(fraly_holder_wall_v_width_l, fraly_holder_wall_support_width, fraly_holder_wall_height+2);
//    }

if (switch_socket_base_holder_support_frame) {

    translate([(h_unit-fraly_socket_size)/2+fraly_holder_wall_v_thickness/2-fraly_holder_wall_v_thickness_add-fraly_holder_wall_v_offset-fraly_holder_wall_v_thickness_add-fraly_holder_wall_support_width/2+fraly_holder_wall_support_width,  -(fraly_socket_size+fraly_holder_wall_v_thickness)/2,  (fraly_holder_wall_height+2)/2]) {
        right_triangle(fraly_holder_wall_support_width,fraly_holder_wall_v_thickness,(fraly_holder_wall_height+2),0,0,180);
    }
}
//     translate([(h_unit-fraly_socket_size)/2+(fraly_holder_wall_v_thickness+fraly_holder_hook_thickness)/2-fraly_holder_wall_v_thickness_add,-(v_unit-fraly_socket_size)/2-fraly_holder_wall_v_width_l/2-(fraly_holder_hook_margin1/2),(pcb_thickness+fraly_holder_hook_height)/2+fraly_holder_wall_height-fraly_holder_hook_height]) 

    //左短牆

//    translate([(h_unit-fraly_socket_size)/2+(fraly_holder_wall_v_thickness)/2-fraly_holder_wall_v_thickness_add-fraly_holder_wall_v_offset,-(v_unit)/2+2.5+(fraly_holder_hook_length/2),(fraly_holder_wall_height/2)]) 
//     #cube([fraly_holder_wall_v_thickness,fraly_holder_hook_length,  pcb_thickness+fraly_holder_wall_height ], center=true);
//
//    translate([(h_unit-fraly_socket_size)/2+fraly_holder_wall_v_thickness/2-fraly_holder_wall_v_thickness_add-fraly_holder_wall_v_offset,-(v_unit)/2-2.5-(fraly_holder_hook_length/2),(fraly_holder_wall_height/2)]) 
//     #cube([fraly_holder_wall_v_thickness,fraly_holder_hook_length,  pcb_thickness+fraly_holder_wall_height ], center=true);
//

    //左短牆連橫牆
//    translate([(h_unit-fraly_socket_size)/2+(fraly_holder_wall_v_thickness)/2-fraly_holder_wall_v_thickness_add-fraly_holder_wall_v_offset,-(v_unit)/2,(fraly_holder_wall_height/2)-fraly_holder_hook_height/2]) 
//        cube([fraly_holder_wall_v_thickness,5, pcb_thickness+fraly_holder_wall_height -fraly_holder_hook_height], center=true);
        
 
//兩短固定器 
//    translate([(h_unit-fraly_socket_size)/2+(fraly_holder_wall_v_thickness+fraly_holder_hook_thickness)/2-fraly_holder_wall_v_thickness_add,-(v_unit)/2+2.5+(fraly_holder_hook_length/2),(pcb_thickness+fraly_holder_hook_height)/2+fraly_holder_wall_height-fraly_holder_hook_height]) 
//     
//    cube([fraly_holder_wall_v_thickness+fraly_holder_hook_thickness,fraly_holder_hook_length, fraly_holder_hook_height ], center=true);
//
//     translate([(h_unit-fraly_socket_size)/2+(fraly_holder_wall_v_thickness+fraly_holder_hook_thickness)/2-fraly_holder_wall_v_thickness_add,-(v_unit)/2-1.5-(fraly_holder_hook_length/2),(pcb_thickness+fraly_holder_hook_height)/2+fraly_holder_wall_height-fraly_holder_hook_height]) 
//     
//     cube([fraly_holder_wall_v_thickness+fraly_holder_hook_thickness,fraly_holder_hook_length, fraly_holder_hook_height ], center=true);

     
// 
     
    translate([(h_unit-fraly_socket_size)/2+(fraly_holder_wall_v_thickness+fraly_holder_hook_thickness)/2-fraly_holder_wall_v_thickness_add, -(v_unit-fraly_socket_size)/2-fraly_holder_wall_v_width_l/2, (pcb_thickness+fraly_holder_hook_height)/2+fraly_holder_wall_height-fraly_holder_hook_height])
        cubeRC([fraly_holder_wall_v_thickness+fraly_holder_hook_thickness,fraly_holder_wall_v_width_l, fraly_holder_hook_height ],rc_size=1, center=true); 
//        cube([fraly_holder_wall_v_thickness+fraly_holder_hook_thickness,fraly_holder_wall_v_width_l, fraly_holder_hook_height ], center=true);
     
    translate([h_unit/2,-v_unit/2,0]) 
    //    difference() {
    union() {
        cubeRC([fraly_socket_size, fraly_socket_size+2, pcb_thickness], center=true);
        translate([0,0,border_z_offset ])
            border(
                [fraly_socket_size,fraly_socket_size+1], 
                borders, 
                pcb_thickness-2, 
                h_border_width, 
                v_border_width
            );
    }
}


// alps: pin L:4.3 T:0.3 W:1.1
//       2 pin w 6mm s 3.8mm / 11.2-(12.6/2)
//       15.3x12.6 / holder w 15.6mm D 6mm(+1.5 6mm +1.5) H 3.5mm+1.5mm


//ALPS軸加勾釦的底座
module switch_socket_base_alps(borders=[1,1,1,1]) {
    alps_holder_wall_h_thickness=(h_unit/2)-(alps_socket_size_d/2);
    alps_holder_wall_h_thickness_add=0;
    
    //alps_holder_wall_h_thickness=alps_socket_size-14+alps_holder_wall_h_thickness_add;//13.8

    //       15.3x12.6 / holder w 15.6mm D 6mm(+1.5 6mm +1.5) H 3.5mm+1.5mm    

    alps_holder_wall_h_width=6;
    alps_holder_wall_h_width_r=3.8;
    alps_holder_wall_h_width_l=4.5;
    alps_holder_wall_height=3.5;  //2.2

//    //檢測用
//    if (base_pcb_layout_ShowVKeySwitch) {
//        //軸體 [VKeySwitch_Size_x,VKeySwitch_Size_y,VKeySwitch_Size_z]
//        %translate([h_unit/2,-v_unit/2,(pcb_thickness+VKeySwitch_Size[2])/2])
//            cube(VKeySwitch_Size,center=true);   
//    }
//    
//    if (base_pcb_layout_ShowVKeycap) {
//        //鍵帽 [VKeycap_Size_x,VKeycap_Size_y,VKeycap_Size_z]
//        %translate([h_unit/2,-v_unit/2,(pcb_thickness+VKeycap_Size[2])/2+VKeySwitch_Size[2]])
//            color(VKeycap_Color,VKeycap_Alpha) cube(VKeycap_Size,center=true);
//    }
    

        
    //alps_holder_wall_v_thickness_add=1.5-(alps_socket_size-14.5);
    alps_holder_wall_v_thickness_add=1.5;
    //alps_holder_wall_v_thickness_add=0;
    alps_holder_wall_v_thickness=alps_socket_size-alps_socket_size_w+alps_holder_wall_v_thickness_add;
    alps_holder_wall_v_width_r=6;
    alps_holder_wall_v_width_l=6;
    alps_holder_wall_v_offset=0.2;
    alps_holder_wall_support_width=1;
    
    //勾住位置
    alps_holder_hook_thickness=0.35; //0.35
    alps_holder_hook_height=1.3;     //1.3
    alps_holder_hook_length=2;     //2.5
    alps_holder_hook_margin1=3.5;     //3.5
    alps_holder_hook_margin2=alps_holder_hook_margin1+7;     
    
    //上牆 
    translate([
    (alps_socket_size)/2,
    -(v_unit-alps_socket_size)/2-alps_holder_wall_h_thickness/2+alps_holder_wall_h_thickness_add,
    ((alps_holder_wall_height+alps_holder_hook_height)/2)]) 
        cube([alps_holder_wall_h_width_l, alps_holder_wall_h_thickness, pcb_thickness+alps_holder_wall_height+alps_holder_hook_height], center=true);

    //下牆
    translate([
    ((h_unit)/2),
    (-(v_unit-alps_socket_size)/2-alps_holder_wall_h_thickness/2+alps_holder_wall_h_thickness_add) - alps_socket_size_d -alps_holder_wall_h_thickness,
    
    ((alps_holder_wall_height+alps_holder_hook_height)/2)]) 
        cube([alps_holder_wall_h_width, alps_holder_wall_h_thickness, pcb_thickness+alps_holder_wall_height+alps_holder_hook_height], center=true);


    
    //右牆
    translate([
    alps_socket_size+(h_unit-alps_socket_size)/2-alps_holder_wall_v_thickness/2+alps_holder_wall_v_thickness_add+alps_holder_wall_v_offset,
    -(v_unit)/2,
    ((alps_holder_wall_height+alps_holder_hook_height)/2)]) {
         cube([alps_holder_wall_v_thickness,alps_holder_wall_v_width_r,  pcb_thickness+alps_holder_wall_height+alps_holder_hook_height], center=true);
    }

    if (switch_socket_base_holder_support_frame) {

    translate([
    alps_socket_size+(h_unit-alps_socket_size)/2-alps_holder_wall_v_thickness/2+alps_holder_wall_v_thickness_add+alps_holder_wall_v_offset+alps_holder_wall_v_thickness_add/2+alps_holder_wall_support_width/2, 
    -(v_unit)/2, 
    (alps_holder_wall_height+2)/2]) 
    {
        rotate([0,0,0])
        right_triangle(alps_holder_wall_support_width,alps_holder_wall_v_thickness,(alps_holder_wall_height+2),0,0,0);
    }
}

    //右短牆連橫牆

//      translate([alps_socket_size+(h_unit-alps_socket_size)/2-(alps_holder_wall_v_thickness+alps_holder_hook_thickness)/2+alps_holder_wall_v_thickness_add,-(v_unit)/2,(pcb_thickness+alps_holder_hook_height)/2+alps_holder_wall_height]) 
//        cube([alps_holder_wall_v_thickness+alps_holder_hook_thickness,alps_holder_wall_v_width_r, alps_holder_hook_height ], center=true);
    hull()
    {
     translate([
     alps_socket_size+(h_unit-alps_socket_size)/2-(alps_holder_wall_v_thickness+alps_holder_hook_thickness)/2+alps_holder_wall_v_thickness_add,
     -(v_unit)/2,
     (pcb_thickness)/2+alps_holder_wall_height+alps_holder_hook_height]) 
        cube([alps_holder_wall_v_thickness+alps_holder_hook_thickness,alps_holder_wall_v_width_r, 0.001 ], center=true);
        
     translate([
     alps_socket_size+(h_unit-alps_socket_size)/2-(alps_holder_wall_v_thickness+alps_holder_hook_thickness)/2+alps_holder_wall_v_thickness_add,
     -(v_unit)/2,
     (pcb_thickness)/2+alps_holder_wall_height]) 
        cube([alps_holder_wall_v_thickness-alps_holder_hook_thickness,alps_holder_wall_v_width_r, 0.001 ], center=true);
    }
        
    //左牆
    translate([
    (h_unit-alps_socket_size)/2+alps_holder_wall_v_thickness/2-alps_holder_wall_v_thickness_add-alps_holder_wall_v_offset, 
    -(v_unit)/2, 
    ((alps_holder_wall_height+alps_holder_hook_height)/2)]) {
        cube([alps_holder_wall_v_thickness,alps_holder_wall_v_width_l,  pcb_thickness+alps_holder_wall_height+alps_holder_hook_height], center=true);
    }
    
if (switch_socket_base_holder_support_frame) {

    translate([
    (h_unit-alps_socket_size)/2+alps_holder_wall_v_thickness/2-alps_holder_wall_v_thickness_add-alps_holder_wall_v_offset-alps_holder_wall_v_thickness_add/2-alps_holder_wall_support_width/2+alps_holder_wall_support_width,  
    -(v_unit)/2,  
    (alps_holder_wall_height+2)/2]) {
        right_triangle(alps_holder_wall_support_width,alps_holder_wall_v_thickness,(alps_holder_wall_height+2),0,0,180);
    }
}

    //左短牆連橫牆
   
//    translate([(h_unit-alps_socket_size)/2+(alps_holder_wall_v_thickness+alps_holder_hook_thickness)/2-alps_holder_wall_v_thickness_add, -(v_unit)/2, (pcb_thickness+alps_holder_hook_height)/2+alps_holder_wall_height])
//        cube([alps_holder_wall_v_thickness+alps_holder_hook_thickness,alps_holder_wall_v_width_l, alps_holder_hook_height ], center=true); 

    hull()
    {
    translate([
    (h_unit-alps_socket_size)/2+(alps_holder_wall_v_thickness+alps_holder_hook_thickness)/2-alps_holder_wall_v_thickness_add, 
    -(v_unit)/2, 
    (pcb_thickness)/2+alps_holder_wall_height+alps_holder_hook_height])
        cube([alps_holder_wall_v_thickness+alps_holder_hook_thickness,alps_holder_wall_v_width_l, 0.0001 ], center=true); 
   
    translate([
    (h_unit-alps_socket_size)/2+(alps_holder_wall_v_thickness+alps_holder_hook_thickness)/2-alps_holder_wall_v_thickness_add, 
    -(v_unit)/2, 
    (pcb_thickness)/2+alps_holder_wall_height])
        cube([alps_holder_wall_v_thickness-alps_holder_hook_thickness,alps_holder_wall_v_width_l, 0.0001 ], center=true); 
    }
        
    translate([h_unit/2,-v_unit/2,0]) 
    //    difference() {
    union() {
        cube([alps_socket_size, alps_socket_size, pcb_thickness], center=true);
        translate([0,0,border_z_offset ])
            border(
                [alps_socket_size,alps_socket_size], 
                borders, 
                pcb_thickness-2, 
                h_border_width, 
                v_border_width
            );
    }
}

module switch_socket_base_mx(borders=[1,1,1,1]) {
    //MX軸的定位板為方形14mm的空間
    //因此模擬溝槽的部分，應該是夾起來要14mm
    //也就是牆厚與鉤子寬度不論怎麼設定，都要讓空間保留14mm
    //頂多少0.5mm做為緩衝
    
    //多0.5是預留給卡榫的空間
    mx_socket_size_v =14.5; //+0.25;
    mx_socket_size_h =14; //+0.25;
    //mx_holder_wall_h_thickness=(h_unit/2)-(14.5/2);
    
    //mx_holder_wall_h_thickness_add=1.25-(socket_size-mx_socket_size_v);
    //mx_holder_wall_v_thickness_add=1.25-(socket_size-mx_socket_size_v);
    
    mx_holder_wall_h_thickness_add=1;
    mx_holder_wall_v_thickness_add=1;
    
    //socket_size=15
    mx_holder_wall_h_thickness=15-mx_socket_size_v+mx_holder_wall_h_thickness_add;
    
    mx_holder_wall_v_thickness=15-mx_socket_size_h+mx_holder_wall_v_thickness_add;
    
    mx_holder_wall_h_width_u=17; //5 //10;
    mx_holder_wall_h_width_d=17; //5 //10;
    mx_holder_wall_h_width=10; 
    mx_holder_wall_h_width_u_offset=0;// 5/2;
    mx_holder_wall_h_width_d_offset=0; //5/2;
    mx_holder_wall_v_width_u_offset=-0.3;// 5/2;
    mx_holder_wall_v_width_d_offset=0.3; //5/2;

    mx_holder_wall_v_width_r=17.5; //5 //16;
    mx_holder_wall_v_width_l=17.5; //4.5
    mx_holder_wall_v_width_ru=3; //5 //16;
    mx_holder_wall_v_width_lu=3; //4.5
    mx_holder_wall_v_width_rd=3; //5 //16;
    mx_holder_wall_v_width_ld=3; //4.5
    mx_holder_wall_v_width=5; 
    mx_holder_wall_v_width_r_offset=0;
    mx_holder_wall_v_width_l_offset=0;
    mx_holder_wall_v_width_ru_offset=0.25-(v_unit-17)/2;
    mx_holder_wall_v_width_lu_offset=0.25-(v_unit-17)/2;
    mx_holder_wall_v_width_rd_offset=0.25+(v_unit-17)/2;
    mx_holder_wall_v_width_ld_offset=0.25+(v_unit-17)/2;
    
    mx_holder_wall_height=5; //5

    mx_holder_hook_thickness=0.45; //0.25->0.45 resin test result
    mx_holder_hook_height=1.4;//1.4;     //1.3
    mx_holder_hook_length=14; //5;     //2.5
    mx_holder_hook_margin1=3.5;     //3.5
    mx_holder_hook_margin2=mx_holder_hook_margin1+7;     //10.5

    
//    //檢測用
//    if (base_pcb_layout_ShowVKeySwitch) {
//        //軸體 [VKeySwitch_Size_x,VKeySwitch_Size_y,VKeySwitch_Size_z]
//        %translate([h_unit/2,-v_unit/2,(pcb_thickness+5)/2])
//            cube(VKeySwitch_Size,center=true);   
//    }
//    
//    if (base_pcb_layout_ShowVKeycap) {
//        //鍵帽 [VKeycap_Size_x,VKeycap_Size_y,VKeycap_Size_z]
//        %translate([h_unit/2,-v_unit/2,(pcb_thickness+5)/2+5.5])
//            cube(VKeycap_Size,center=true);
//    }
    
//     
//    echo("pcb_thickness:",pcb_thickness);
//    echo("socket_size:",socket_size);
//    echo("unit:", unit);
//    echo("v_unit:", v_unit);
//    echo("h_unit:", h_unit);
//    echo("mx_socket_size_v",mx_socket_size_v);
//    echo("mx_holder_wall_h_thickness:",mx_holder_wall_h_thickness);
//    echo("mx_holder_wall_h_thickness_add:",mx_holder_wall_h_thickness_add)
     
//上牆
    translate([unit/2+mx_holder_wall_h_width_u_offset, -(v_unit-mx_socket_size_v)/2 + mx_holder_wall_h_thickness/2 + mx_holder_wall_v_width_u_offset, (mx_holder_wall_height-5)/2]) 
        cube([mx_holder_wall_h_width_u, mx_holder_wall_h_thickness, pcb_thickness+mx_holder_wall_height-5], center=true);

    //鉤子
    translate([unit/2, -(v_unit-mx_socket_size_v)/2 + mx_holder_wall_h_thickness/2 - mx_holder_hook_thickness/2,(pcb_thickness+mx_holder_hook_height)/2+mx_holder_wall_height-mx_holder_hook_height]) 
     
        cube([mx_holder_hook_length, mx_holder_wall_h_thickness+mx_holder_hook_thickness, mx_holder_hook_height ], center=true);
    
    //支撐
    if (switch_socket_base_holder_support_frame) {

    translate([unit/2 - mx_holder_wall_h_thickness /2 , -(v_unit-mx_socket_size_v)/2 +   mx_holder_wall_h_thickness + mx_holder_wall_support_width/2, (mx_holder_wall_height)/2]) 
    {
        rotate([0,0,90])
        right_triangle(mx_holder_wall_support_width,mx_holder_wall_h_thickness,(mx_holder_wall_height+pcb_thickness),0,0,0);
    }

    }
//下牆
    translate([h_unit/2+mx_holder_wall_h_width_d_offset, -v_unit/2-mx_holder_wall_h_thickness/2-mx_socket_size_v/2 + mx_holder_wall_v_width_d_offset, ((mx_holder_wall_height-5)/2)]) 
        cube([mx_holder_wall_h_width_d, mx_holder_wall_h_thickness, pcb_thickness+mx_holder_wall_height-5], center=true);



    //鉤子
    translate([h_unit/2, -v_unit/2-mx_holder_wall_h_thickness/2-mx_socket_size_v/2+mx_holder_hook_thickness/2, (pcb_thickness+mx_holder_hook_height)/2+mx_holder_wall_height-mx_holder_hook_height]) 
     
        cube([mx_holder_hook_length, mx_holder_wall_h_thickness+mx_holder_hook_thickness, mx_holder_hook_height ], center=true);

//支撐
    if (switch_socket_base_holder_support_frame) {
    translate([h_unit/2 + mx_holder_wall_h_thickness/2 , -v_unit/2-mx_holder_wall_h_thickness-mx_socket_size_v/2 -  mx_holder_wall_support_width/2, (mx_holder_wall_height/2)])
    {
        rotate([0,0,-90])
        right_triangle(mx_holder_wall_support_width,mx_holder_wall_h_thickness,(mx_holder_wall_height+pcb_thickness),0,0,0);
    }
}
    
    
    mx_holder_wall_v_offset=0.2;
    mx_holder_wall_support_width=1;
    

//    //右牆
//    translate([(h_unit)/2 + mx_socket_size_h/2 +mx_holder_wall_v_thickness/2, -(v_unit)/2+mx_holder_wall_v_width_r_offset, (mx_holder_wall_height/2)]) {
//        cube([mx_holder_wall_v_thickness,mx_holder_wall_v_width_r,  pcb_thickness+mx_holder_wall_height], center=true);
//    }
//    
//    //左牆
//    translate([(h_unit)/2 - mx_socket_size_h/2 -mx_holder_wall_v_thickness/2 , -(v_unit)/2 +mx_holder_wall_v_width_l_offset, (mx_holder_wall_height/2)]) {
//        cube([mx_holder_wall_v_thickness,mx_holder_wall_v_width_l,  pcb_thickness+mx_holder_wall_height], center=true);
//    }
    
    //右牆-兩側式
    //-(v_unit)/2
    translate([(h_unit)/2 + mx_socket_size_h/2 +mx_holder_wall_v_thickness/2, -mx_holder_wall_v_width_ru/2 +mx_holder_wall_v_width_ru_offset, (mx_holder_wall_height/2)]) {
        cube([mx_holder_wall_v_thickness,mx_holder_wall_v_width_ru,  pcb_thickness+mx_holder_wall_height], center=true);
    }

    translate([(h_unit)/2 + mx_socket_size_h/2 +mx_holder_wall_v_thickness/2, -14 - (mx_holder_wall_v_width_rd/2) -mx_holder_wall_v_width_rd_offset, (mx_holder_wall_height/2)]) {
        cube([mx_holder_wall_v_thickness,mx_holder_wall_v_width_rd,  pcb_thickness+mx_holder_wall_height], center=true);
    }
    
    //左牆-兩側式
    //
    translate([(h_unit)/2 - mx_socket_size_h/2 -mx_holder_wall_v_thickness/2 , -(mx_holder_wall_v_width_lu)/2 +mx_holder_wall_v_width_lu_offset, (mx_holder_wall_height/2)]) {
        cube([mx_holder_wall_v_thickness,mx_holder_wall_v_width_lu,  pcb_thickness+mx_holder_wall_height], center=true);
    }
    
    translate([(h_unit)/2 - mx_socket_size_h/2 -mx_holder_wall_v_thickness/2 ,-14 -(mx_holder_wall_v_width_ld)/2 - mx_holder_wall_v_width_ld_offset, (mx_holder_wall_height/2)]) {
        cube([mx_holder_wall_v_thickness,mx_holder_wall_v_width_ld,  pcb_thickness+mx_holder_wall_height], center=true);
    }

 
/////

    translate([h_unit/2,-v_unit/2,0]) 
    //    difference() {
    union() {
        cube([socket_size, socket_size, pcb_thickness], center=true);
        translate([0,0,border_z_offset ])
            border(
                [socket_size,socket_size], 
                borders, 
                pcb_thickness-2, 
                h_border_width, 
                v_border_width
            );
    }
}

module switch_socket_base_mx_stabilizer(borders=[1,1,1,1]) {
    //MX軸的定位板為方形14mm的空間
    //因此模擬溝槽的部分，應該是夾起來要14mm
    //也就是牆厚與鉤子寬度不論怎麼設定，都要讓空間保留14mm
    //頂多少0.5mm做為緩衝
    //
    //stabilizer 用的版本
    
    //多0.5是預留給卡榫的空間
    mx_socket_size_v =14.5; //+0.25;
    mx_socket_size_h =14; //+0.25;
    //mx_holder_wall_h_thickness=(h_unit_stb/2)-(14.5/2);
    
    //mx_holder_wall_h_thickness_add=1.25-(socket_size-mx_socket_size_v);
    //mx_holder_wall_v_thickness_add=1.25-(socket_size-mx_socket_size_v);
    
    mx_holder_wall_h_thickness_add=0.3;
    mx_holder_wall_v_thickness_add=0.3;
    
    //socket_size=15
    mx_holder_wall_h_thickness=15-mx_socket_size_v+mx_holder_wall_h_thickness_add;
    
    mx_holder_wall_v_thickness=15-mx_socket_size_h+mx_holder_wall_v_thickness_add;
    
    mx_holder_wall_h_width_u=17; //5 //10;
    mx_holder_wall_h_width_d=16.5; //5 //10;
    mx_holder_wall_h_width=10; 
    mx_holder_wall_h_width_u_offset=0;// 5/2;
    mx_holder_wall_h_width_d_offset=0; //5/2;
    mx_holder_wall_v_width_u_offset=-0.3;// 5/2;
    mx_holder_wall_v_width_d_offset=0.3; //5/2;

    mx_holder_wall_v_width_r=17.5; //5 //16;
    mx_holder_wall_v_width_l=17.5; //4.5
    mx_holder_wall_v_width_ru=1.5; //5 //16;
    mx_holder_wall_v_width_lu=1.5; //4.5
    mx_holder_wall_v_width_rd=3; //5 //16;
    mx_holder_wall_v_width_ld=3; //4.5
    mx_holder_wall_v_width=5; 
    mx_holder_wall_v_width_r_offset=0;
    mx_holder_wall_v_width_l_offset=0;
    mx_holder_wall_v_width_ru_offset=-mx_holder_wall_v_width_ru; //0.25-(v_unit-17)/2;
    mx_holder_wall_v_width_lu_offset=-mx_holder_wall_v_width_lu; //0.25-(v_unit-17)/2;
    mx_holder_wall_v_width_rd_offset=0; //0.25+(v_unit-17)/2;
    mx_holder_wall_v_width_ld_offset=0; //0.25+(v_unit-17)/2;
    
    mx_holder_wall_height=5; //5

    mx_holder_hook_thickness=0.45; //0.25->0.45 resin test result
    mx_holder_hook_height=1.4;//1.4;     //1.3
    mx_holder_hook_length=16.7; //5;     //2.5
    mx_holder_hook_margin1=3.5;     //3.5
    mx_holder_hook_margin2=mx_holder_hook_margin1+7;     //10.5

    
//    //檢測用軸體14x14x5
//    %translate([h_unit_stb/2,-v_unit_stb/2,(pcb_thickness+5)/2])
//    cube([14,14,5],center=true);

//     
//    echo("pcb_thickness:",pcb_thickness);
//    echo("socket_size:",socket_size);
//    echo("unit_stb:", unit_stb);
//    echo("v_unit_stb:", v_unit_stb);
//    echo("h_unit_stb:", h_unit_stb);
//    echo("mx_socket_size_v",mx_socket_size_v);
//    echo("mx_holder_wall_h_thickness:",mx_holder_wall_h_thickness);
//    echo("mx_holder_wall_h_thickness_add:",mx_holder_wall_h_thickness_add)
     
//上牆
    translate([unit_stb/2+mx_holder_wall_h_width_u_offset, -(v_unit_stb-mx_socket_size_v)/2 + mx_holder_wall_h_thickness/2+mx_holder_wall_v_width_u_offset, (mx_holder_wall_height-5)/2]) 
        cube([mx_holder_wall_h_width_u, mx_holder_wall_h_thickness, pcb_thickness+mx_holder_wall_height-5], center=true);

    //鉤子
    translate([unit_stb/2, -(v_unit_stb-mx_socket_size_v)/2 + mx_holder_wall_h_thickness/2 - mx_holder_hook_thickness/2,(pcb_thickness+mx_holder_hook_height)/2+mx_holder_wall_height-mx_holder_hook_height]) 
     
        cube([mx_holder_hook_length, mx_holder_wall_h_thickness+mx_holder_hook_thickness, mx_holder_hook_height ], center=true);
    
    //支撐
    if (switch_socket_base_holder_support_frame) {

    translate([unit_stb/2 - mx_holder_wall_h_thickness /2 , -(v_unit_stb-mx_socket_size_v)/2 +   mx_holder_wall_h_thickness + mx_holder_wall_support_width/2, (mx_holder_wall_height)/2]) 
    {
        rotate([0,0,90])
        right_triangle(mx_holder_wall_support_width,mx_holder_wall_h_thickness,(mx_holder_wall_height+pcb_thickness),0,0,0);
    }

    }
//下牆
//    translate([h_unit_stb/2+mx_holder_wall_h_width_d_offset, -v_unit_stb/2-mx_holder_wall_h_thickness/2-mx_socket_size_v/2+mx_holder_wall_v_width_d_offset, ((pcb_thickness+mx_holder_wall_height-6)/2)+4]) 
//        cube([mx_holder_wall_h_width_d, mx_holder_wall_h_thickness, pcb_thickness+mx_holder_wall_height-6], center=true);

    //鉤子
    translate([h_unit_stb/2, -v_unit_stb/2-mx_holder_wall_h_thickness/2-mx_socket_size_v/2+mx_holder_hook_thickness/2, (pcb_thickness+mx_holder_hook_height)/2+mx_holder_wall_height-mx_holder_hook_height]) 
     
        cube([mx_holder_hook_length, mx_holder_wall_h_thickness+mx_holder_hook_thickness, mx_holder_hook_height ], center=true);

//支撐
    if (switch_socket_base_holder_support_frame) {
    translate([h_unit_stb/2 + mx_holder_wall_h_thickness/2 , -v_unit_stb/2-mx_holder_wall_h_thickness-mx_socket_size_v/2 -  mx_holder_wall_support_width/2, (mx_holder_wall_height/2)])
    {
        rotate([0,0,-90])
        right_triangle(mx_holder_wall_support_width,mx_holder_wall_h_thickness,(mx_holder_wall_height+pcb_thickness),0,0,0);
    }
}
    
    
    mx_holder_wall_v_offset=0.2;
    mx_holder_wall_support_width=1;
    

//    //右牆
//    translate([(h_unit_stb)/2 + mx_socket_size_h/2 +mx_holder_wall_v_thickness/2, -(v_unit_stb)/2+mx_holder_wall_v_width_r_offset, (mx_holder_wall_height/2)]) {
//        cube([mx_holder_wall_v_thickness,mx_holder_wall_v_width_r,  pcb_thickness+mx_holder_wall_height], center=true);
//    }
//    
//    //左牆
//    translate([(h_unit_stb)/2 - mx_socket_size_h/2 -mx_holder_wall_v_thickness/2 , -(v_unit_stb)/2 +mx_holder_wall_v_width_l_offset, (mx_holder_wall_height/2)]) {
//        cube([mx_holder_wall_v_thickness,mx_holder_wall_v_width_l,  pcb_thickness+mx_holder_wall_height], center=true);
//    }
    
    //右牆-兩側式
    //-(v_unit_stb)/2
    translate([(h_unit_stb)/2 + mx_socket_size_h/2 +mx_holder_wall_v_thickness/2, -mx_holder_wall_v_width_ru/2 +mx_holder_wall_v_width_ru_offset, (mx_holder_wall_height/2)]) {
        cube([mx_holder_wall_v_thickness,mx_holder_wall_v_width_ru,  pcb_thickness+mx_holder_wall_height], center=true);
    }

    translate([(h_unit_stb)/2 + mx_socket_size_h/2 +mx_holder_wall_v_thickness/2, -14 - (mx_holder_wall_v_width_rd/2) -mx_holder_wall_v_width_rd_offset, (mx_holder_wall_height/2)]) {
        cube([mx_holder_wall_v_thickness,mx_holder_wall_v_width_rd-1,  pcb_thickness+mx_holder_wall_height], center=true);
    }
    
    //左牆-兩側式
    //
    translate([(h_unit_stb)/2 - mx_socket_size_h/2 -mx_holder_wall_v_thickness/2 , -(mx_holder_wall_v_width_lu)/2 +mx_holder_wall_v_width_lu_offset, (mx_holder_wall_height/2)]) {
        cube([mx_holder_wall_v_thickness,mx_holder_wall_v_width_lu,  pcb_thickness+mx_holder_wall_height], center=true);
    }
    
    translate([(h_unit_stb)/2 - mx_socket_size_h/2 -mx_holder_wall_v_thickness/2 ,-14 -(mx_holder_wall_v_width_ld)/2 - mx_holder_wall_v_width_ld_offset, (mx_holder_wall_height/2)]) {
        cube([mx_holder_wall_v_thickness,mx_holder_wall_v_width_ld-1,  pcb_thickness+mx_holder_wall_height], center=true);
    }

 
/////

    translate([h_unit_stb/2,-v_unit_stb/2,0]) 
    //    difference() {
    union() {
        cube([socket_size, socket_size, pcb_thickness], center=true);
        translate([0,0,border_z_offset ])
            border(
                [socket_size,socket_size], 
                borders, 
                pcb_thickness-2, 
                h_border_width, 
                v_border_width
            );
    }
}

module switch_socket_base_mx_stabilizer2(borders=[1,1,1,1]) {
    //MX軸的定位板為方形14mm的空間
    //因此模擬溝槽的部分，應該是夾起來要14mm
    //也就是牆厚與鉤子寬度不論怎麼設定，都要讓空間保留14mm
    //頂多少0.5mm做為緩衝
    //
    //stabilizer 用的版本
    
    //多0.5是預留給卡榫的空間
    mx_socket_size_v =14.5; //+0.25;
    mx_socket_size_h =14; //+0.25;

    
    mx_holder_wall_h_thickness_add=0.3;
    mx_holder_wall_v_thickness_add=0;
    
    //socket_size=15
    mx_holder_wall_h_thickness=15-mx_socket_size_v+mx_holder_wall_h_thickness_add;
    
    mx_holder_wall_v_thickness=15-mx_socket_size_h+mx_holder_wall_v_thickness_add;
    
    mx_holder_wall_h_width_u=14; //5 //10;
    mx_holder_wall_h_width_d=14; //5 //10;
    mx_holder_wall_h_width=10; 
    mx_holder_wall_h_width_u_offset=0.1;// 5/2;
    mx_holder_wall_h_width_d_offset=0.1; //5/2;
    mx_holder_wall_v_width_u_offset=-0.1;// 5/2;
    mx_holder_wall_v_width_d_offset=-0.1; //5/2;

    mx_holder_wall_v_width_r=17.5; //5 //16;
    mx_holder_wall_v_width_l=17.5; //4.5
    mx_holder_wall_v_width_ru=2; //5 //16;
    mx_holder_wall_v_width_lu=2; //4.5
    mx_holder_wall_v_width_rd=3; //5 //16;
    mx_holder_wall_v_width_ld=3; //4.5
    mx_holder_wall_v_width=5; 
    mx_holder_wall_v_width_r_offset=0;
    mx_holder_wall_v_width_l_offset=0;
    mx_holder_wall_v_width_ru_offset=-mx_holder_wall_v_width_ru+0.6; //0.25-(v_unit-17)/2;
    mx_holder_wall_v_width_lu_offset=-mx_holder_wall_v_width_lu+0.6; //0.25-(v_unit-17)/2;
    mx_holder_wall_v_width_rd_offset=1.1; //0.25+(v_unit-17)/2;
    mx_holder_wall_v_width_ld_offset=1.1; //0.25+(v_unit-17)/2;
    
    mx_holder_wall_height=5; //5

    mx_holder_hook_thickness=0.45; //0.25->0.45 resin test result
    mx_holder_hook_height=1.4;//1.4;     //1.3
    mx_holder_hook_length=13.8; //5;     //2.5
    mx_holder_hook_margin1=3.5;     //3.5
    mx_holder_hook_margin2=mx_holder_hook_margin1+7;     //10.5

    
//    //檢測用軸體14x14x5
//    %translate([h_unit_stb/2,-v_unit_stb/2,(pcb_thickness+5)/2])
//    cube([14,14,5],center=true);

     
//上牆
    translate([unit_stb/2+mx_holder_wall_h_width_u_offset, -(v_unit_stb-mx_socket_size_v)/2 + mx_holder_wall_h_thickness/2+mx_holder_wall_v_width_u_offset, (mx_holder_wall_height)/2]) 
        cube([mx_holder_wall_h_width_u, mx_holder_wall_h_thickness, pcb_thickness+mx_holder_wall_height], center=true);

    //鉤子
    translate([unit_stb/2, -(v_unit_stb-mx_socket_size_v)/2 + mx_holder_wall_h_thickness/2 - mx_holder_hook_thickness/2,(pcb_thickness+mx_holder_hook_height)/2+mx_holder_wall_height-mx_holder_hook_height]) 
     
        cube([mx_holder_hook_length, mx_holder_wall_h_thickness+mx_holder_hook_thickness, mx_holder_hook_height ], center=true);
    
    //支撐
    if (switch_socket_base_holder_support_frame) {
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
